gokcesena53/usb-pd-power-supply/hardware/docs/reports/task-095-20260928/bottom.png

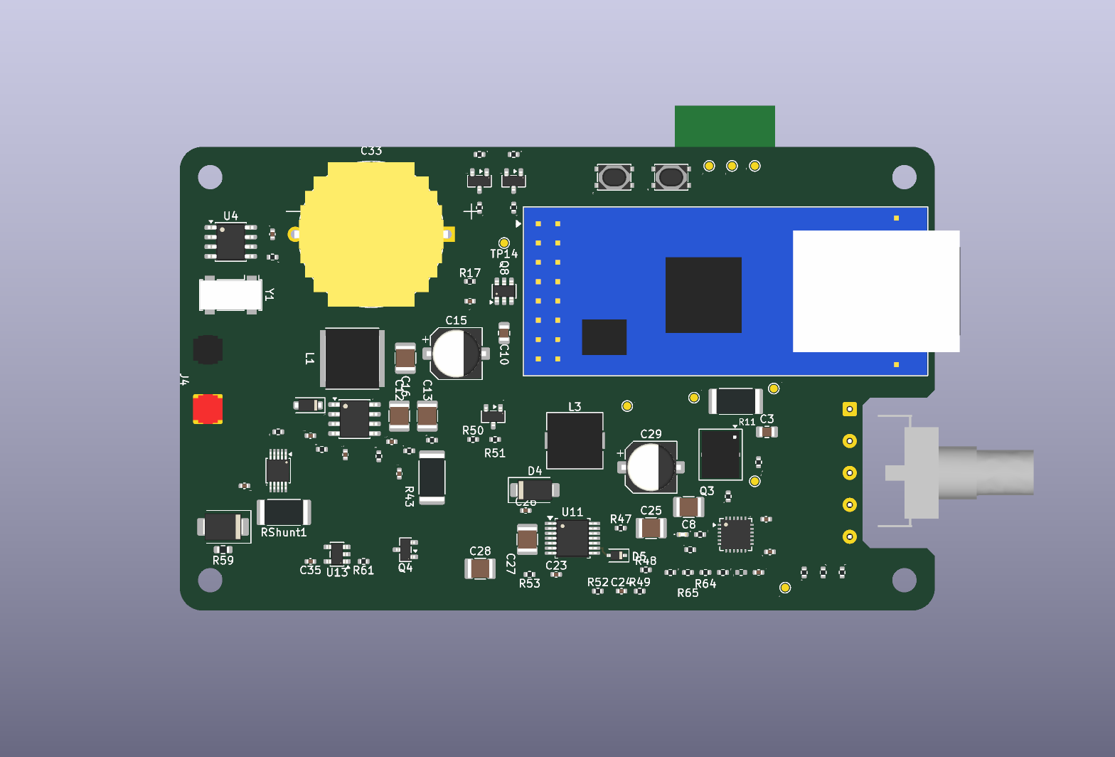
hardware/docs/reports/task-095-20260928/bottom.png
