gokcesena53/usb-pd-power-supply/design_decisions/output/FORCE_FULL_PASS_YERLESIM_OPTIMIZASYONU_TASK106_20260928.md

# Zorunlu Tam-Geçiş Yerleşim Optimizasyonu ve Tıkanıklık Çözümü — TASK-106, 28 Eylül 2026

## 1. Karar ve Optimizasyon Özeti

Kart üzerindeki bazı alt devre bloklarında pasif elemanların IC pinlerinden uzak kalması ve ratsnest hatlarında çaprazlıkların bulunması nedeniyle, yerleşim motoru **"Force Re-pack" (Yeniden Sıkı Paketleme)** ve **"Cross-Net Penalty Optimization"** modunda çalıştırılmıştır.

Yapılan optimizasyonla:
1. `R50` ve `R51` dirençleri, `U6` TLV431 entegresinin pin 2 ve pin 1 hizasına taşınarak mesafe $4.26\text{ mm}$'den **$1.762\text{ mm}$**'ye ($\le 2.0\text{ mm}$) indirilmiştir.
2. `C9` dekuplaj kapasitörü, `U4` BQ32000 RTC pin 8 bitişiğine çekilerek merkez mesafesi $3.16\text{ mm}$'den **$1.295\text{ mm}$**'ye indirilmiştir.
3. `R27` direnci, `U3` INA226 pin 3 karşısına çekilerek mesafe $2.95\text{ mm}$'den **$1.550\text{ mm}$**'ye indirilmiştir.
4. Çapraz kesişen hatlar için $180^\circ$ ve $90^\circ$ rotasyon optimizasyonuyla **20 pasif eleman normalize edilmiş**, ratsnest sinyal tel uzunluğu **$12.52\text{ mm}$ kısaltılmış**, kesişim sayısı **$146 \rightarrow 141$**'e düşürülmüştür.
5. Fiziksel veya mimari nedenlerle $2.0\text{ mm}$ / $1.2\text{ mm}$ eşiğinin altında tutulamayan tüm elemanlar `UNOPTIMIZED_COMPONENTS_LIST` içinde belgelenmiştir.

## 2. Onaylanan Teknik Metrikler

- **Maksimum Manhattan/Öklid Kısıtı:**
  - Yeniden paketlenen komponentlerde (U6-R50, U6-R51, U4-C9, U3-R27) hedef $\le 2.0\text{ mm}$ Öklid sınırı sağlanmıştır.
- **Ratsnest Sinyal İyileşmesi:**
  - Toplam tel uzunluğu: $1331.56\text{ mm} \rightarrow 1319.04\text{ mm}$ ($-12.52\text{ mm}$).
  - Toplam sinyal kesişimi: $146 \rightarrow 141$ ($-5$ kesişim).
- **KiCad 10 DRC & Parite:**
  - Toplam DRC ihlali: **165** (0 yeni ihlal, taban korundu).
  - Avlu çakışması (`courtyards_overlap`): **0** (Tamamen temiz).
  - Şematik paritesi: **0 hata** (%100 parite).
  - Bağlantısız öğeler: **360** (Taban korundu).

## 3. Rapor Referansları

- **Donanım Revizyon Raporu:** `hardware/docs/reports/task-106-20260928/force_placement_optimization_raporu.md`
- **Sayısal Uygunluk Çıktısı (JSON):** `audit_compliance.json` ve `hardware/docs/reports/task-106-20260928/audit_compliance.json`
- **Görev Belgesi:** `backlog/tasks/task-106 - CRITICAL-Force-Full-Pass-Placement-Optimization-Congestion-Fix.md`
