gokcesena53/usb-pd-power-supply/design_decisions/output/LM74801_YERLESIM_TASK074_20260924.md

# LM74801 çıkış anahtarı ve ideal diyot grubu ilişkisel yerleşimi — TASK-074, 24 Eylül 2026

LM74801 çıkış anahtarı ve ideal diyot grubunun 10 footprint üyesi (U12, Q5, C30–C32,
D6, R54–R56, R58) F.Cu katmanında ortak source (common-source) topolojisi, gate sürme,
dV/dt yumuşak açılış, charge pump kapasitesi ve çıkış gücü akışına göre ilişkisel
olarak yerleştirildi. On footprint'in grup üyeliği, UUID, pad/net bağlantıları ve
F.Cu yüzü korundu. Kart dışındaki geçici blok alanı (x≈105–123, y≈52–66 mm)
korunmuştur; nihai kart içine taşıma ve genel routing TASK-085/TASK-008 kapsamındadır.

[Önce görünüm](../../hardware/docs/reports/task-074-20260924/before.svg) ·
[Sonra ve koridorlar](../../hardware/docs/reports/task-074-20260924/after.svg) ·
[KiCad F.Cu katman çıktısı](../../hardware/docs/reports/task-074-20260924/board-top.svg) ·
[x/y/açı/yüz ve pad ölçümleri](../../hardware/docs/reports/task-074-20260924/verification.json)

## Kaynak, pin ve yerleşim kuralı

- **Texas Instruments LM7480-Q1 (SNOSD95C, Nisan 2020 – Rev. Aralık 2020, s. 35–36):**
  1. *İdeal diyot katı (§12.1):* U12 Pin 1 (`DGATE`), Pin 2 (`A` / `SRC_COMMON`) ve
     Pin 12 (`C` / `SW_OUT`) doğrudan Q5B MOSFET'inin GATE (Pin 4), SOURCE (Pins 1,3)
     ve DRAIN (Pins 5,6) uçlarına yakın bağlandı (U12.1–Q5.4 mesafesi 3,94 mm;
     U12.2–Q5.3 5,02 mm; U12.12–Q5.5 7,68 mm).
  2. *Yük ayırma / load disconnect katı (§12.1):* U12 Pin 8 (`GATE_DRV` / HGATE) ve
     Pin 9 (`OUT` / `SRC_COMMON`) doğrudan Q5A MOSFET'inin GATE (Pin 2) ve SOURCE
     (Pins 1,3) uçlarına bağlandı (U12.8–Q5.2 mesafesi 9,09 mm).
  3. *Ortak Source yapılandırması (Şekil 12-2, Common Source Configuration):*
     Q5 0° yönlendirmesinde üst yarıda termal drain padleri (sol Drain A: pins 7,8
     `PD_VBUS_SENSED`; sağ Drain B: pins 5,6 `SW_OUT`), alt yarıda leaded bacaklar
     (Pin 1 SRC, Pin 2 HGATE, Pin 3 SRC, Pin 4 DGATE) bulunur. Gate ve source
     bağlantıları yüksek akım drain dökümlerinin dışından bağımsız çıkarıldı.
  4. *Decoupling ve Charge Pump (§12.1):*
     - C32 (100 nF, 0402): U12 Pin 10 (`V_PRE`) ve Pin 7 (`GND`) hemen bitişiğine
       yerleştirildi (pad merkezleri 3,40 mm ve 2,57 mm).
     - C31 (220 nF, 0603): U12 Pin 11 (`CAP`) ve Pin 10 (`V_PRE`) arasında charge
       pump kapasitesidir. TI kuralı gereğince MOSFET gövdesinin ısısından
       etkilenmemesi için U12'nin sağ tarafına (Q5'in uzağına) yerleştirildi
       (pad merkezleri 3,67 mm ve 3,21 mm).
  5. *Gate Kırpma / Zener Koruması:* D6 (BZT52C12 SOD-123) Q5A Gate (Pin 2) ile
     Common Source (Pin 1) arasına bağlandı (D6.1–Q5.2 5,48 mm; D6.2–Q5.1 2,79 mm).
     Katot `GATE_DRV`'de, anot `SRC_COMMON`'da VGS gerilimini 12 V ile sınırlar.
  6. *Yumuşak Açılış (Soft-Start dV/dt):* R54 (1 kΩ) ve C30 (22 nF) Q5A Gate hattına
     bağlandı; C30 referans yazısı lehim maskesi açıklığına basmayacak şekilde
     alt boşluğa ayarlandı.
  7. *Aşırı Gerilim ve Enable:* R55 (237 kΩ) ve R56 (10 kΩ) gerilim bölücüsü U12.5
     (`OV_SENSE`) girişine; R58 (100 kΩ) pull-down direnci U12.6 (`SW_EN`) girişine
     yerleştirildi.
  8. *Termal Pad:* U12 altındaki EP (RTN, Pin 13) datasheet gereğince boştadır,
     GND'ye bağlanmaz.

| Alt Devre / Koridor | Elemanlar ve Pad/Net Yönü |
| --- | --- |
| Güç Girişi (Q5A) | `PD_VBUS_SENSED` sol taraftan Q5 Pins 7,8 Drain A dökümüne girer. |
| Ortak Source | Q5A ve Q5B Pins 1,3 `SRC_COMMON` ortak ara düğümüdür. |
| Güç Çıkışı (Q5B) | Q5 Pins 5,6 Drain B `SW_OUT` dökümünden sağa doğru INA226/J4 yönüne çıkar. |
| DGATE Sürüşü | U12.1 → Q5.4 (`DGATE`) ideal diyot hızlı anahtarlama yolu (3,94 mm). |
| HGATE Sürüşü & dV/dt | U12.8 → Q5.2 (`GATE_DRV`), D6 Zener koruması ve R54–C30 yumuşak açılış devresi. |
| Kaynak ve Katot Algılama | U12.2/9 → Q5.1/3 (`SRC_COMMON`); U12.12 → Q5.5/6 (`SW_OUT`). |
| Besleme & Charge Pump | C32 (121,5; 58,0) `V_PRE` bypass; C31 (122,0; 54,5) `CAP`–`VS` charge pump. |
| Mantık & Algılama | R55/R56 `OV_SENSE` bölücüsü ve R58 `SW_EN` pull-down direnci U12 altına yerleştirildi. |

## Komşuluk, yüz seçimi ve devir notları

1. **Güç Akışı:**
   - Giriş: Sol taraftan `PD_VBUS_SENSED` (pre-boost U11 / buck U5 hatlarından).
   - Çıkış: Sağ tarafa `SW_OUT` (INA226 akım şöntü R1 ve J4 panel çıkış konnektörüne).
2. **Yüz Seçimi Koordinasyonu (TASK-065 Devri):**
   - Bu blok başlangıç olarak `F.Cu` katmanında tutuldu.
   - TASK-085 / TASK-008'de kart içine taşınırken INA226 grubunun B.Cu'da olduğu ve LCD
     izdüşüm alanının (x=63,52…141,62; y=72,28…127,72 mm) top zarf kısıtları göz önüne
     alınarak, gerekirse INA226 ile birlikte alt yüze (B.Cu) flip edilmesi incelenmelidir.

## Doğrulama

- `kicad-cli pcb drc --schematic-parity`:
  - **DRC ihlalleri:** **146 → 146** (yeni courtyard, clearance, short, edge veya mask ihlali: **0**).
  - **Bağlantısız öğeler:** **360 → 360** (tamamlanmamış genel routing envanteri korundu).
  - **Schematic parity:** **0 → 0**.
- **Courtyard kontrolü:** 10 eleman arasında minimum courtyard aralığı **0,350 mm** (Q5–D6 arası); çakışma **0**.
- **Ankrajlar ve izler:** J7, J3, J9, H1–H4, D5, U11 konum/açı/yüz ankrajları ve mevcut iz UUID'leri tamamen korundu.

Kanıt dosyaları:
- [DRC önce](../../hardware/docs/reports/task-074-20260924/drc-before.json)
- [DRC sonra](../../hardware/docs/reports/task-074-20260924/drc-after.json)
- [Doğrulama ve pad ölçüm verileri](../../hardware/docs/reports/task-074-20260924/verification.json)
- [Yerleşim betiği](../../hardware/docs/reports/task-074-20260924/place.py)
- [Doğrulama betiği](../../hardware/docs/reports/task-074-20260924/verify.py)
