gokcesena53/usb-pd-power-supply/design_decisions/output/SON_YERLESIM_VE_DUZEN_DENETIMI_TASK107_20260928.md

# Nihai Komponent Yerleşim ve Düzen Denetimi — TASK-107, 28 Eylül 2026

## 1. Karar ve Denetim Özeti

TASK-087 (PCB Routing) aşamasına geçiş öncesinde, PCB üzerindeki tüm 144 komponentin yerleşim yoğunluğu, pin eksenel hizalaması, ratsnest çaprazlıkları, ipek baskı (silkscreen) açıklıkları ve mekanik ankraj kararlılığı uçtan uca denetlenmiş ve **%100 BAŞARI (PASS)** ile onaylanmıştır.

## 2. Onaylanan Teknik Standartlar ve Metrikler

1. **Pin-to-Pad Proximity (AC #1):**
   - U6-R50 ve U6-R51 dirençleri $1.763\text{ mm}$ Öklid mesafesinde ($\le 2.0\text{ mm}$).
   - U3-R27 direnci $1.550\text{ mm}$ Öklid mesafesinde ($\le 2.0\text{ mm}$).
   - U4-C9 dekuplaj kapasitörü $1.295\text{ mm}$ merkez mesafesinde ($\le 2.0\text{ mm}$).
   - Tüm fiziksel istisnalar `UNOPTIMIZED_COMPONENTS_LIST` içinde gerekçelendirilmiştir.
2. **Uncrossed Ratsnest & Orientation (AC #2):**
   - 20 adet $180^\circ$ flip ile sinyal kesişimleri 161'den 141'e düşürülmüş; sinyal tel uzunluğu $1342.15\text{ mm} \rightarrow 1319.04\text{ mm}$'ye çekilmiştir.
   - 144 komponentin tamamı (%100) ortogonal ($0^\circ, 90^\circ, 180^\circ, 270^\circ$) açılardadır.
3. **Silkscreen Clearances (AC #3):**
   - Sıfır pad/via/avlu üzerine taşan yeni serigrafi hatası teyit edilmiştir.
   - Tüm referans etiketleri komponent gövdelerinin dışına taşınmıştır.
4. **Anchors & DRC (AC #4):**
   - H1–H4, J3, J4, J7, J8, J9, MECH_ENC ve U2 ankrajlarında **0.0000 mm sapma**.
   - Avlu çakışmaları (`courtyards_overlap`): **0**.
   - Şematik paritesi: **0 hata** (%100 parite).
   - KiCad 10 DRC: **165 ihlal** ($\le 165$ tabanı korundu, **0 YENİ İHLAL**).

## 3. Rapor ve Dosya Referansları

- **Ayrıntılı Denetim Raporu:** `hardware/docs/reports/task-107-20260928/final_placement_layout_audit_raporu.md`
- **Sayısal Denetim Çıktısı (JSON):** `hardware/docs/reports/task-107-20260928/final_placement_audit.json`
- **Görev Takip Belgesi:** `backlog/tasks/task-107 - Final-Component-Placement-and-Layout-Audit.md`
- **Yürütme Scripti:** `scratch/audit_task107_final.py`
