gokcesena53/usb-pd-power-supply/design_decisions/output/TPS55340_YERLESIM_TASK072_20260924.md

# TPS55340 ilişkisel yerleşimi — TASK-072, 24 Eylül 2026

U11, D5 ve aralarındaki mevcut `BOOST_FB` izi ankraj olarak kaldı. Diğer 14
grup üyesi B.Cu üzerinde güç ve hassas sinyal sırasına göre düzenlendi.
Blok hâlâ TASK-067'nin kart dışı geçici alanındadır; kart içindeki son konum
ve yeni güç izleri bu kararın parçası değildir.

[Önce](../../hardware/docs/reports/task-072-20260924/before.svg) ·
[Sonra ve ayrılmış koridorlar](../../hardware/docs/reports/task-072-20260924/after.svg) ·
[Ölçüm ve x/y/açı/yüz envanteri](../../hardware/docs/reports/task-072-20260924/verification.json)

## Üretici kuralı ve uygulama

Kaynak: [TI TPS55340 veri sayfası SLVSBD4E, §10.1–10.3, s. 28,
Şekil 10-1](https://www.ti.com/lit/ds/symlink/tps55340.pdf).
Şekil 10-1 QFN pin dizilimini gösterir; bu karttaki U11 HTSSOP-14'tür.
Bu yüzden pin numaraları şekilden alınmadı; PCB'deki gerçek pad/netler
esas alındı. TASK-069'un tüm gruplar için kaynak tablosu henüz yoktur;
bu gruba ait kaynak ve ankraj denetimi burada yapıldı.

| TI kuralı | PCB karşılığı / doğrulama |
| --- | --- |
| SW iz uzunluğu ve alanı küçük; regülatörün altında GND düzlemi | L3.1 (72,75;42,50), D4.2 (72,80;49,00), U11.1/2 (72,712;53,39/54,04) aynı B.Cu koridorunda. SW için x≈72–74 mm, y≈42–54 mm ayrıldı; genişliğini bitmiş routing belirleyecek. İç GND düzlemi korunmalı, SW bakırı FB tarafına genişletilmemeli. |
| İç FET–D4–Cout yüksek akım döngüsünü kısalt | D4.1 V_PRE (76,80;49,00) → C27.1 V_PRE (75,80;54,025) pad merkezleri 5,12 mm. C27.2 GND (75,80;56,975) → U11 termal GND dönüşü için B.Cu alanı ayrıldı. C28.1 V_PRE (83,475;64,00) ikinci çıkış deposudur; mevcut U6/R50/R51/C16 alanı nedeniyle uzak kaldı. C28'in güç bağlantısı TASK-073 ile yeniden kontrol edilmeli. |
| VIN bypass'u VIN/AGND'a yakın | C26.1 PD_VOUT (76,48;51,70) → U11.3 VIN (72,712;54,69) pad merkezleri 4,81 mm. C26.2 GND'den U11.15/GND'a kısa dönüş ve via alanı ayrıldı. C25/C29 daha büyük giriş depolarıdır; C29.1 (62,20;46,00) → L3.2 (66,35;42,50) 5,43 mm. Bu uzaklıklar TI'nin sayısal limitleri değil, bu yerleşimin ölçümleridir. |
| AGND/PGND ve PowerPAD aynı katmanda doğrudan bağlanır; termal via kullanılır | U11.6/7/11–14 ve 15 GND. U11 altındaki B.Cu GND alanı ve termal via dizisi için yer bırakıldı. Via/zone henüz eklenmedi; delik çapı, maske ve lehim emilmesi routing/üretim kontrolünde seçilmeli. |
| FB ve COMP'ı anahtarlama alanından uzak tut | U11.8 COMP (66,987;57,29) → R52/C24 ağı sol-alt çıkışta; U11.9 FB (66,987;56,64) → D5.2 ve R48/R49 sol-alt tarafta. SW koridoru sağ/üstte. R47 FREQ ve C23 SS de sinyal tarafında. Sessiz GND dönüşü U11.11–14/15'e yönelir; L3/D4 SW üzerinden geçmez. |

Yukarıdaki oklar **planlanan koridorlardır**, tamamlanmış bakır izi değildir.
SW, giriş, V_PRE ve GND yüksek akım alanları B.Cu'da tutulmalı; via dizisi
yalnızca dağıtım/termal dönüşte kullanılmalıdır. Diyot D4.2 SW, D4.1 V_PRE;
D5.2 BOOST_FB anot, D5.1 EN_CTRL katot. Polarite ve pad netleri şemayla
aynı kaldı.

## Buck sınırı ve sessiz dönüş

D5.1 EN_CTRL x=62,97; y=57,60'tan U6.2 x=80,885; y=54,602 ve R50.1
x=82,185; y=60,57 yönüne gider. D5–U11 FB izinin yanında güç SW bakırı
geçirilmez. EN_CTRL/V_X ve R50/R51/U6 REF düğümü buck grubunun hassas
tarafıdır; TASK-073 bu elemanları hareket ettirirse D5.1'e ayrılan üst/sağ
koridor ve U11 GND'den ayrı sessiz referans dönüşü birlikte kontrol edilmeli.
R43'ün V_PRE/EN_CTRL bağlantısı ve ısıl alanı buck grubuna aittir.

## Kontrol ve sınırlar

- D5.2–U11.9 aynı dört UUID'li B.Cu segmentiyle via olmadan bağlı:
  **2,584607 mm ≤10 mm**. U11/D5 ve segmentler yerinden oynatılmadı.
- Grup 16 üye, grup adı, footprint UUID, pad/net listesi ve B.Cu yüzü korundu.
  J3/J9/H1–H4 sabit ankrajlarına dokunulmadı.
- `kicad-cli pcb drc --schematic-parity`: önce/sonra **146/146** ihlal,
  **360/360** bağlantısız öğe, **0/0** şema eşleşme hatası. Yeni courtyard,
  clearance, kısa devre veya mask köprüsü yok. 146 mevcut ihlal: 63 yazı
  yüksekliği, 63 yazı kalınlığı, 15 drill aralığı, 4 J7 hole clearance,
  1 D10 silk over copper. Bağlantısız 360 öğe, genel routing henüz
  tamamlanmadığı için ayrı tutuldu.
- C27 yakın çıkış deposuna rağmen C28'in pad'i D4'ten uzakta. TASK-073
  buck yerleşimi ve TASK-085 toplu denetiminde güç dönüş alanı ile C28
  konumu tekrar değerlendirilmeli. Nihai kısa akım döngüsü routed PCB'de
  ölçülmeden TI yerleşim önerisinin tamamlandığı söylenemez.

Kanıt: [DRC önce](../../hardware/docs/reports/task-072-20260924/drc-before.json),
[DRC sonra](../../hardware/docs/reports/task-072-20260924/drc-after.json),
[doğrulama betiği](../../hardware/docs/reports/task-072-20260924/verify.py).
