gokcesena53/usb-pd-power-supply/design_decisions/logs/PROMPT_steplayout-critical-routing_20260912_233540.md

AOZ1284PI buck power-stage placement and routing; USB-C to dual-output 5 A path; R11 and INA228 Kelvin sense routing; zones refilled; DRC 0 violations.
