gokcesena53/usb-pd-power-supply/design_decisions/output/TASARIM_RAPORLARI_20260911.md

# Tasarım dokümanları

11 Eylül 2026 — Güncel teslim paketi

- [TÜM BAĞLANTI KONTROLÜ VE MÜHENDİSLİK AÇIKLAMASI](C:/Users/Slayer/Desktop/masaüstü%20güç%20kaynağı/output/pdf/TUM_BAGLANTI_KONTROLU_20260911.pdf)
- [00_DEGISIKLIK_RAPORU](C:/Users/Slayer/Desktop/masaüstü%20güç%20kaynağı/output/pdf/bloklar-20260911/00_DEGISIKLIK_RAPORU.pdf)
- [01_USB_C_INPUT](C:/Users/Slayer/Desktop/masaüstü%20güç%20kaynağı/output/pdf/bloklar-20260911/01_USB_C_INPUT.pdf)
- [02_USB_PD_CONTROLLER](C:/Users/Slayer/Desktop/masaüstü%20güç%20kaynağı/output/pdf/bloklar-20260911/02_USB_PD_CONTROLLER.pdf)
- [03_MCU](C:/Users/Slayer/Desktop/masaüstü%20güç%20kaynağı/output/pdf/bloklar-20260911/03_MCU.pdf)
- [04_RTC_BATTERY](C:/Users/Slayer/Desktop/masaüstü%20güç%20kaynağı/output/pdf/bloklar-20260911/04_RTC_BATTERY.pdf)
- [05_TFT](C:/Users/Slayer/Desktop/masaüstü%20güç%20kaynağı/output/pdf/bloklar-20260911/05_TFT.pdf)
- [06_ENCODER](C:/Users/Slayer/Desktop/masaüstü%20güç%20kaynağı/output/pdf/bloklar-20260911/06_ENCODER.pdf)
- [07_POWER_GENERATION](C:/Users/Slayer/Desktop/masaüstü%20güç%20kaynağı/output/pdf/bloklar-20260911/07_POWER_GENERATION.pdf)
- [08_POWER_SENSING](C:/Users/Slayer/Desktop/masaüstü%20güç%20kaynağı/output/pdf/bloklar-20260911/08_POWER_SENSING.pdf)
- [09_POWER_OUTPUT](C:/Users/Slayer/Desktop/masaüstü%20güç%20kaynağı/output/pdf/bloklar-20260911/09_POWER_OUTPUT.pdf)
- [Güncel BOM — Excel](C:/Users/Slayer/Desktop/masaüstü%20güç%20kaynağı/output/BOM_PRELIMINARY_20260911.xlsx)
- [Güncel BOM — CSV](C:/Users/Slayer/Desktop/masaüstü%20güç%20kaynağı/output/BOM_PRELIMINARY_20260911.csv)
- [PCB katman kararı, küçültme planı ve BOM durumu](C:/Users/Slayer/Desktop/masaüstü%20güç%20kaynağı/output/LAYOUT_VE_BOM_DURUMU_20260911.md)
- [PCB yerleşim revizyonu 1](C:/Users/Slayer/Desktop/masaüstü%20güç%20kaynağı/output/PCB_YERLESIM_REV1_20260912.md)
- [PCB layout uygulama yol haritası](C:/Users/Slayer/Desktop/masaüstü%20güç%20kaynağı/output/PCB_LAYOUT_YOL_HARITASI_20260912.md)
- [KiCad 10 layout adım adım uygulama rehberi](C:/Users/Slayer/Desktop/masaüstü%20güç%20kaynağı/output/KICAD10_LAYOUT_ADIM_ADIM_20260912.md)

## Açık tasarım konuları

- IRF7855 / AP33772S gate sürüş uyumluluğu.
- TFT arka ışığı için regüle akım kaynağı.
- Buck L/D ve bias koşulu doğrulanmış MLCC MPN seçimi.
- PCB boş: bakır, RF, ısıl, yerleşim ve DRC doğrulaması yapılmadı.
- Birincil CR2032: RTC trickle charge kapalı olmalı.
- Üretim BOM'u için sarı satırlardaki kesin üretici parça numaraları ve MLCC DC-bias doğrulaması kapanmalı.
