gokcesena53/usb-pd-power-supply/design_decisions/reports/layout-20260911/gnd-routing-correction-report.md

# GND Routing Correction Report

Date: 2026-09-13

## Corrected items

- Removed 214 user-added GND routing segments that formed long daisy-chain return paths on F.Cu.
- Restored and retained the 16 short local GND traces used by the AOZ1284PI buck power stage and its control network.
- Added a GND copper zone on F.Cu with 0.25 mm clearance.
- Retained the existing GND zones on GND_PLANE and B.Cu.
- Added local 0.60/0.30 mm GND vias around the main IC, USB, ESP32, RTC/TFT and power clusters.
- Removed temporary grid vias so the remaining signal routes are not obstructed.
- Final GND via count: 48.
- Changed the USB-C J1 footprint GND zone connection to solid fill so its B1/B12 pads connect without starved thermal spokes.
- The ESP32 antenna copper keepout remains active on all copper layers.
- AOZ1284PI exposed pad remains on PD_VOUT/VIN; it was not connected to GND.

## Verification

- Final DRC: 0 errors, 0 warnings.
- No GND entries remain in the unconnected-item report.
- The board still has 131 unrouted items on non-GND nets. These are the remaining layout work and are not DRC shorts or clearance failures.

## Next routing stage

Place R2/R3 as a matched USB pair near ESP32-C6 USB pins, then route USB_DP/USB_DM over a continuous GND reference. Route +3.3V distribution and local decoupling next. General GND stitching should be finalized only after all signal routes are complete.
