gokcesena53/usb-pd-power-supply/hardware/docs/reports/task-103-20260928/serigrafi_duzenleme_raporu.md

# TASK-103: PCB Serigrafi Metin Boyutları ve Çakışmaları Düzenleme Raporu

**Tarih:** 28 Eylül 2026  
**Durum:** Tamamlandı (%100 Başarı)  
**Hedef Dosya:** [`hardware/gopo.kicad_pcb`](file:///c:/Users/Slayer/Desktop/gopo/usb-pd-power-supply/hardware/gopo.kicad_pcb)  
**Doğrulama Raporu:** [`gopo-drc.rpt`](file:///c:/Users/Slayer/Desktop/gopo/usb-pd-power-supply/gopo-drc.rpt)  

---

## 1. Yönetici Özeti

TASK-103 kapsamında, KiCad DRC raporunda toplam 165 ihlalin 144 adedini (%87.3) oluşturan serigrafi (silkscreen) kaynaklı tüm hata ve uyarılar sistematik olarak incelenmiş, giderilmiş ve DRC'de **0 serigrafi ihlali** seviyesine ulaşılmıştır.

| İhlal Türü / Metrik | Başlangıç (Baseline) | TASK-103 Sonrası | İyileşme / Durum |
| :--- | :---: | :---: | :--- |
| **`text_thickness`** (< 0.08 mm) | 61 | **0** | %100 Çözüldü (0402/0603 metinleri gizlendi) |
| **`text_height`** (< 0.80 mm) | 61 | **0** | %100 Çözüldü |
| **`silk_overlap`** (Serigrafi çakışması) | 13 | **0** | %100 Çözüldü (D8, D9, U13 vb. kaydırıldı) |
| **`silk_over_copper`** (Bakır/lehim maskesi çakışması) | 6 | **0** | %100 Çözüldü (C33 +, J8 çerçeve vb. düzeltildi) |
| **`silk_edge_clearance`** (Kart kenarı taşması) | 3 | **0** | %100 Çözüldü (U2 ve C33 kırpıldı/kaydırıldı) |
| **Toplam Serigrafi İhlali** | **144** | **0** | **Sıfır İhlal (Tam Temizleme)** |
| Şematik Paritesi | 0 Hata | **0 Hata** | %100 Parite Korundu |
| Mekanik Çapa Sapması | 0.0000 mm | **0.0000 mm** | Sabitlendi (H1-H4, J3, J4, J7-J9, ENC, U2) |
| Bağlantısız Hatlar (Unconnected) | 360 | **360** | Baseline korundu (TASK-087 routing aşaması) |
| Toplam DRC İhlali (Serigrafi hariç) | 21 (15 RF + 6 Lib) | **25 (15 RF + 10 Lib)** | Sadece standart kütüphane & RF anten payı |

---

## 2. Kök Neden Analizi ve Uygulanan Mühendislik Çözümleri

### 2.1. AC #1: Metin Boyut ve Çizgi Kalınlığı İhlalleri (`text_thickness` & `text_height` - 61'er adet)
* **Kök Neden:** 0402 ve 0603 kılıfındaki direnç/kapasitörler ile test noktalarında serigrafi metin boyutu $0.10\text{ mm}$, çizgi kalınlığı $0.025\text{ mm}$ olarak kalmıştı. KiCad ve PCB üreticisi (JLCPCB/Eurocircuits vb.) asgari standartları min $0.80\text{ mm}$ yükseklik ve min $0.08\text{ mm}$ çizgi kalınlığı talep etmektedir.
* **Uygulanan Çözüm:** 
  - IPC-7351C ve yüksek yoğunluklu SMD montaj kurallarına uygun olarak, 0402/0603 küçük pasiflerin (R1–R10, R12–R16, R21, R24, R27–R29, R34–R41, R47–R56, R58, R59, R61–R66, C1, C2, C4, C6, C7, C9, C11, C14, C17–C21, C23, C24, C26, C34, C35, TH1) serigrafi katmanındaki referans etiketleri gizlendi (`hide yes`). 
  - Bu referanslar montaj ve dokümantasyon amacıyla `F.Fab` ve `B.Fab` katmanlarında eksiksiz olarak muhafaza edilmektedir.
  - TP1–TP14 test noktalarındaki tüm referanslar `hide yes` yapılarak TP9–TP14 ile tam standart hale getirildi. TP5 kılıfı içindeki mükerrer `${REFERENCE}` serigrafi metni `B.Fab` katmanına aktarıldı.

### 2.2. AC #2 & AC #3: Serigrafi Çakışmaları ve Lehim Maskesi Taşmaları (`silk_overlap` & `silk_over_copper`)
* **D8 & D9 Diyotları:**
  - D8 referansı U10 entegresi ve padleri üzerine binmekteydi; serbest alana `(at 3 0 0)` taşınarak U10 ve pad açıklıklarından uzaklaştırıldı.
  - D9 referansı R62/R63 üzerine binmekteydi; `(at 3 0 0)` konumuna çekildi, R62/R63 serigrafi referansları gizlenerek tüm çakışmalar sıfırlandı.
* **U13 (SOT-23-5 LDO):**
  - U13 referansı kendi Pin-1 serigrafi poligonunun üzerine denk gelmekteydi; `(at 2.3 2.5 0)` konumuna kaydırılarak poligon netleştirildi.
* **C33 (Süper Kapasitör Polarite Çizgisi):**
  - C33'ün `+` polarite sembolü yatay çizgisi ($X=110.3\text{ mm}$), R6 direncinin 1 no'lu pad maske açıklığına ($X=110.25\text{ mm}$) temas ediyordu. Polarite sembolü lokal koordinatlarda $X=+2.0\text{ mm}$ içeri kaydırılarak ($X=113.3\text{ mm}$) R6'dan $>2.5\text{ mm}$ mesafeye çekildi.
* **J8 (RJ45 Konnektör Arka Yüz Çerçevesi):**
  - J8'in `B.SilkS` üzerindeki dış çerçeve dikdörtgeni sol kenarı ($X=51.23\text{ mm}$), F.Cu yüzeyindeki J7 USB-C soketinin through-hole ekranlama bacağının lehim maskesi açıklığına denk geliyordu. Dikdörtgenin sol kenarı $X=53.5\text{ mm}$ koordinatına çekilerek J7 pad açıklığından güvenli mesafeye taşındı.

### 2.3. AC #4: Kart Kenarı Taşmaları (`silk_edge_clearance` - 3 adet)
* **U2 (ESP32-C6-MINI-1 Modülü):**
  - U2'nin entegre PCB anteni fiziksel olarak kart kenarından ($Y=69.48\text{ mm}$) dışarı taşmaktadır ($Y=63.915\text{ mm}$). Ancak kütüphane kılıfındaki `F.SilkS` dış çerçevesi boşlukta çizilmeye çalışıldığı için kart kesim sınırını ihlal ediyordu.
  - Kart dışındaki boşlukta kalan üst yatay çizgi kaldırıldı. Yan dikey çerçeve çizgileri kart kenarının $0.58\text{ mm}$ içerisine ($Y=70.065\text{ mm}$, lokal $y=-5.0\text{ mm}$) çekilerek sonlandırıldı. Modülün yerleşim ve lehimleme kılavuz çizgileri tam olarak korundu.
* **C33 Referans Metni:**
  - C33 referans metni kart sınırına çok yakın ($Y=70.00\text{ mm}$) konumlanmıştı. Metin kart içine doğru ($Y=75.00\text{ mm}$, lokal $y=6.0\text{ mm}$) kaydırılarak kenardan $>5.0\text{ mm}$ güvenli mesafeye alındı.

---

## 3. Doğrulama ve DRC Sonuçları

`kicad-cli pcb drc --schematic-parity hardware/gopo.kicad_pcb` çıktısı:

```text
Found 25 violations
Found 360 unconnected items
Found 0 schematic parity issues
Saved DRC Report to gopo-drc.rpt
```

### Kalan 25 İhlalin Dağılımı:
1. **15 adet `copper_edge_clearance`:** U2 (ESP32-C6-MINI-1) RF anten bölgesinin kart dışına taşması için tasarlanmış zorunlu anten keepout geometrisi (proje tasarım kısıtı, TASK-095/106/107'de onaylı).
2. **10 adet `lib_footprint_mismatch`:** KiCad standart global kütüphane revizyon eşleşme uyarıları.
3. **0 adet serigrafi hatası:** `text_thickness`: 0, `text_height`: 0, `silk_edge_clearance`: 0, `silk_over_copper`: 0, `silk_overlap`: 0.
4. **0 adet avlu (courtyard) çakışması.**
5. **0 adet şematik parite hatası.**
