gokcesena53/usb-pd-power-supply/backlog/tasks/task-013 - C33-footprintini-numune-ile-dogrula.md

---
id: TASK-013
title: C33 footprint'ini numune ile doğrula
status: To Do
assignee: []
created_date: '2026-09-22 18:46'
updated_date: '2026-09-22 19:15'
labels:
  - sample-eval
milestone: m-1
dependencies: []
priority: medium
ordinal: 120000
---

## Acceptance Criteria
<!-- AC:BEGIN -->
- [ ] #1 Korchip_DCL_H-Type footprint'i numuneye uyuyor
<!-- AC:END -->

## Definition of Done
<!-- DOD:BEGIN -->
- [ ] #1 Kanıt (ERC/netlist/ölçüm/commit) Implementation Notes'a yazıldı
- [ ] #2 Karar değiştiyse design_decisions/ ve CHANGES.TXT güncellendi
<!-- DOD:END -->
