gokcesena53/usb-pd-power-supply/backlog/tasks/task-016 - 5-V-profilde-AOZ1284-TPS55340-kararliligini-olc.md

---
id: TASK-016
title: 5 V profilde AOZ1284 + TPS55340 kararlılığını ölç
status: To Do
assignee: []
created_date: '2026-09-22 18:46'
updated_date: '2026-09-22 19:15'
labels:
  - bring-up
milestone: m-2
dependencies:
  - TASK-015
references:
  - design_decisions/USB_PD_REV_C_tasarim_kararlari_handoff.md
ordinal: 123000
---

## Acceptance Criteria
<!-- AC:BEGIN -->
- [ ] #1 Tam yükte iki regülatör kararlı
- [ ] #2 Attach anında USB_VBUS efektif kapasitesi ≤10 uF
<!-- AC:END -->

## Definition of Done
<!-- DOD:BEGIN -->
- [ ] #1 Kanıt (ERC/netlist/ölçüm/commit) Implementation Notes'a yazıldı
- [ ] #2 Karar değiştiyse design_decisions/ ve CHANGES.TXT güncellendi
<!-- DOD:END -->
