gokcesena53/usb-pd-power-supply/backlog/tasks/task-017 - 3.3-V-PPSte-V_PRE-regulasyonunu-ve-boost-kararliligini-olc.md

---
id: TASK-017
title: 3.3 V PPS'te V_PRE regülasyonunu ve boost kararlılığını ölç
status: To Do
assignee: []
created_date: '2026-09-22 18:46'
updated_date: '2026-09-22 19:15'
labels:
  - bring-up
milestone: m-2
dependencies:
  - TASK-015
references:
  - design_decisions/USB_PD_REV_C_tasarim_kararlari_handoff.md
ordinal: 124000
---

## Acceptance Criteria
<!-- AC:BEGIN -->
- [ ] #1 Tam dahili yükte V_PRE 5.02 V'ta regüle
- [ ] #2 Boost döngüsü kararlı
<!-- AC:END -->

## Definition of Done
<!-- DOD:BEGIN -->
- [ ] #1 Kanıt (ERC/netlist/ölçüm/commit) Implementation Notes'a yazıldı
- [ ] #2 Karar değiştiyse design_decisions/ ve CHANGES.TXT güncellendi
<!-- DOD:END -->
