gokcesena53/usb-pd-power-supply/backlog/tasks/task-018 - Pass-through-bolgesinde-TPS55340in-anahtarlamadigini-dogrula.md

---
id: TASK-018
title: Pass-through bölgesinde TPS55340'ın anahtarlamadığını doğrula
status: To Do
assignee: []
created_date: '2026-09-22 18:46'
updated_date: '2026-09-22 19:15'
labels:
  - bring-up
milestone: m-2
dependencies:
  - TASK-015
ordinal: 125000
---

## Acceptance Criteria
<!-- AC:BEGIN -->
- [ ] #1 5.5–28 V aralığında SW pininde anahtarlama yok
- [ ] #2 FB < 3 V (hesapta 28 V'ta ~2.43 V)
<!-- AC:END -->

## Definition of Done
<!-- DOD:BEGIN -->
- [ ] #1 Kanıt (ERC/netlist/ölçüm/commit) Implementation Notes'a yazıldı
- [ ] #2 Karar değiştiyse design_decisions/ ve CHANGES.TXT güncellendi
<!-- DOD:END -->
