gokcesena53/usb-pd-power-supply/backlog/tasks/task-021 - Cikis-anahtari-acilisinda-VBUS-tepe-gerilimini-olc.md

---
id: TASK-021
title: Çıkış anahtarı açılışında VBUS tepe gerilimini ölç
status: To Do
assignee: []
created_date: '2026-09-22 18:46'
updated_date: '2026-09-22 19:15'
labels:
  - bring-up
milestone: m-2
dependencies:
  - TASK-015
ordinal: 128000
---

## Acceptance Criteria
<!-- AC:BEGIN -->
- [ ] #1 28 V EPR, 3 A yükte USB_VBUS / PD_VOUT tepe < 34 V
<!-- AC:END -->

## Definition of Done
<!-- DOD:BEGIN -->
- [ ] #1 Kanıt (ERC/netlist/ölçüm/commit) Implementation Notes'a yazıldı
- [ ] #2 Karar değiştiyse design_decisions/ ve CHANGES.TXT güncellendi
<!-- DOD:END -->
