gokcesena53/usb-pd-power-supply/hardware/docs/reports/flow-space-plan-20260928/placement-plan.png

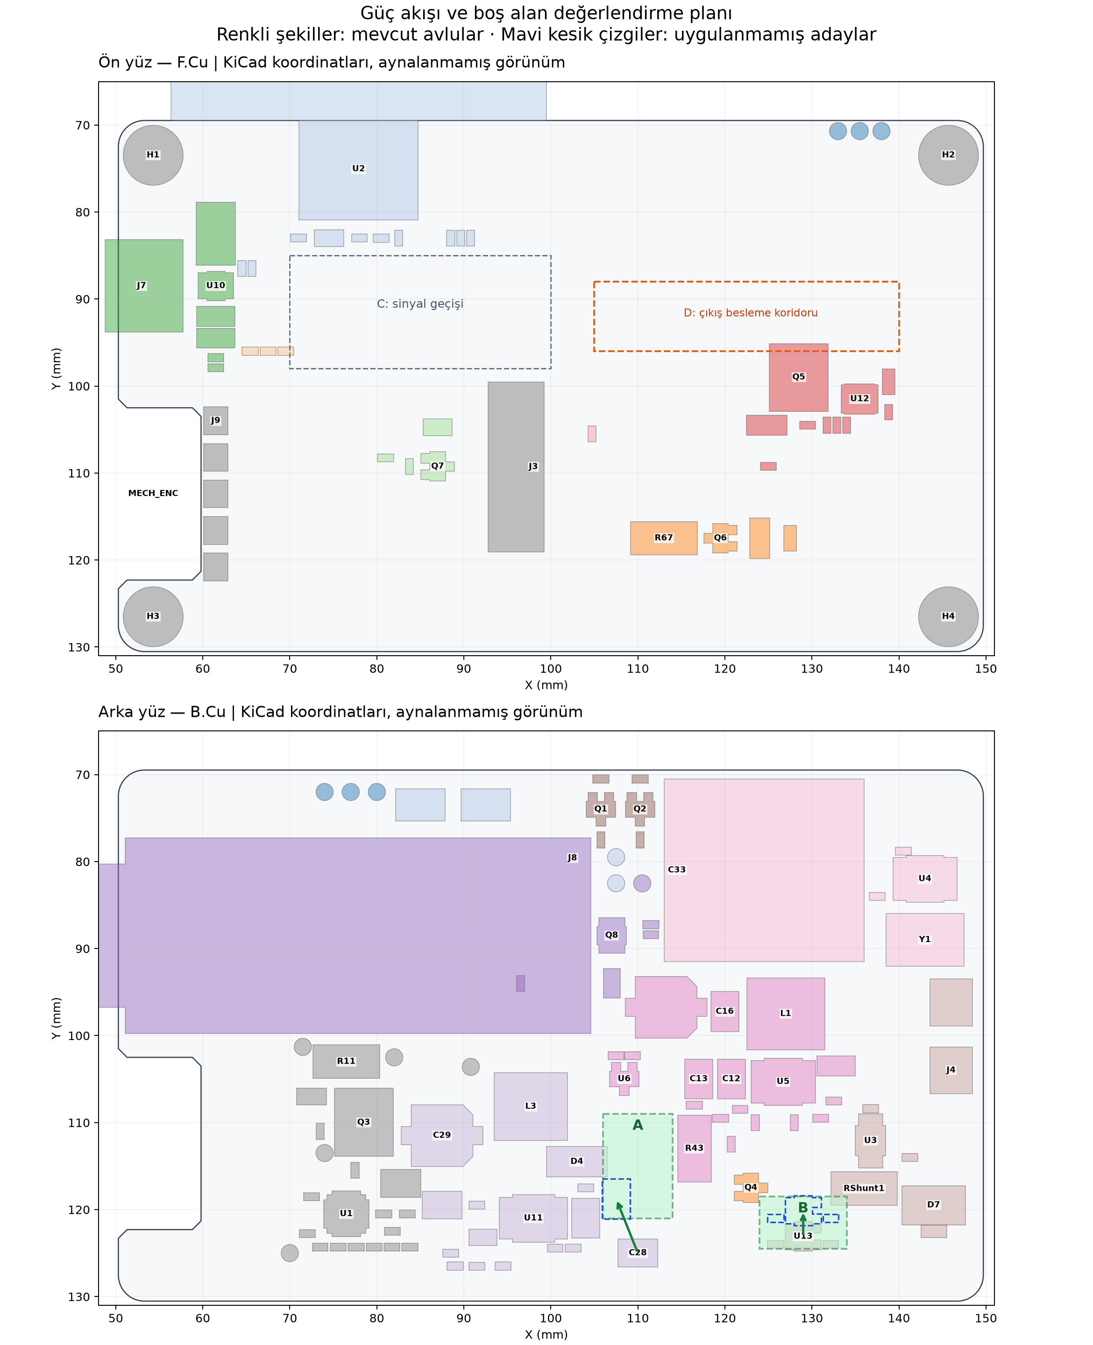
hardware/docs/reports/flow-space-plan-20260928/placement-plan.png
