gokcesena53/usb-pd-power-supply/hardware/docs/reports/flow-space-plan-20260928/top.png

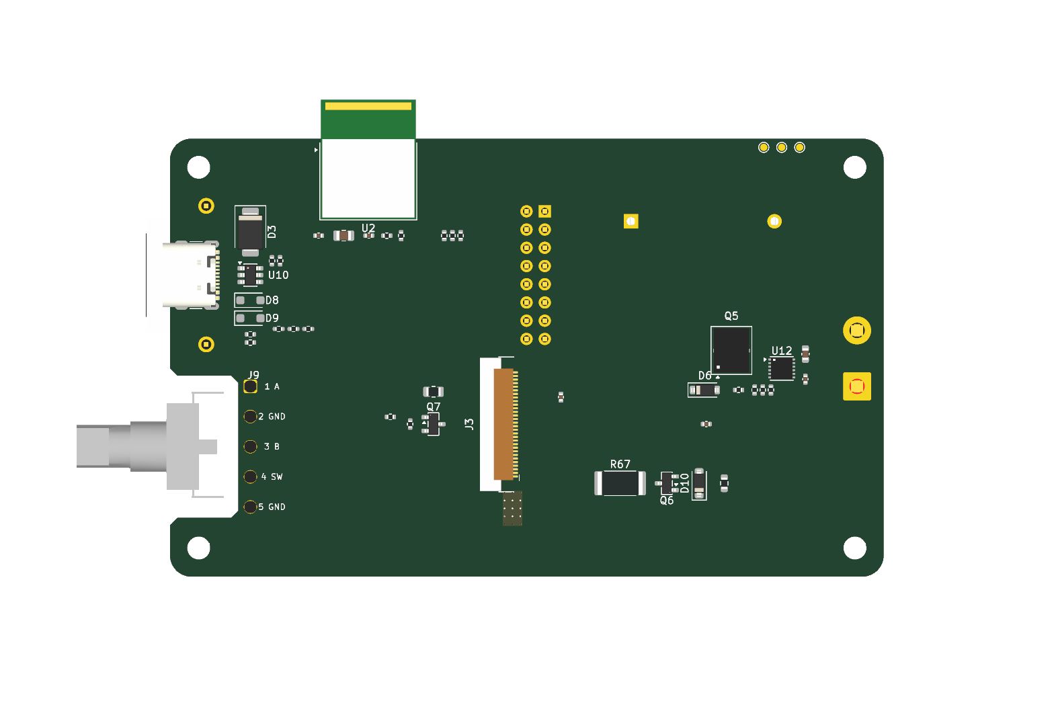
hardware/docs/reports/flow-space-plan-20260928/top.png
