gokcesena53/usb-pd-power-supply/hardware/docs/reports/freerouting-20260929/A_fpc-bot.png

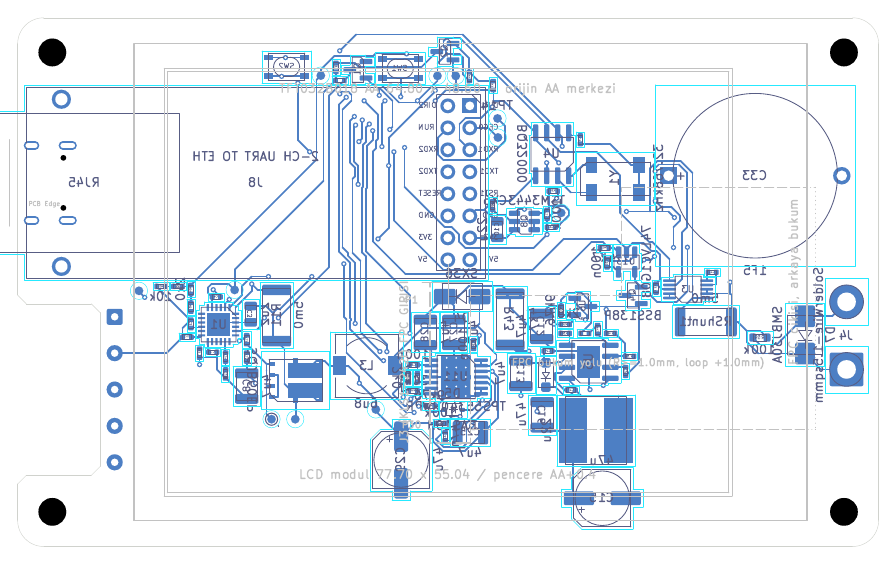
hardware/docs/reports/freerouting-20260929/A_fpc-bot.png
