gokcesena53/usb-pd-power-supply/hardware/docs/reports/freerouting-20260929/B_seed41-bot.png

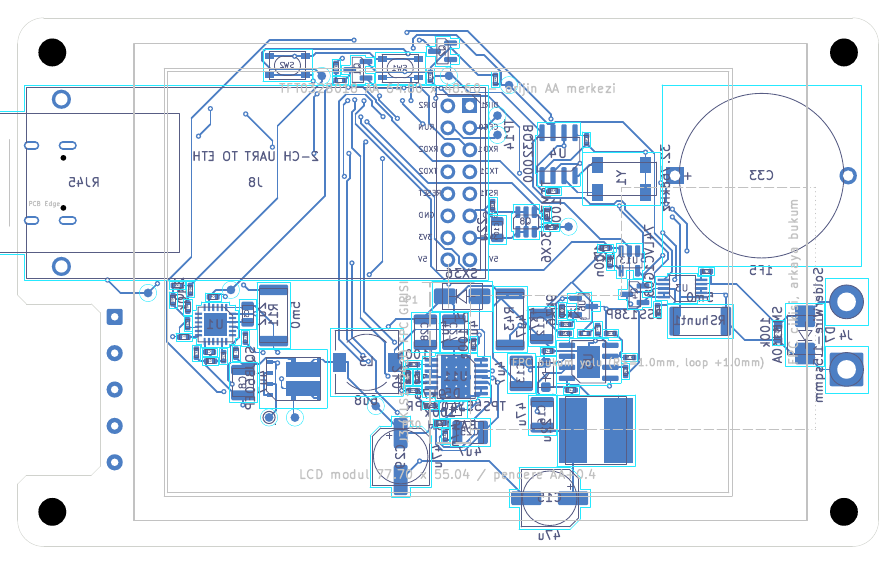
hardware/docs/reports/freerouting-20260929/B_seed41-bot.png
