gokcesena53/usb-pd-power-supply/hardware/docs/reports/freerouting-20260929/B_seed41-top.png

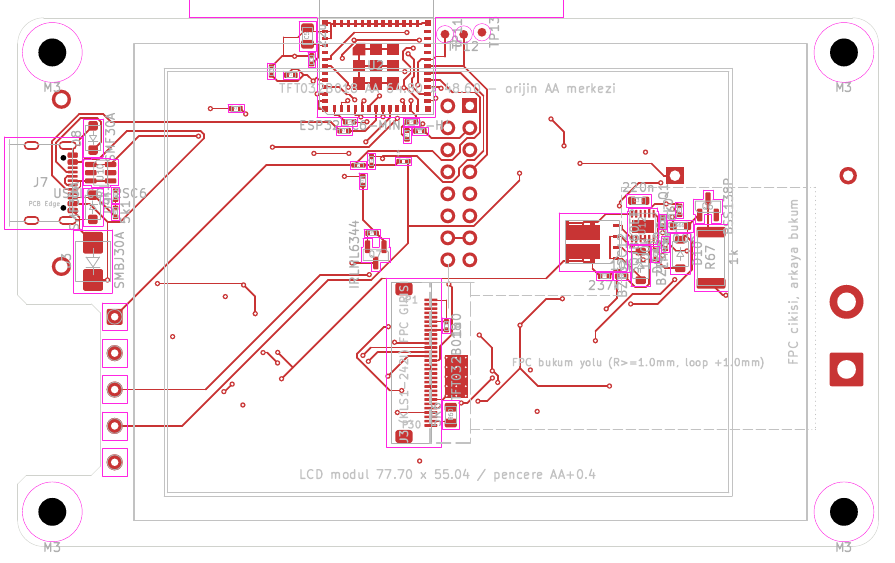
hardware/docs/reports/freerouting-20260929/B_seed41-top.png
