gokcesena53/usb-pd-power-supply/hardware/docs/reports/placement-lns-20260929/cand-bot.png

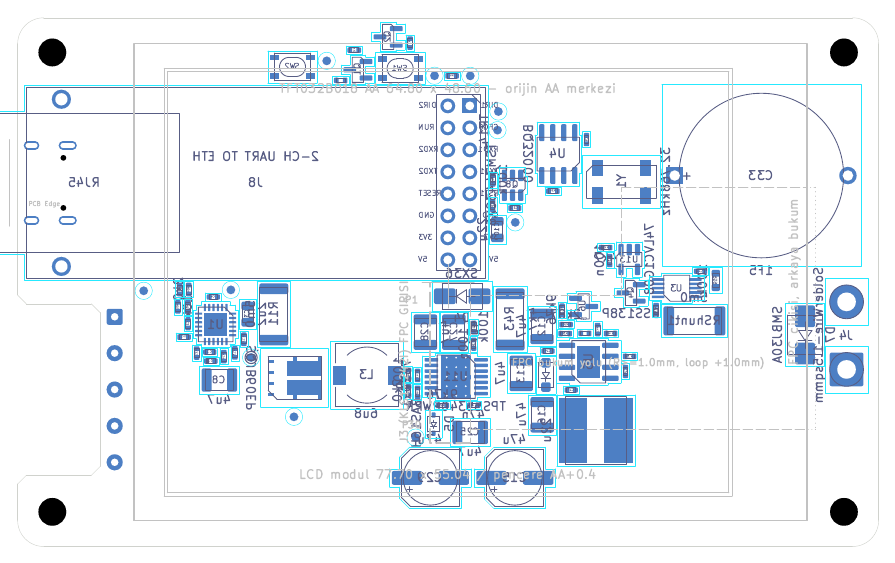
hardware/docs/reports/placement-lns-20260929/cand-bot.png
