gokcesena53/usb-pd-power-supply/hardware/docs/reports/placement-scratch-20260929/after-bottom.png

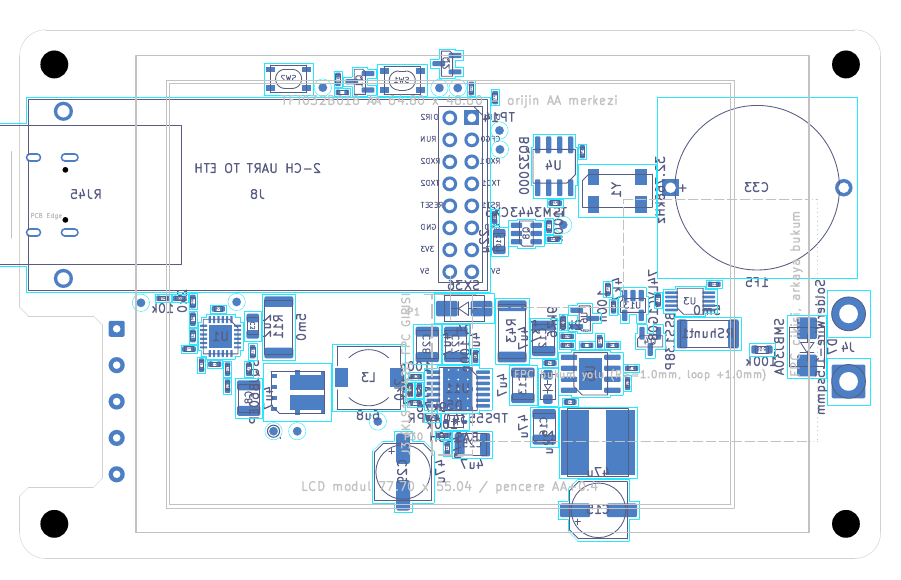
hardware/docs/reports/placement-scratch-20260929/after-bottom.png
