gokcesena53/usb-pd-power-supply/hardware/docs/reports/placement-scratch-20260929/before-bottom.png

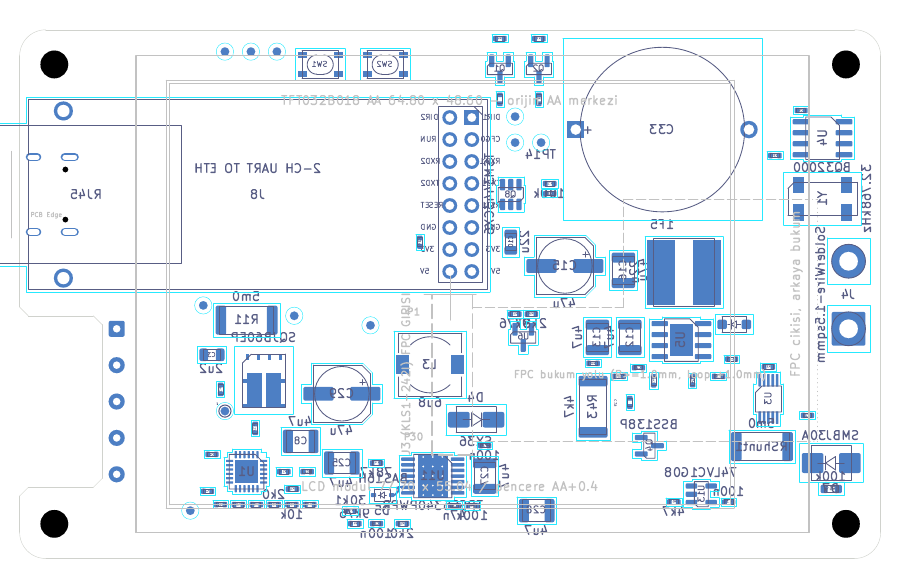
hardware/docs/reports/placement-scratch-20260929/before-bottom.png
