gokcesena53/usb-pd-power-supply/hardware/docs/reports/placement-scratch-20260929/before-top.png

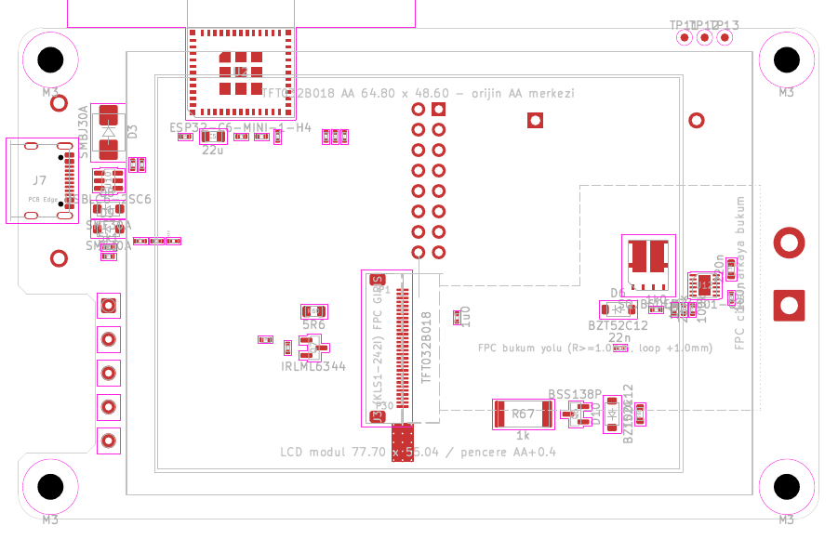
hardware/docs/reports/placement-scratch-20260929/before-top.png
