gokcesena53/usb-pd-power-supply/hardware/docs/reports/task-065-20260924/bottom-3d.png

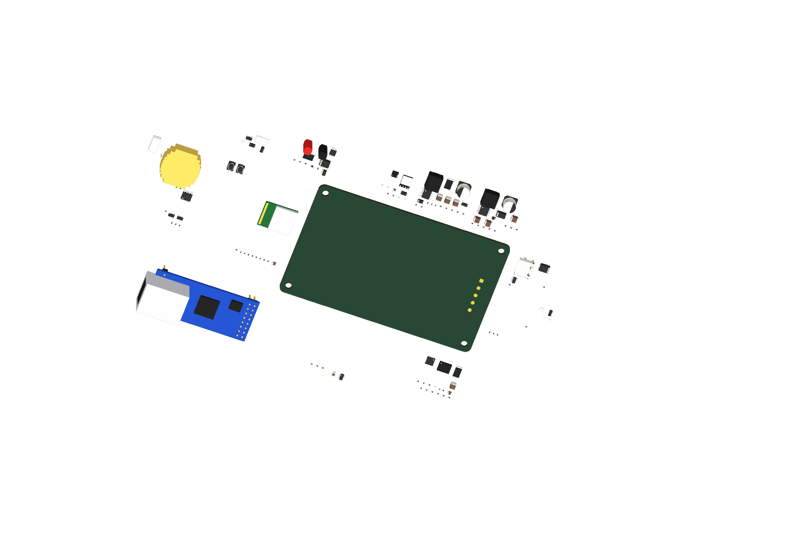
hardware/docs/reports/task-065-20260924/bottom-3d.png
