gokcesena53/usb-pd-power-supply/hardware/docs/reports/task-065-20260924/j3-datasheet.png

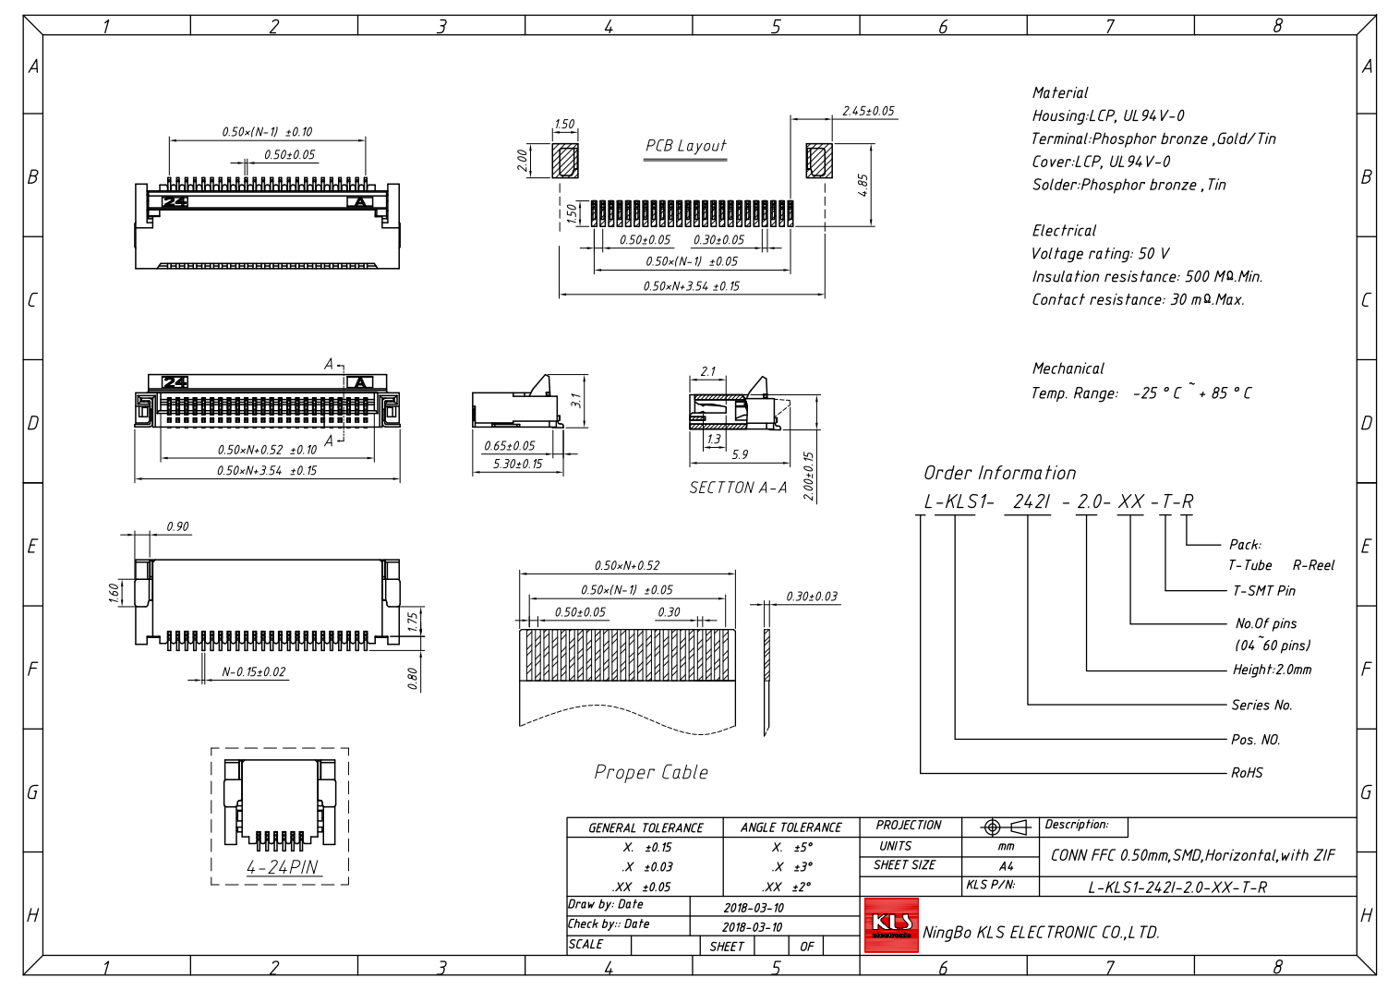
hardware/docs/reports/task-065-20260924/j3-datasheet.png
