gokcesena53/usb-pd-power-supply/hardware/docs/reports/task-066-20260924/schematic-encoder.png

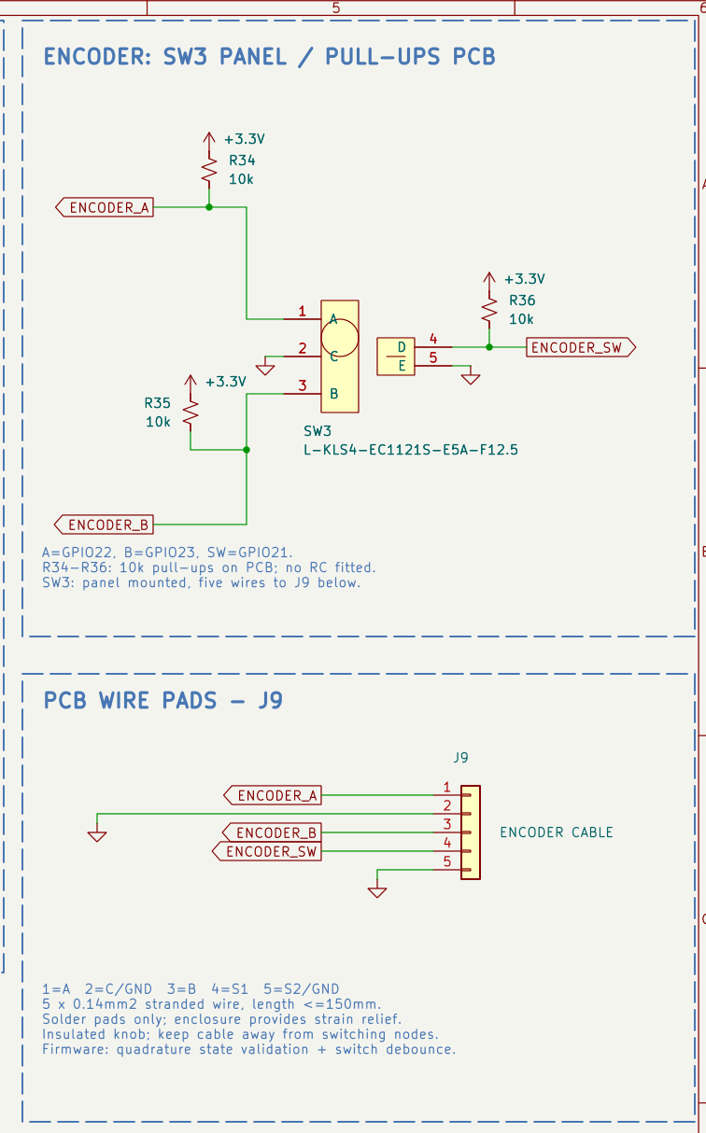
hardware/docs/reports/task-066-20260924/schematic-encoder.png
