gokcesena53/usb-pd-power-supply/hardware/docs/reports/task-094-20260925/datasheet-landscape.png

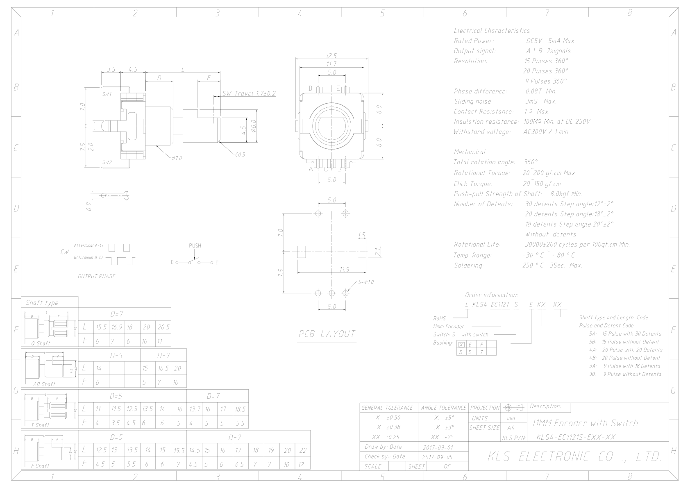
hardware/docs/reports/task-094-20260925/datasheet-landscape.png
