gokcesena53/usb-pd-power-supply/hardware/docs/reports/task-097-20260928/bottom_rc_audit.png

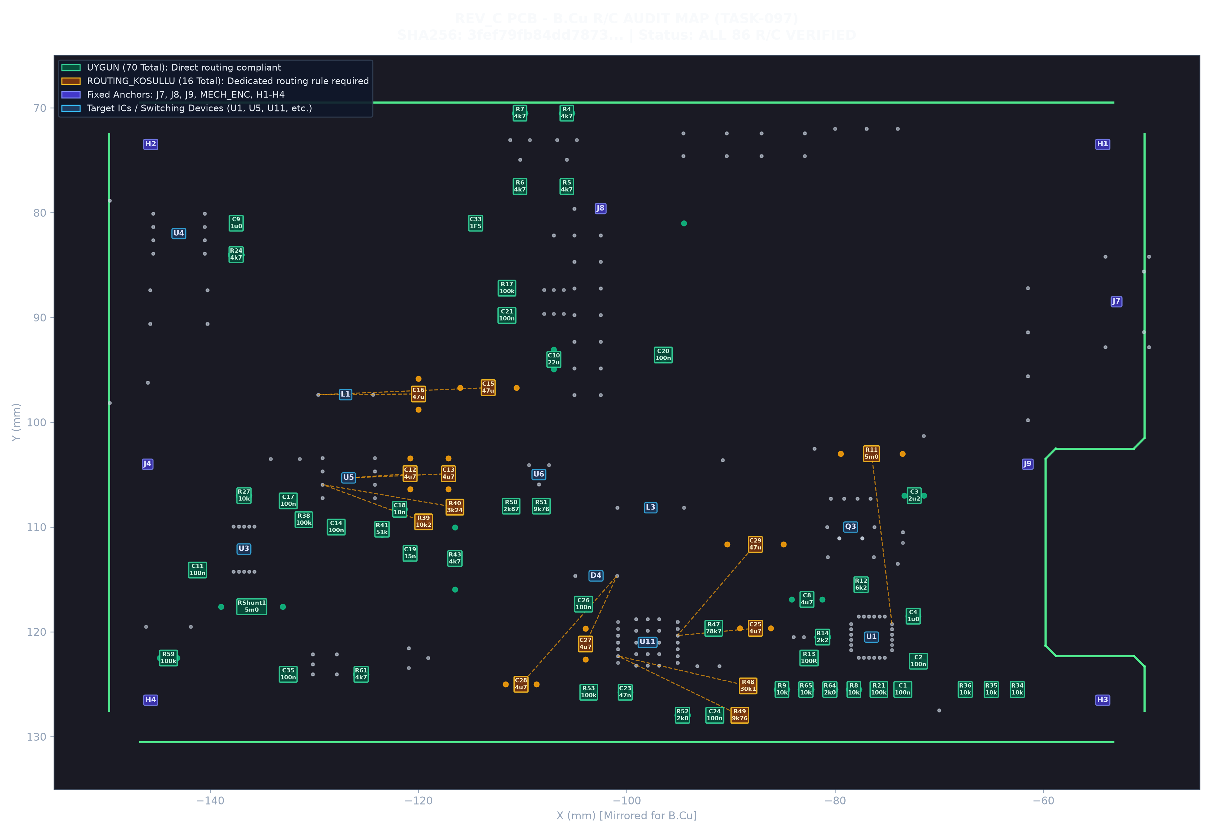
hardware/docs/reports/task-097-20260928/bottom_rc_audit.png
