gokcesena53/usb-pd-power-supply/hardware/images/reports/backlight-20260911/UI-final.png

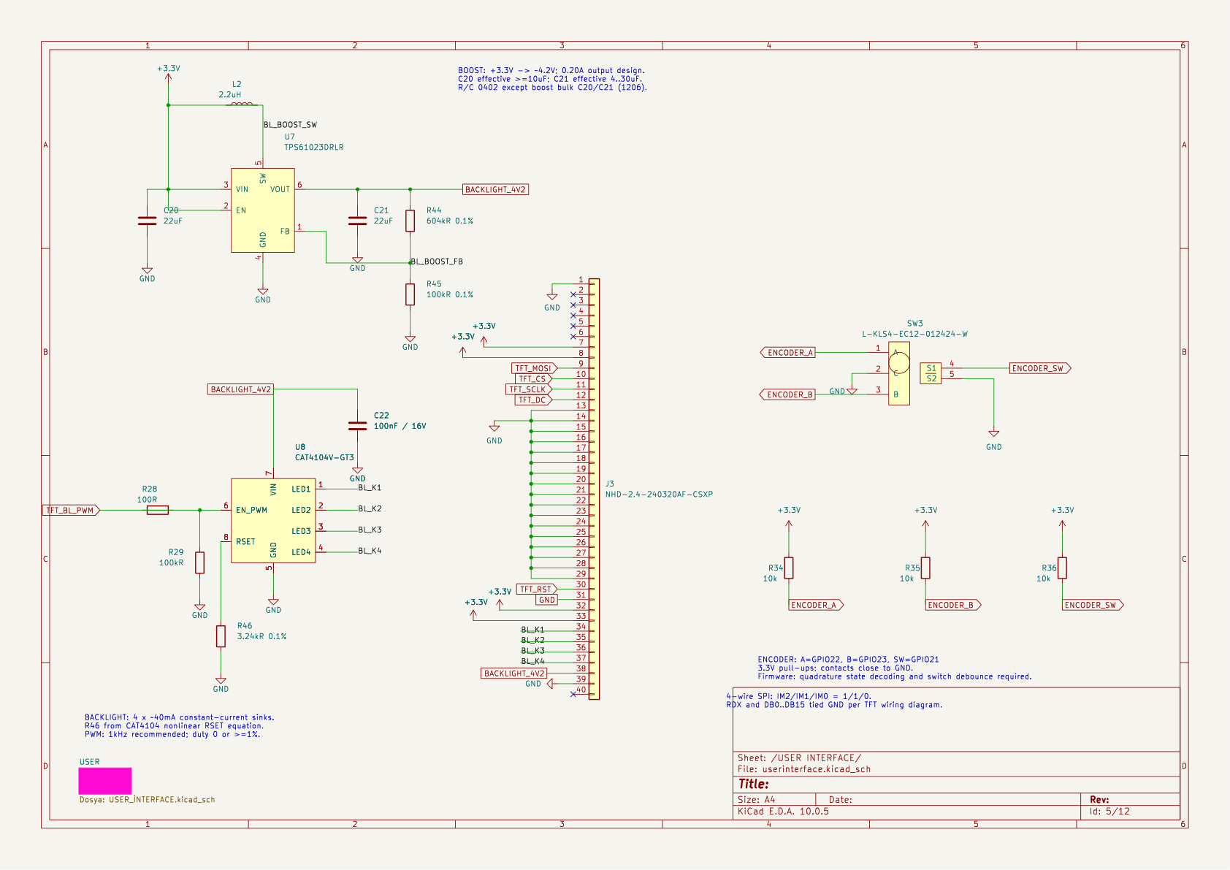
hardware/images/reports/backlight-20260911/UI-final.png
