gokcesena53/usb-pd-power-supply/hardware/images/reports/backlight-20260911/UI.png

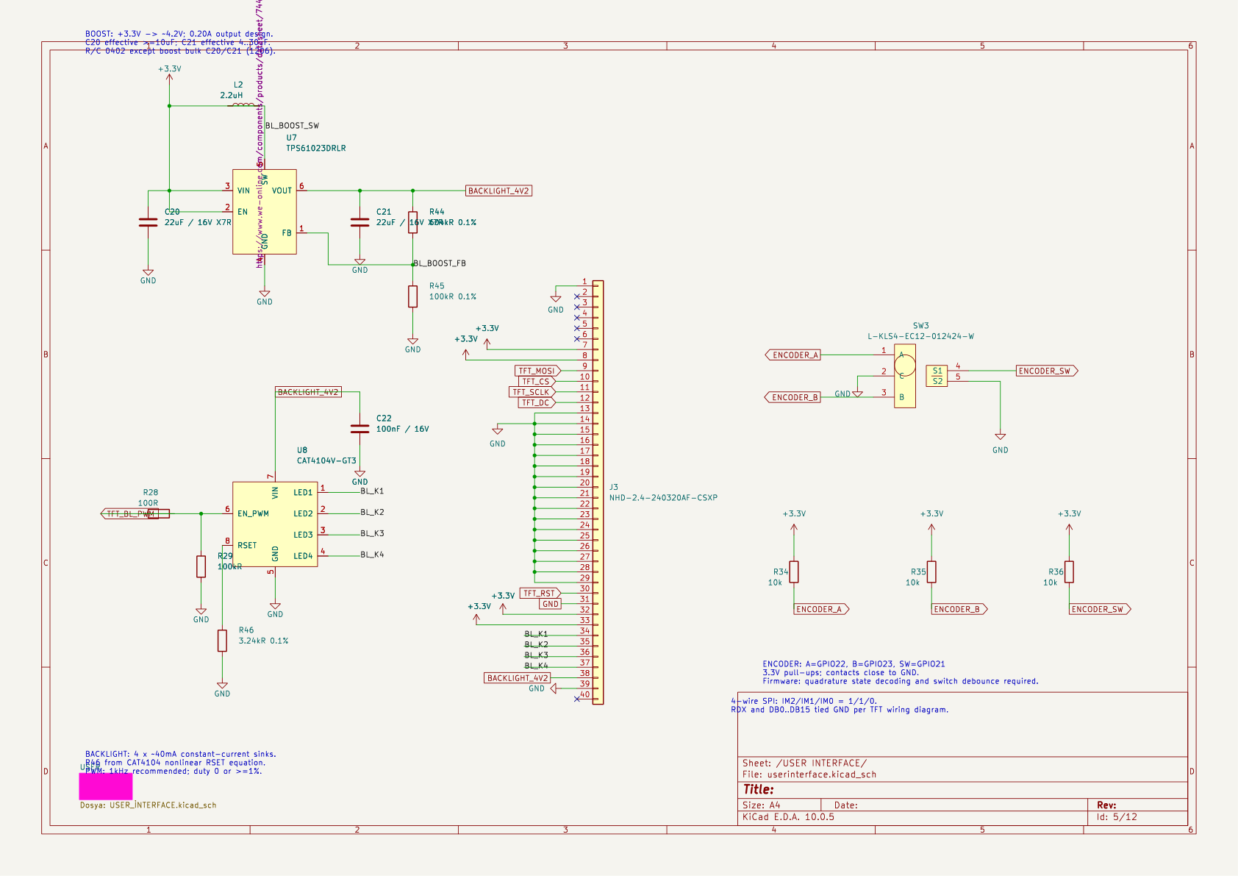
hardware/images/reports/backlight-20260911/UI.png
