gokcesena53/usb-pd-power-supply/hardware/images/reports/buck-20260910/page11.png

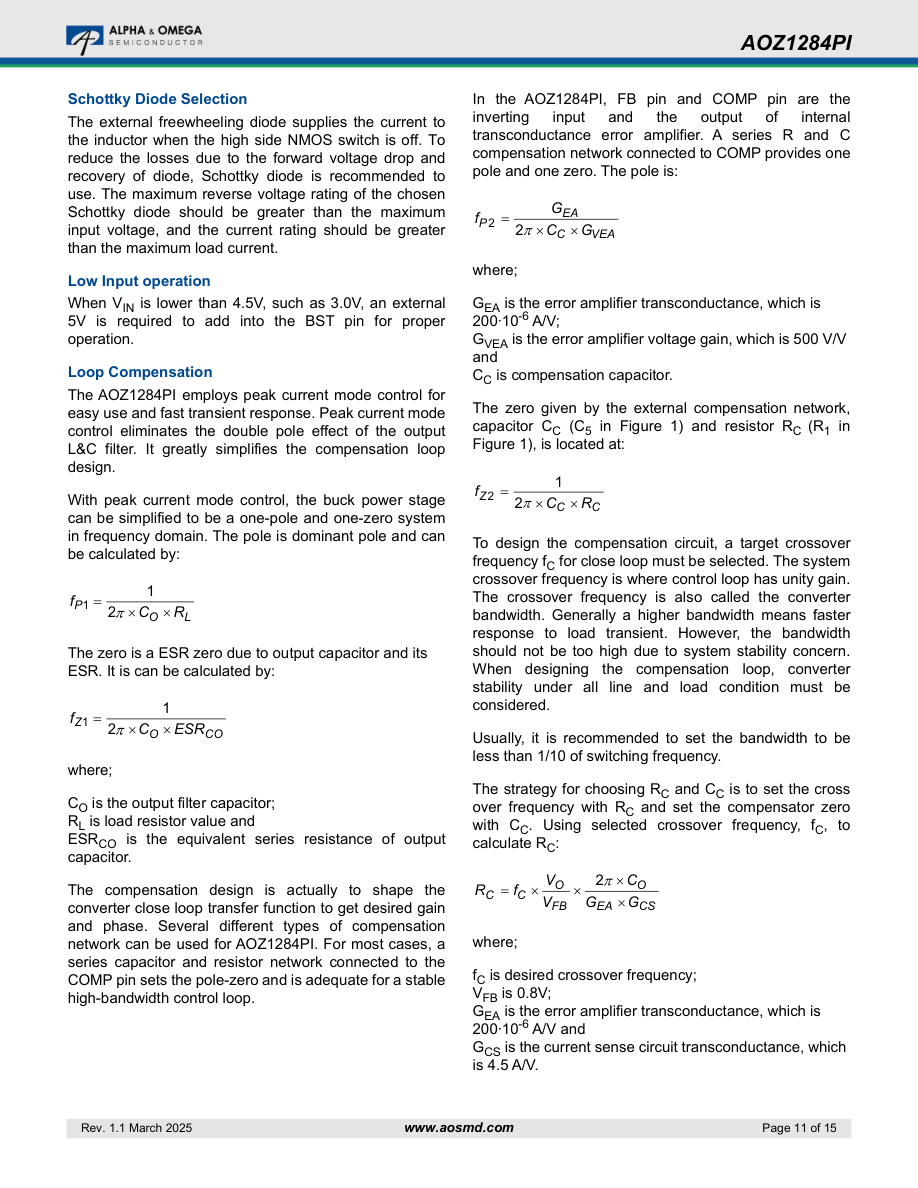
hardware/images/reports/buck-20260910/page11.png
