gokcesena53/usb-pd-power-supply/hardware/images/reports/buck-20260910/svg/powergeneration.png

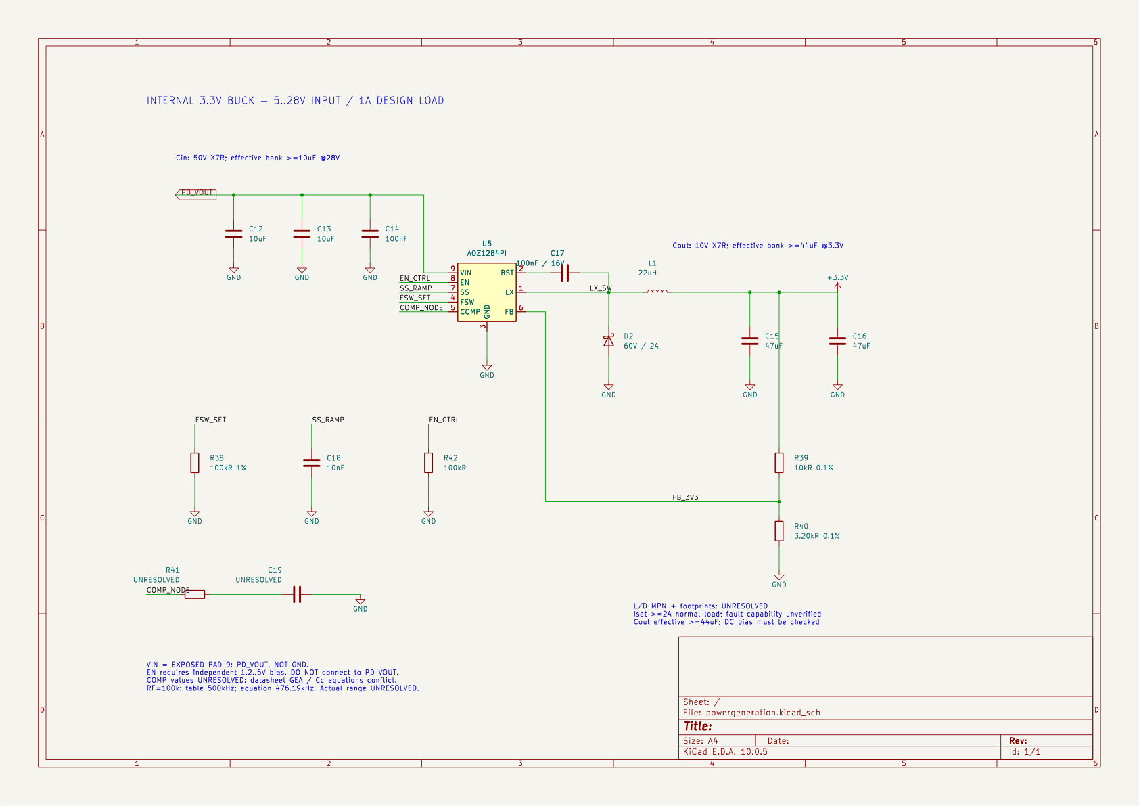
hardware/images/reports/buck-20260910/svg/powergeneration.png
