gokcesena53/usb-pd-power-supply/hardware/images/reports/final-prelayout-20260911/jae-render/page4.png

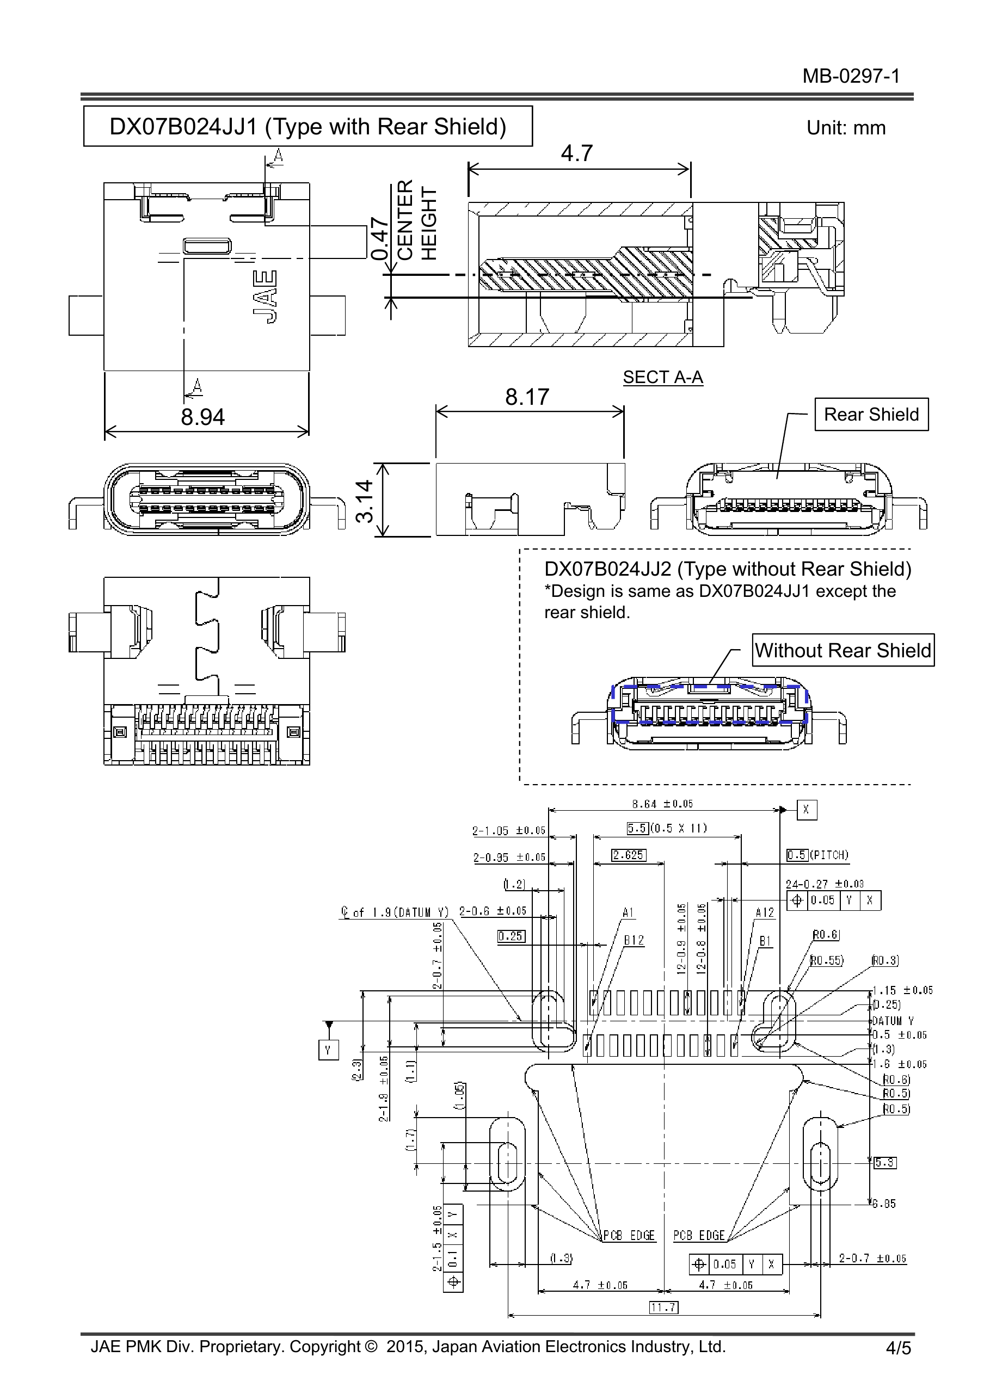
hardware/images/reports/final-prelayout-20260911/jae-render/page4.png
