gokcesena53/usb-pd-power-supply/hardware/images/reports/full-connectivity-20260911/report-render/page-4.png

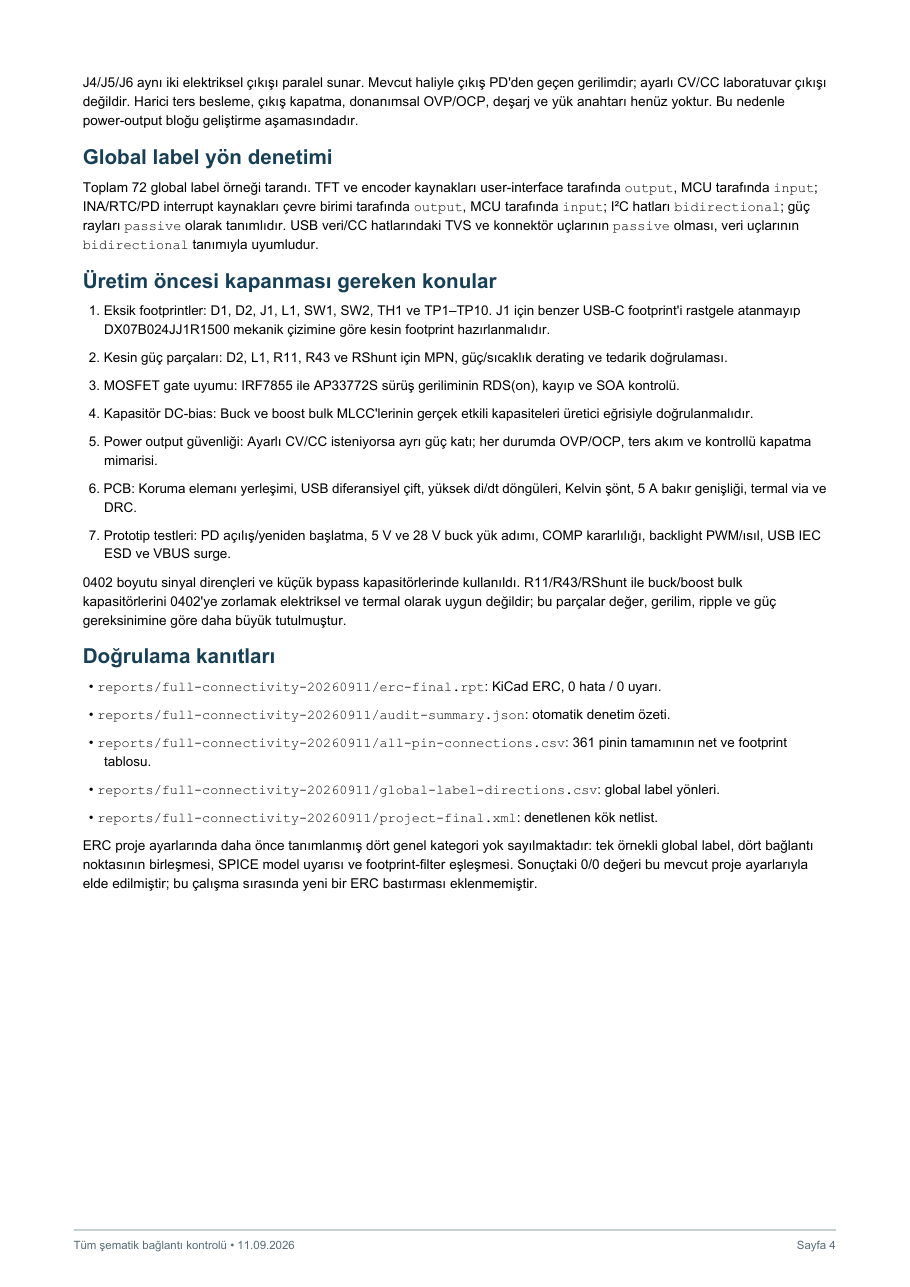
hardware/images/reports/full-connectivity-20260911/report-render/page-4.png
