gokcesena53/usb-pd-power-supply/hardware/images/reports/full-connectivity-20260911/ui-current.png

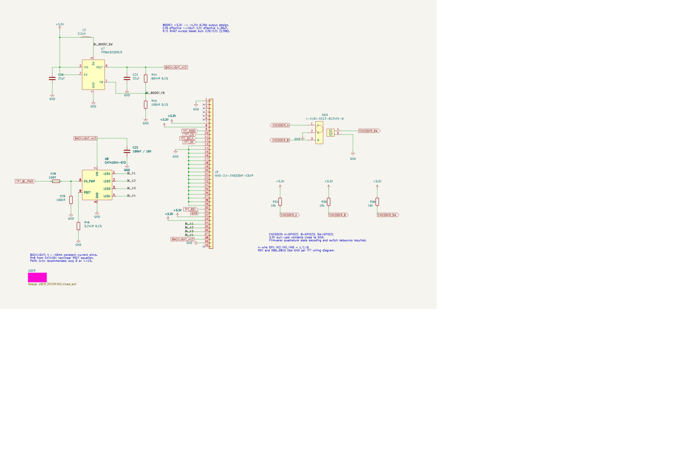
hardware/images/reports/full-connectivity-20260911/ui-current.png
