gokcesena53/usb-pd-power-supply/hardware/images/reports/layout-20260911/critical-routing-fcu.png

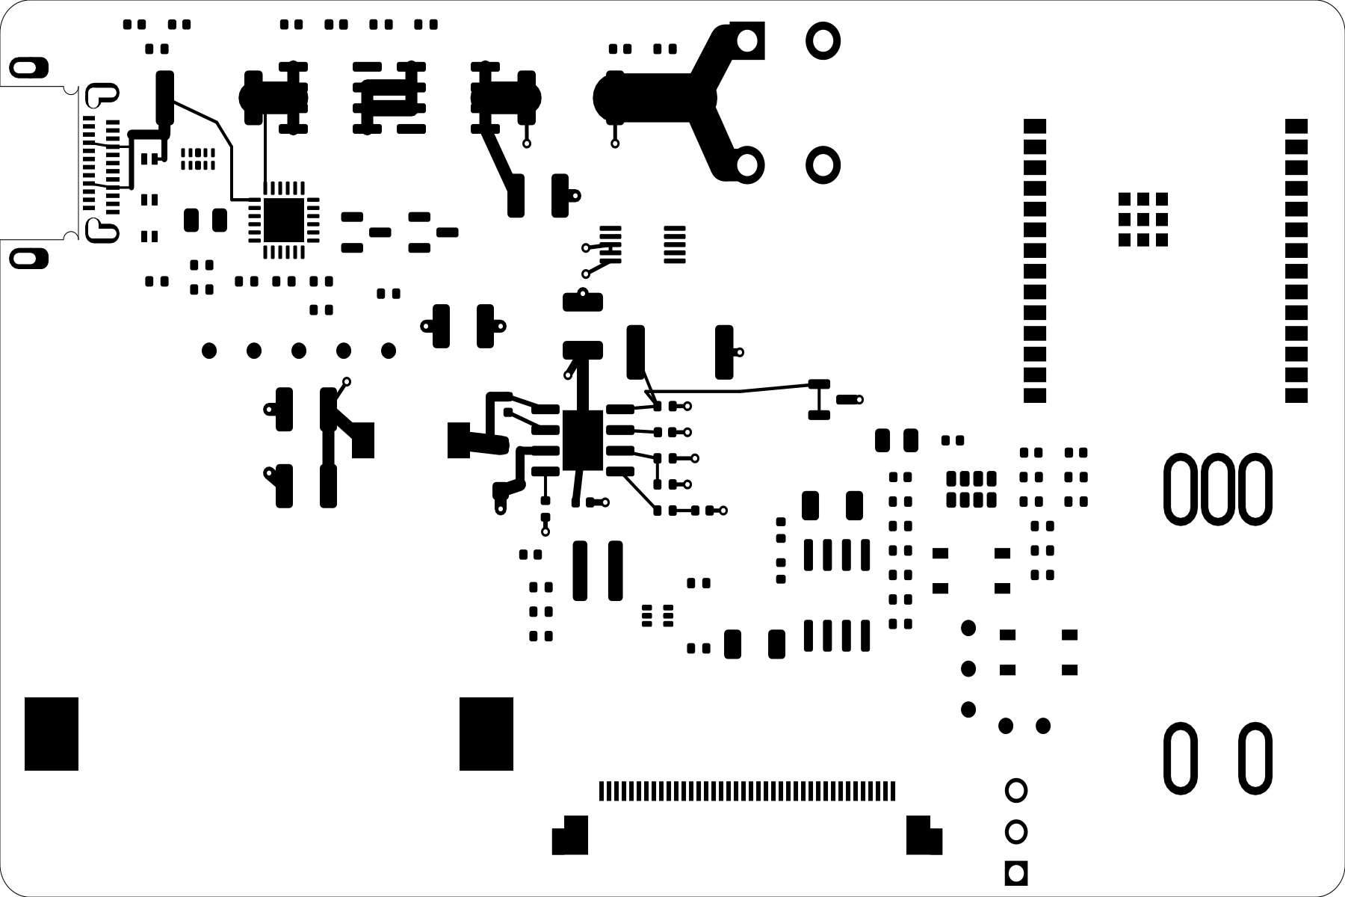
hardware/images/reports/layout-20260911/critical-routing-fcu.png
