gokcesena53/usb-pd-power-supply/hardware/images/reports/layout-20260911/critical-routing-inner-bottom.png

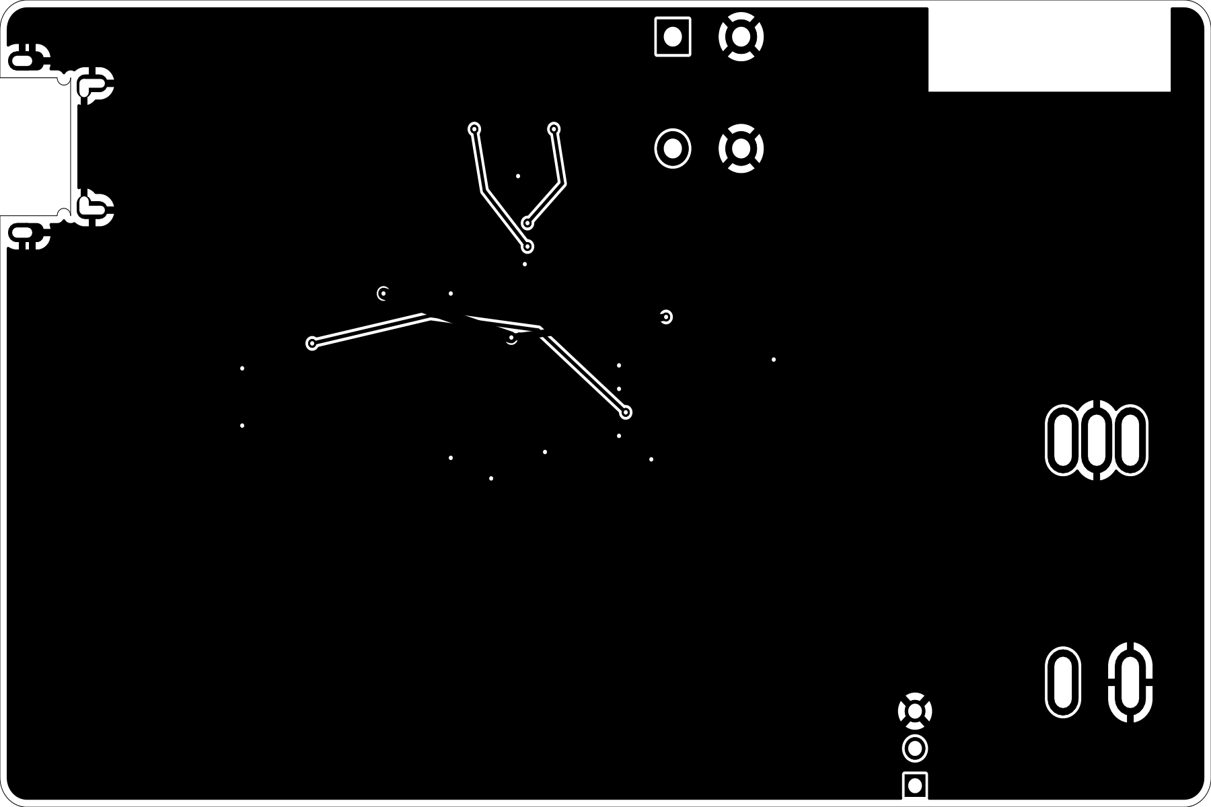
hardware/images/reports/layout-20260911/critical-routing-inner-bottom.png
