gokcesena53/usb-pd-power-supply/hardware/images/reports/layout-20260911/gnd-routing-corrected.png

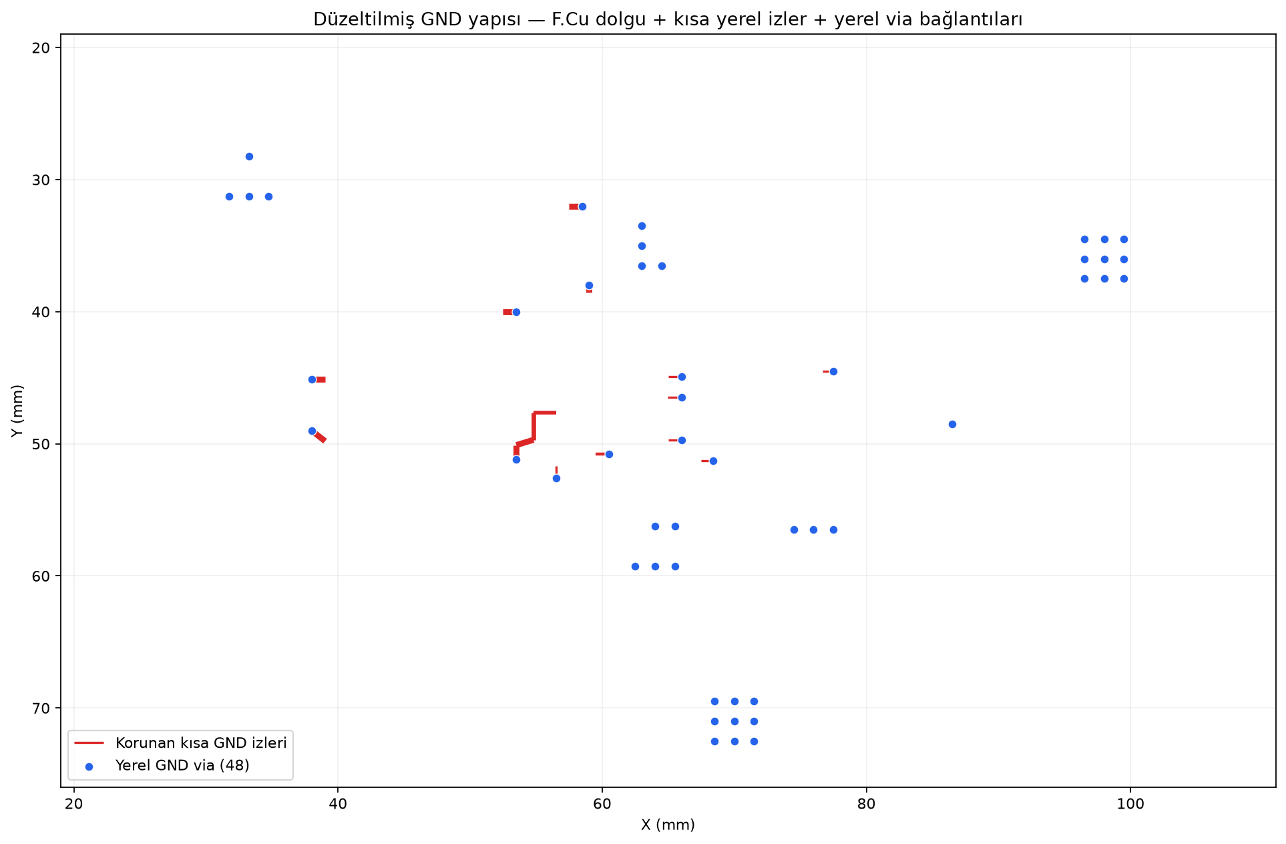
hardware/images/reports/layout-20260911/gnd-routing-corrected.png
