gokcesena53/usb-pd-power-supply/hardware/images/reports/layout-20260911/placement-top.png

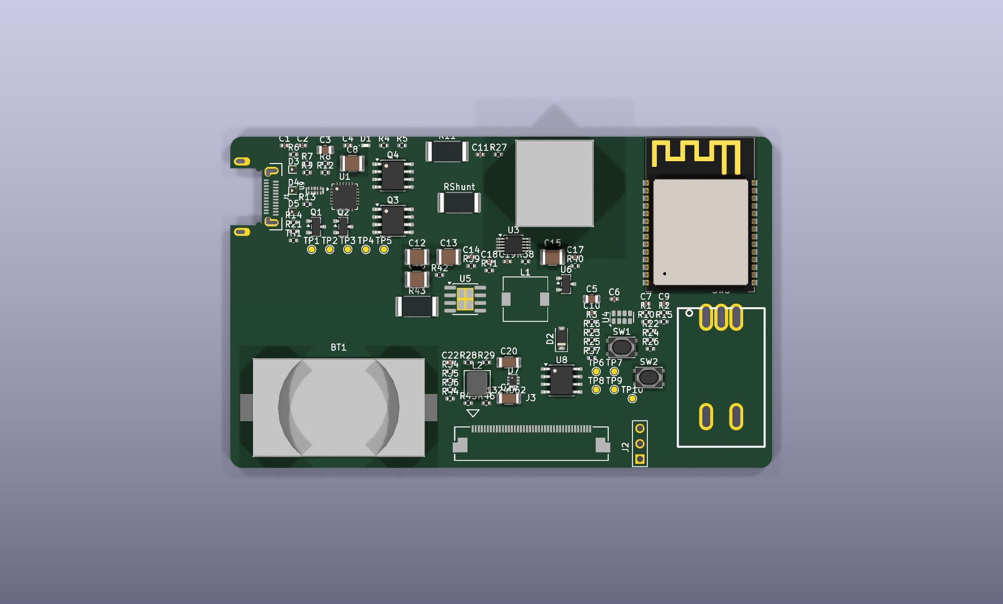
hardware/images/reports/layout-20260911/placement-top.png
