gokcesena53/usb-pd-power-supply/hardware/images/reports/layout-20260911/user-gnd-routing-top.png

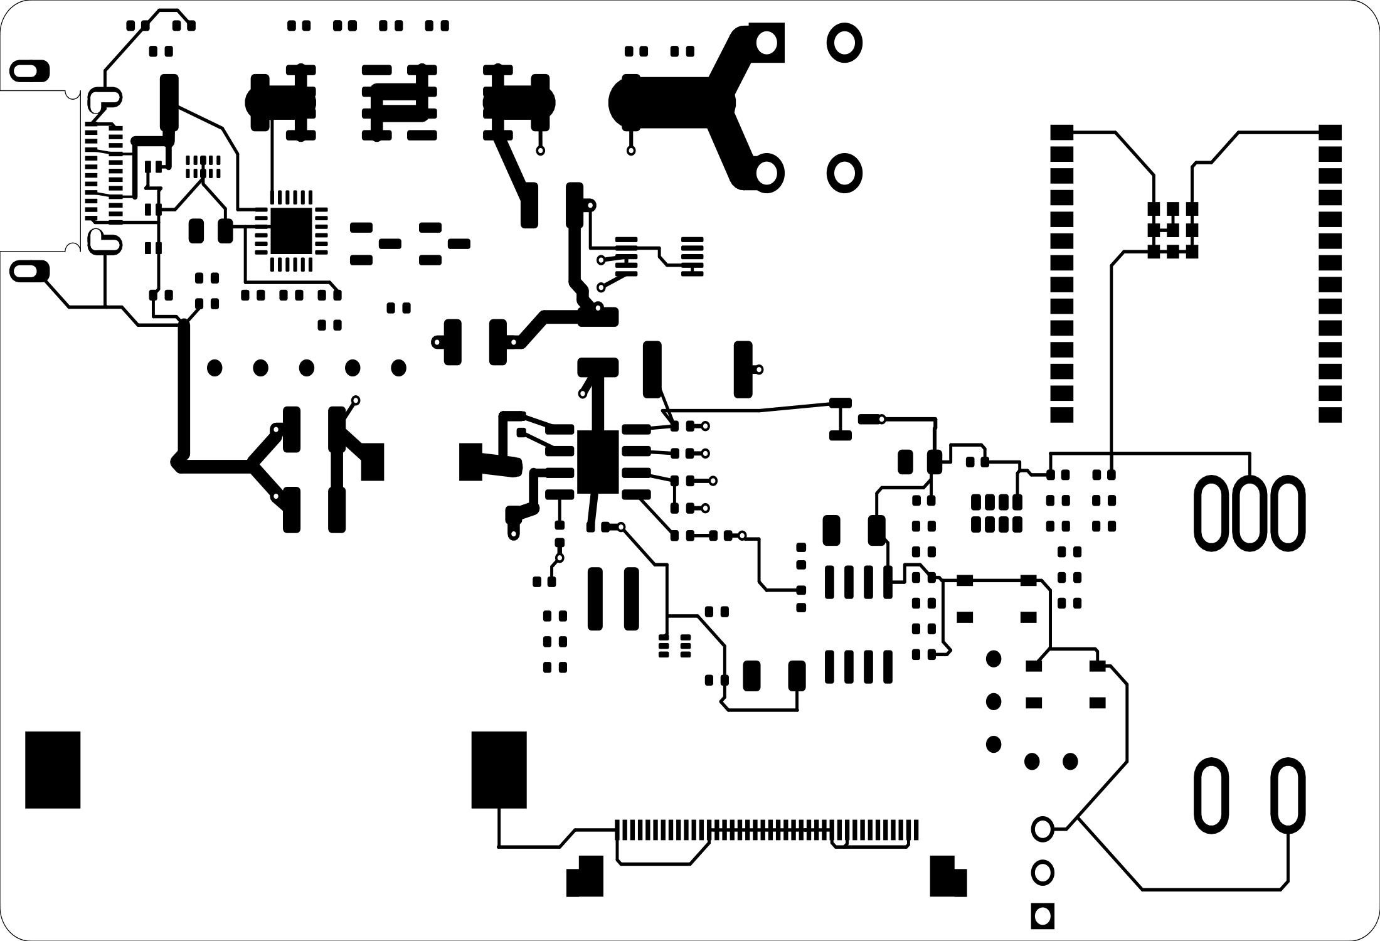
hardware/images/reports/layout-20260911/user-gnd-routing-top.png
