gokcesena53/usb-pd-power-supply/hardware/images/reports/output-update/battery.png

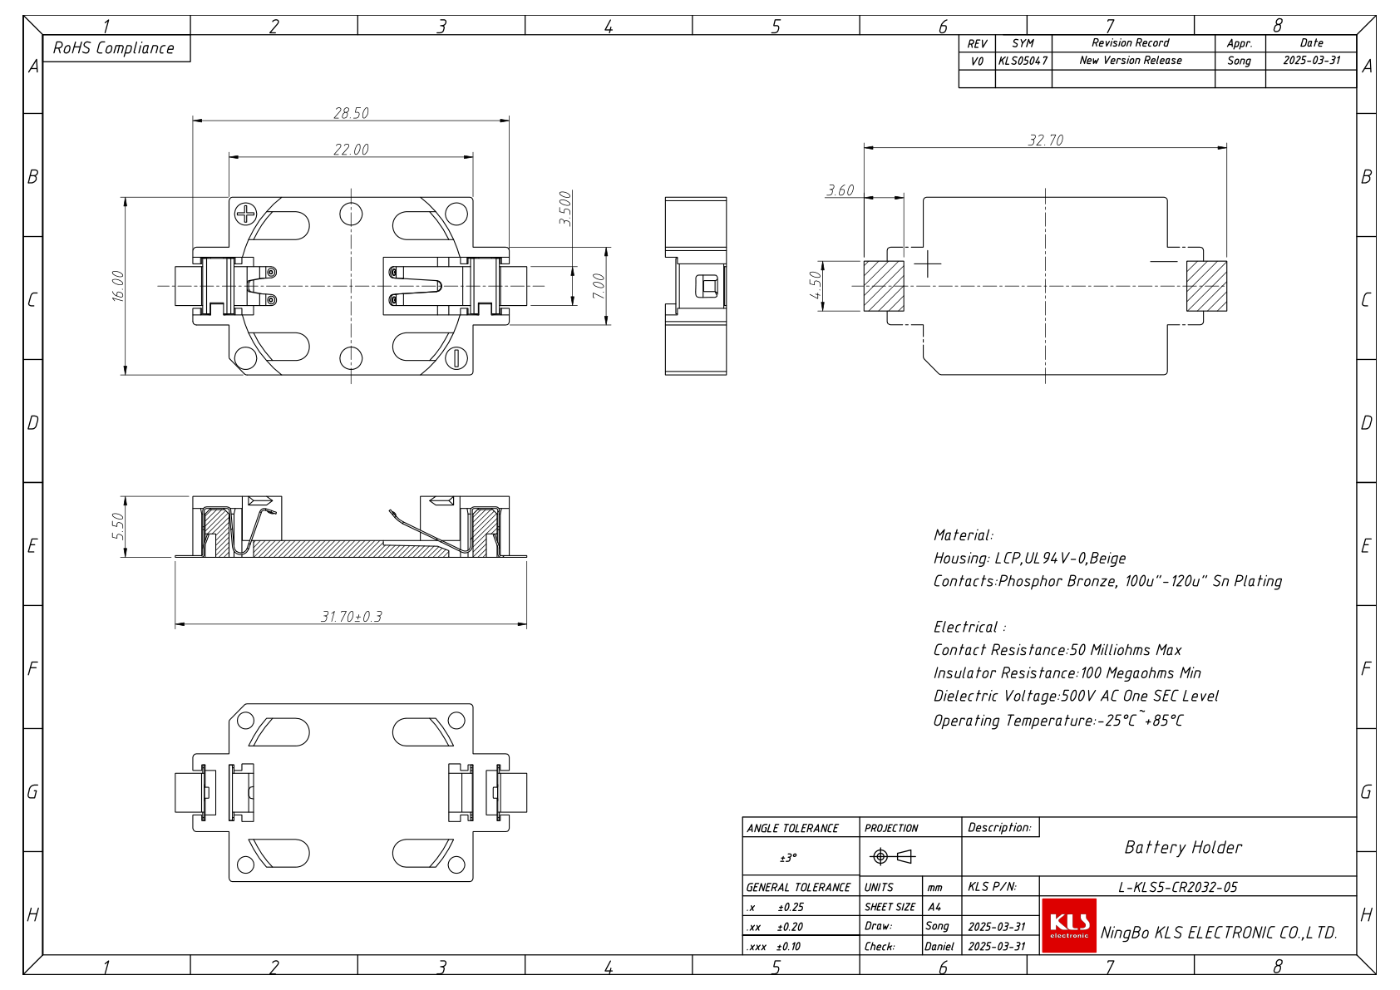
hardware/images/reports/output-update/battery.png
