gokcesena53/usb-pd-power-supply/hardware/images/reports/output-update/DG142R-5.08-XXP-1Y-00A(H)T0-l.pdf.png

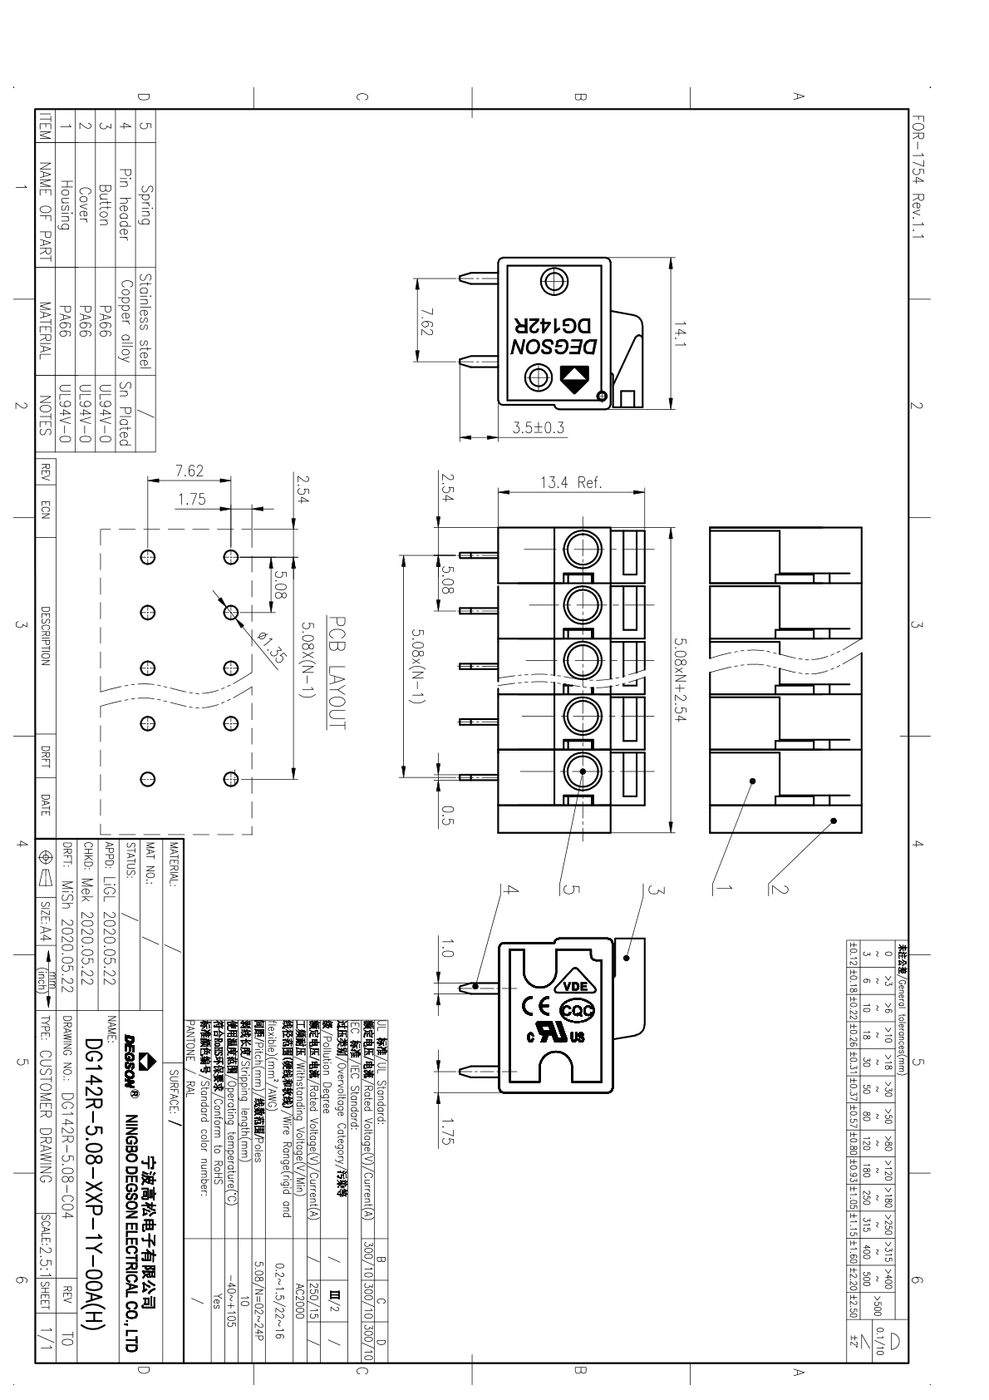
hardware/images/reports/output-update/DG142R-5.08-XXP-1Y-00A(H)T0-l.pdf.png
