gokcesena53/usb-pd-power-supply/hardware/images/reports/output-update/models.png

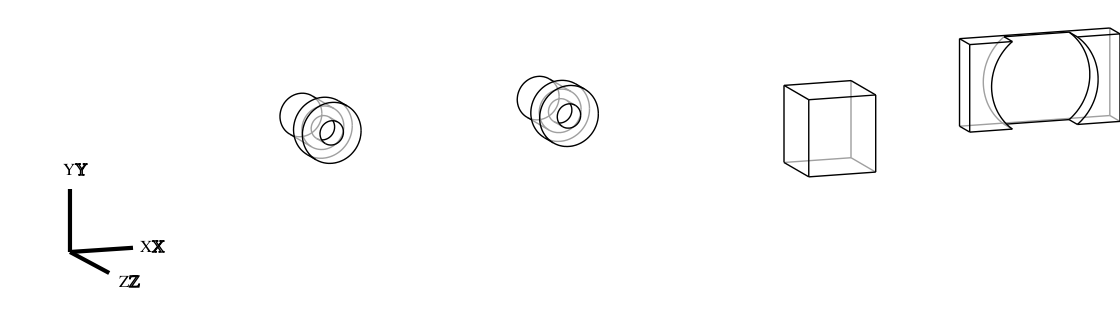
hardware/images/reports/output-update/models.png
