gokcesena53/usb-pd-power-supply/hardware/images/reports/output-update/NHD-2.4-240320AF-CSXP.pdf.png

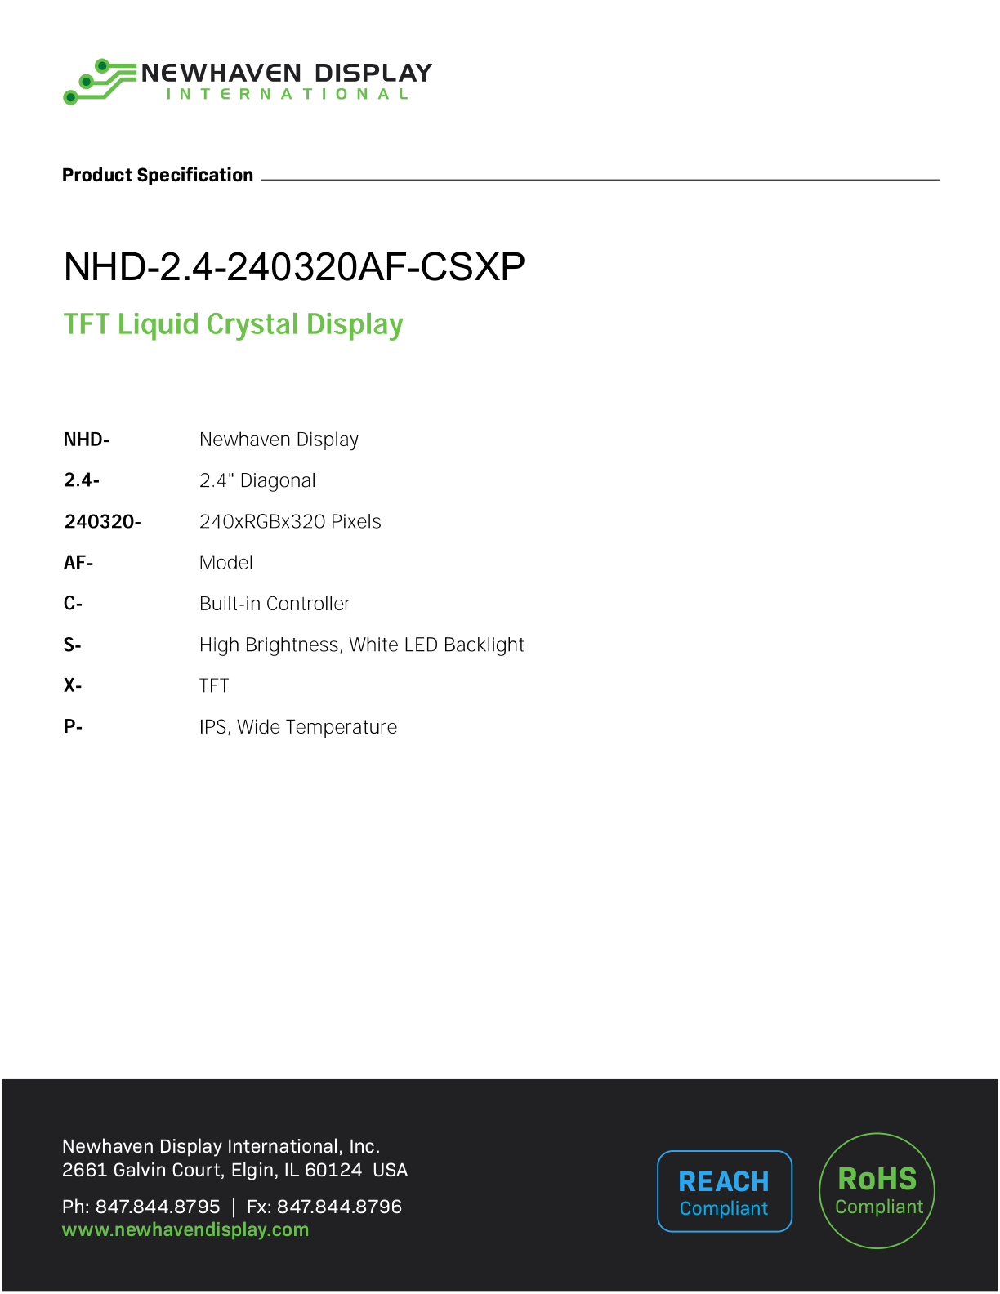
hardware/images/reports/output-update/NHD-2.4-240320AF-CSXP.pdf.png
