gokcesena53/usb-pd-power-supply/hardware/images/reports/output-update/pdf-review/00_DEGISIKLIK_RAPORU-1.png

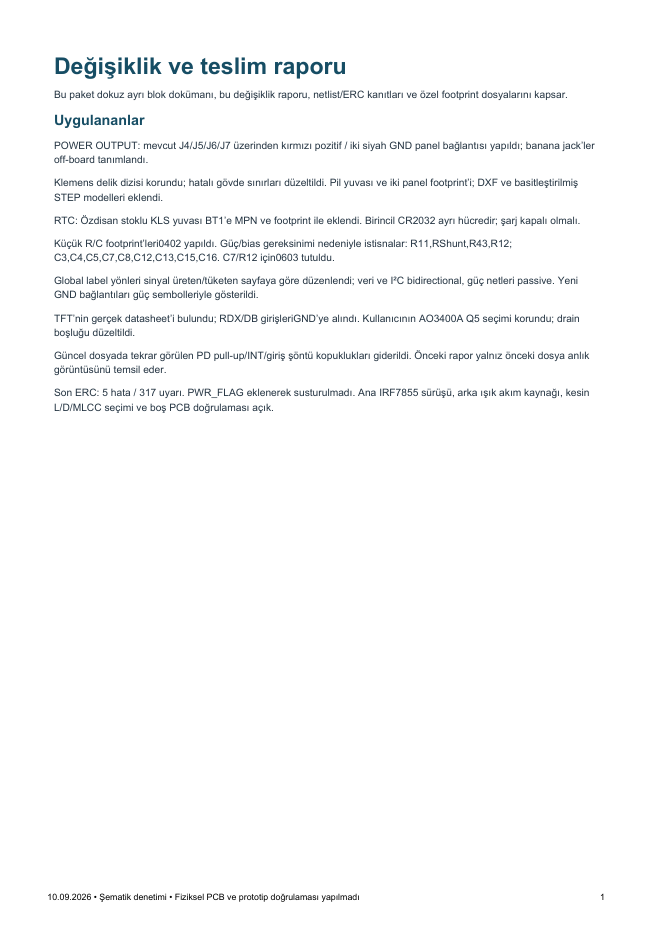
hardware/images/reports/output-update/pdf-review/00_DEGISIKLIK_RAPORU-1.png
