gokcesena53/usb-pd-power-supply/hardware/images/reports/output-update/pdf-review/01_USB_C_INPUT-1.png

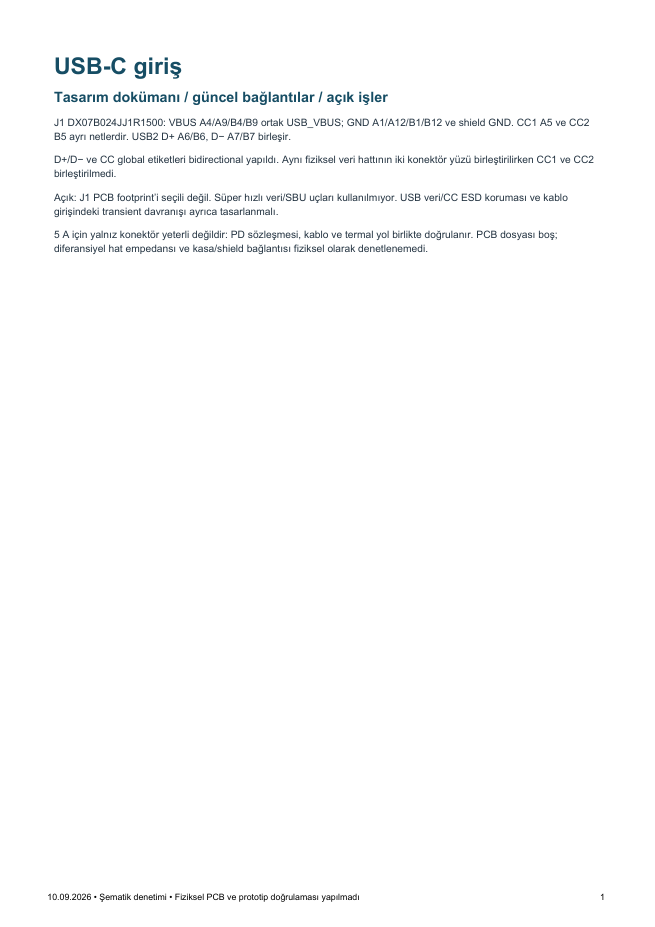
hardware/images/reports/output-update/pdf-review/01_USB_C_INPUT-1.png
