gokcesena53/usb-pd-power-supply/hardware/images/reports/output-update/pdf-review/02_USB_PD_CONTROLLER-1.png

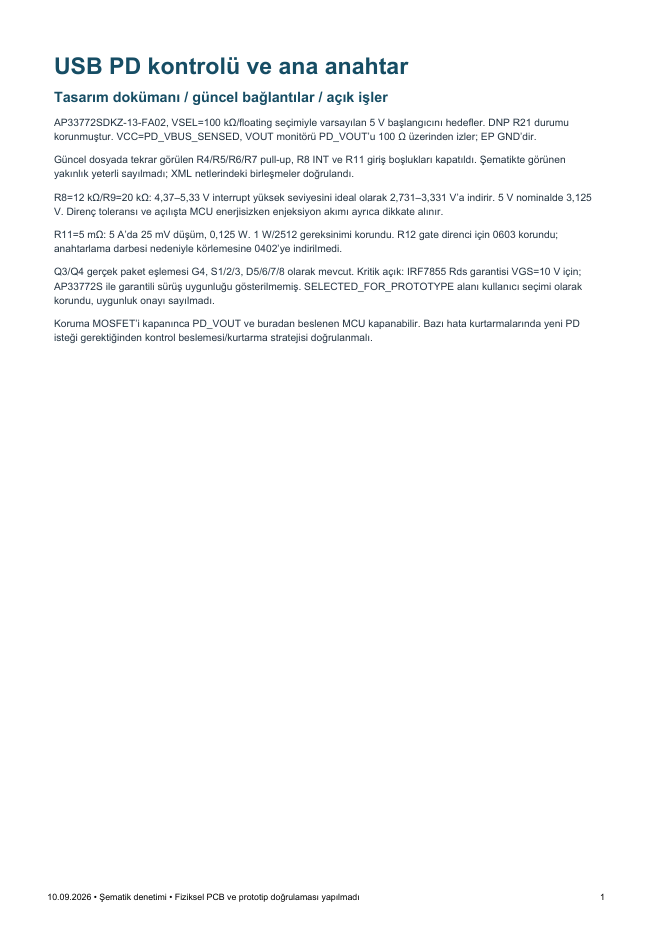
hardware/images/reports/output-update/pdf-review/02_USB_PD_CONTROLLER-1.png
