gokcesena53/usb-pd-power-supply/hardware/images/reports/output-update/pdf-review/03_MCU-4.png

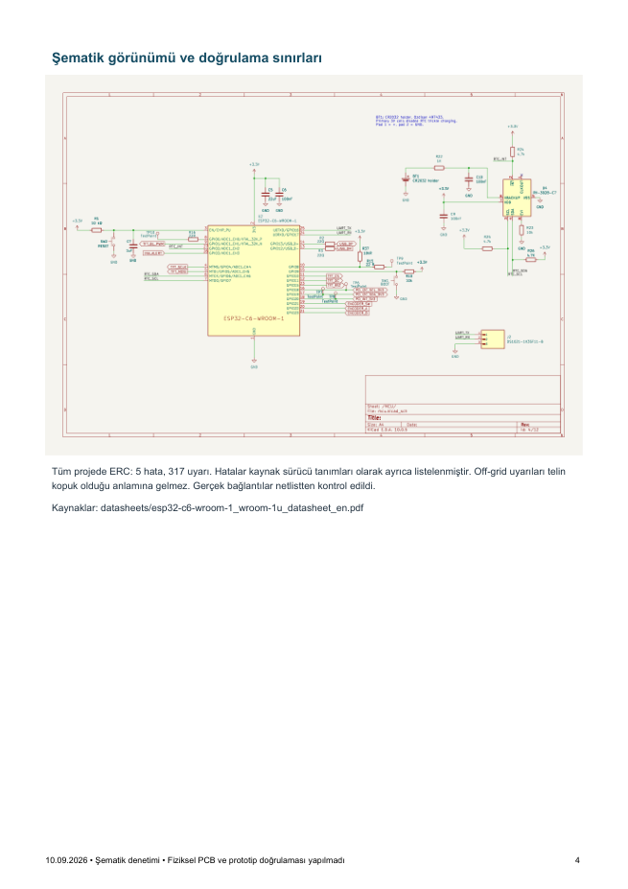
hardware/images/reports/output-update/pdf-review/03_MCU-4.png
