gokcesena53/usb-pd-power-supply/hardware/images/reports/output-update/pdf-review/04_RTC_BATTERY-2.png

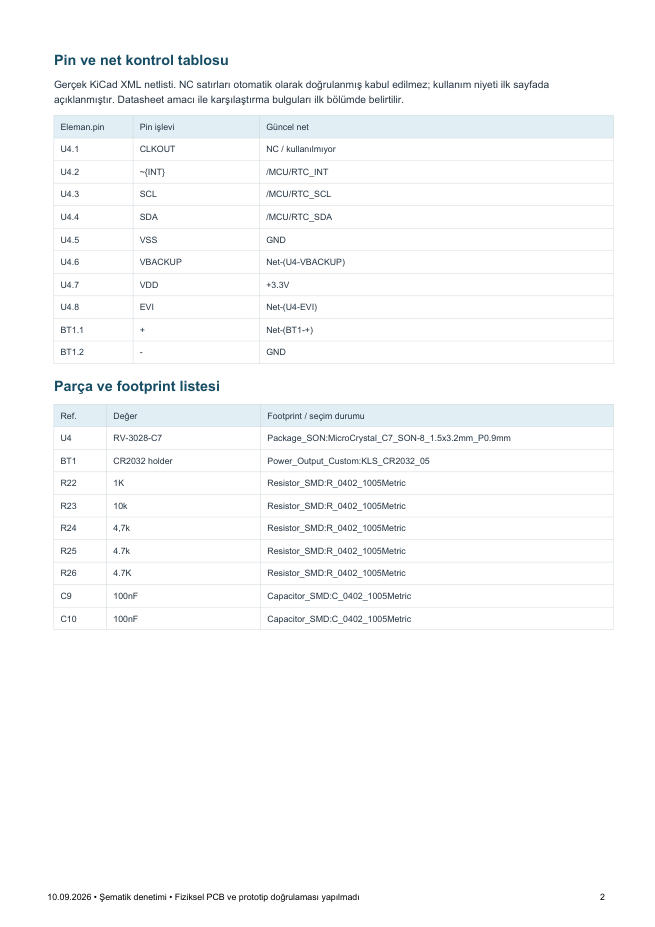
hardware/images/reports/output-update/pdf-review/04_RTC_BATTERY-2.png
