gokcesena53/usb-pd-power-supply/hardware/images/reports/output-update/pdf-review/05_TFT-2.png

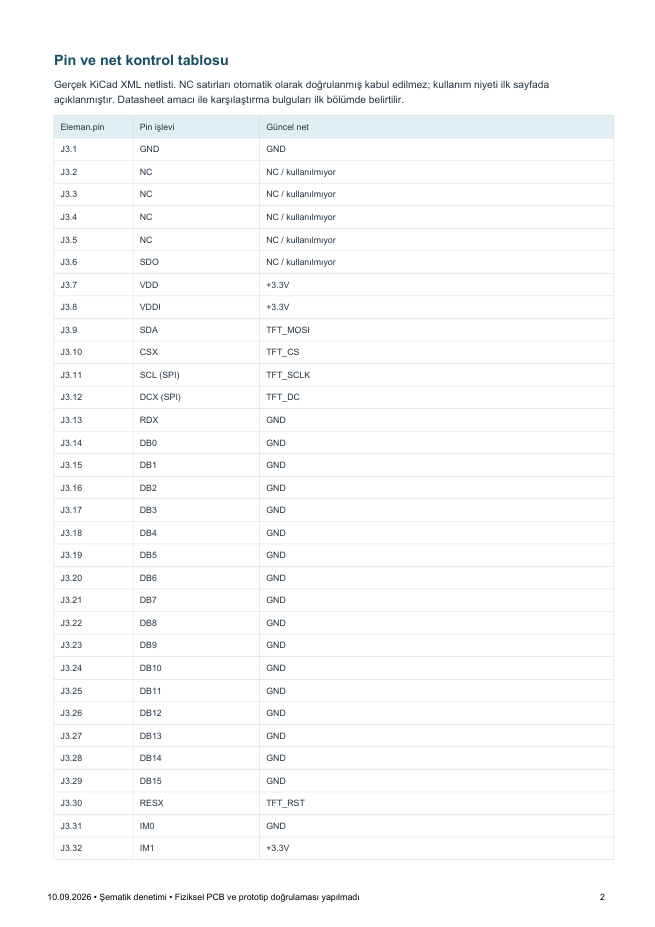
hardware/images/reports/output-update/pdf-review/05_TFT-2.png
