gokcesena53/usb-pd-power-supply/hardware/images/reports/output-update/pdf-review/06_ENCODER-1.png

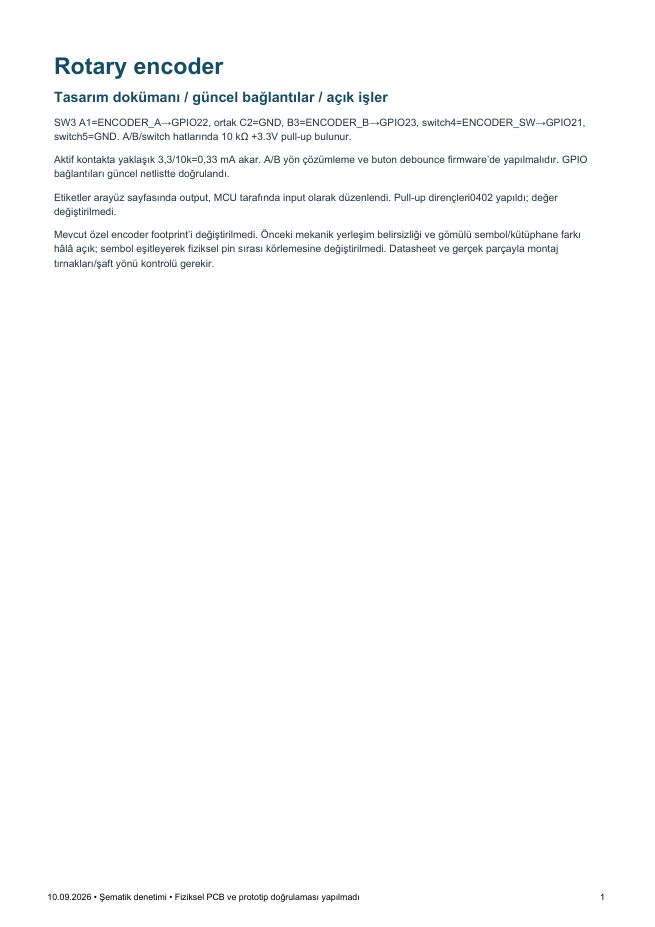
hardware/images/reports/output-update/pdf-review/06_ENCODER-1.png
