gokcesena53/usb-pd-power-supply/hardware/images/reports/output-update/pdf-review/07_POWER_GENERATION-3.png

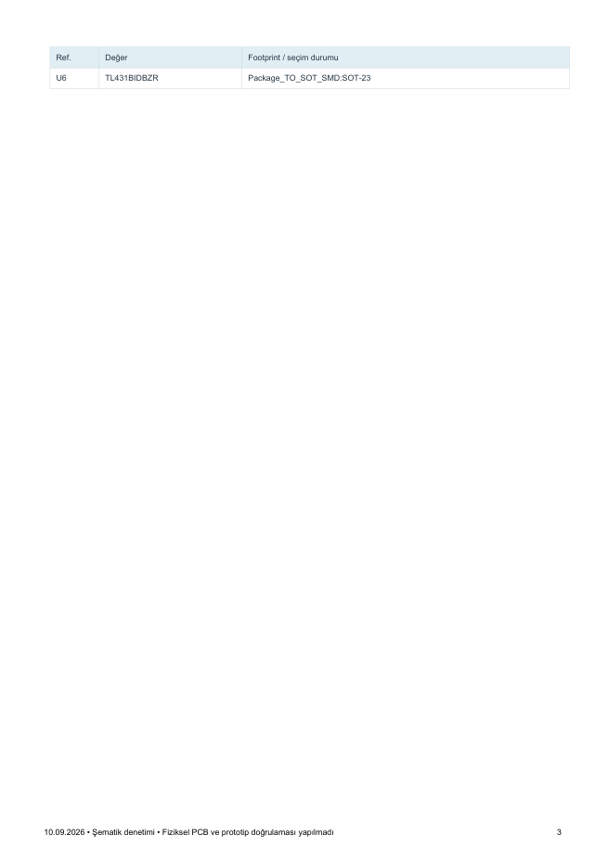
hardware/images/reports/output-update/pdf-review/07_POWER_GENERATION-3.png
