gokcesena53/usb-pd-power-supply/hardware/images/reports/output-update/pdf-review/08_POWER_SENSING-1.png

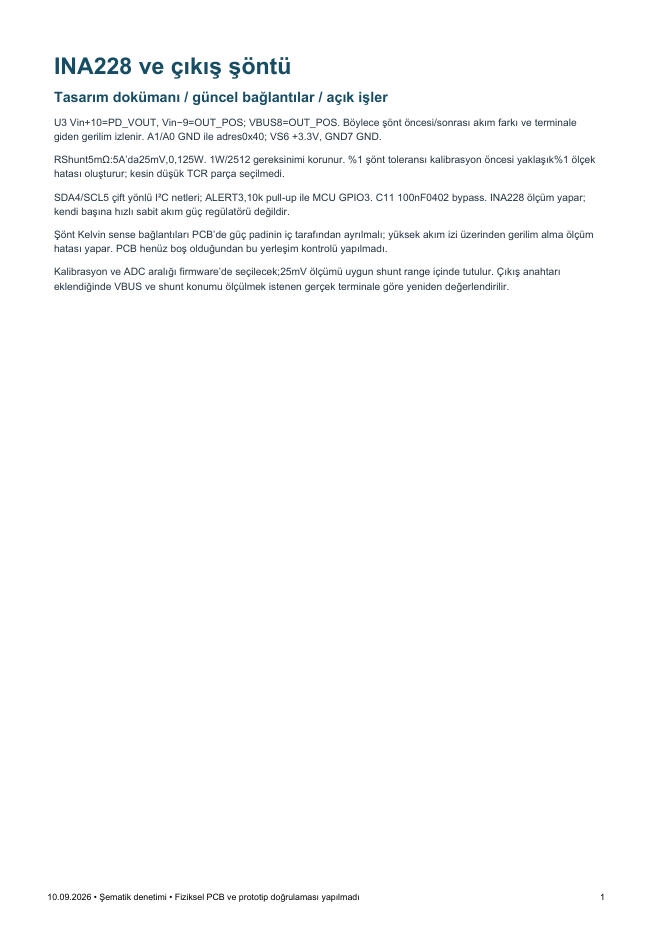
hardware/images/reports/output-update/pdf-review/08_POWER_SENSING-1.png
