gokcesena53/usb-pd-power-supply/hardware/images/reports/output-update/pdf-review/08_POWER_SENSING-2.png

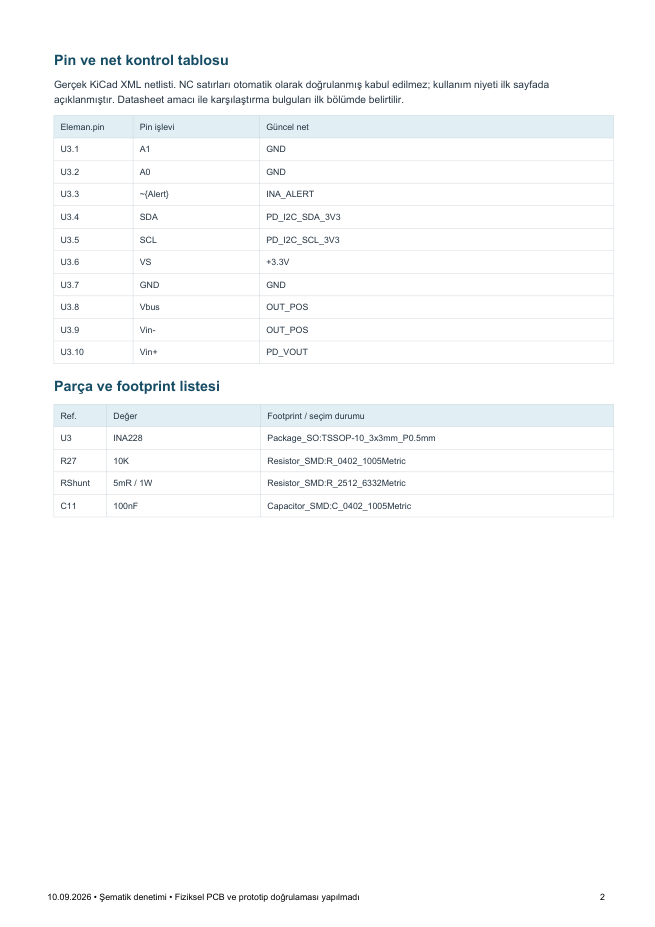
hardware/images/reports/output-update/pdf-review/08_POWER_SENSING-2.png
