gokcesena53/usb-pd-power-supply/hardware/images/reports/output-update/pdf-review/08_POWER_SENSING-3.png

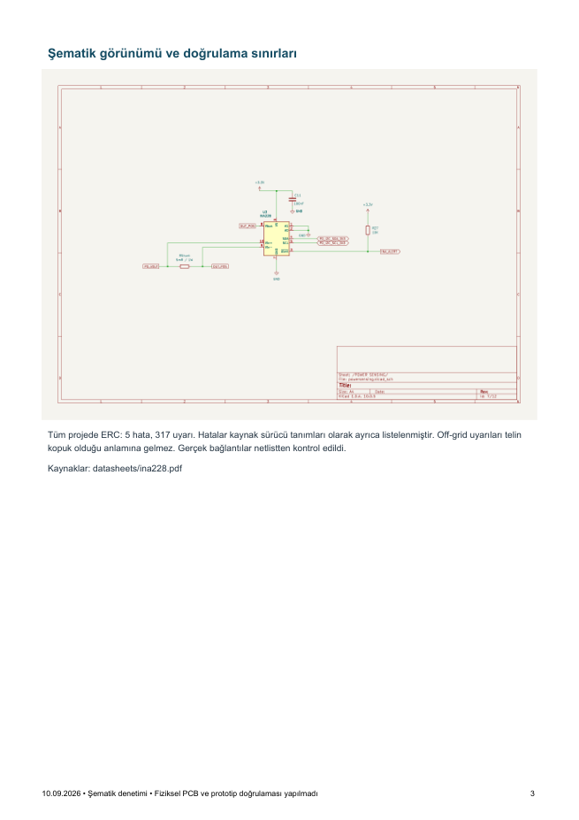
hardware/images/reports/output-update/pdf-review/08_POWER_SENSING-3.png
