gokcesena53/usb-pd-power-supply/hardware/images/reports/output-update/pdf-review/09_POWER_OUTPUT-3.png

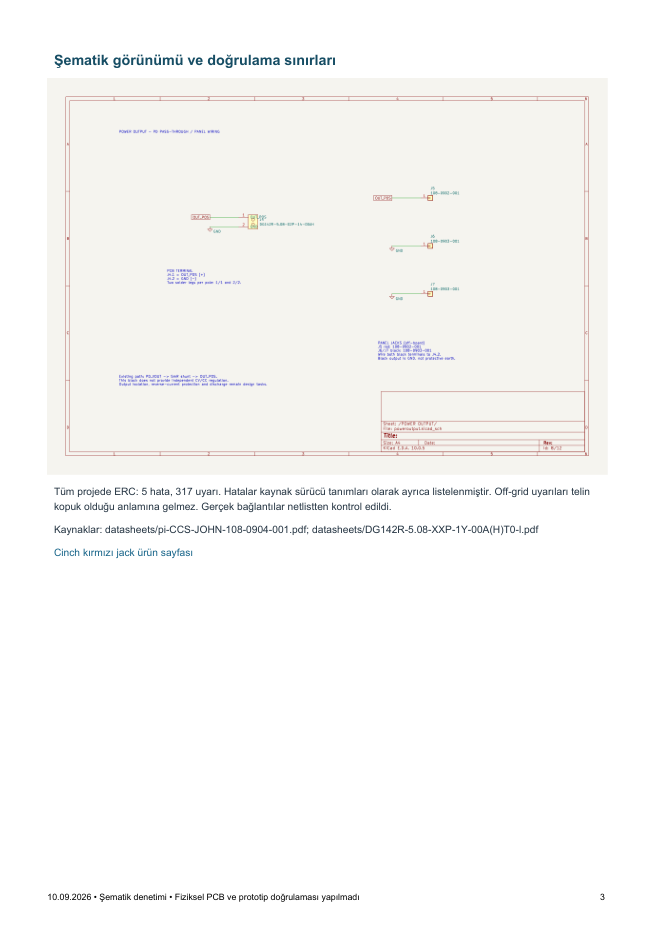
hardware/images/reports/output-update/pdf-review/09_POWER_OUTPUT-3.png
