gokcesena53/usb-pd-power-supply/hardware/images/reports/output-update/pdf-review/final-1.png

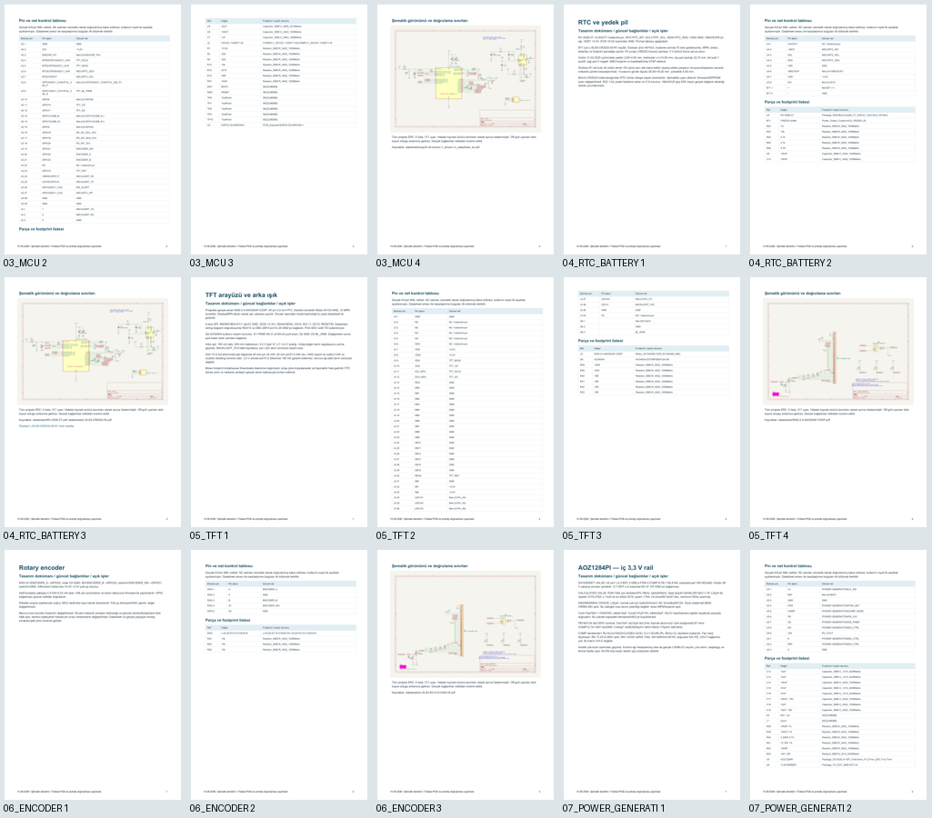
hardware/images/reports/output-update/pdf-review/final-1.png
