gokcesena53/usb-pd-power-supply/hardware/images/reports/output-update/pi-CCS-JOHN-108-0904-001.pdf.png

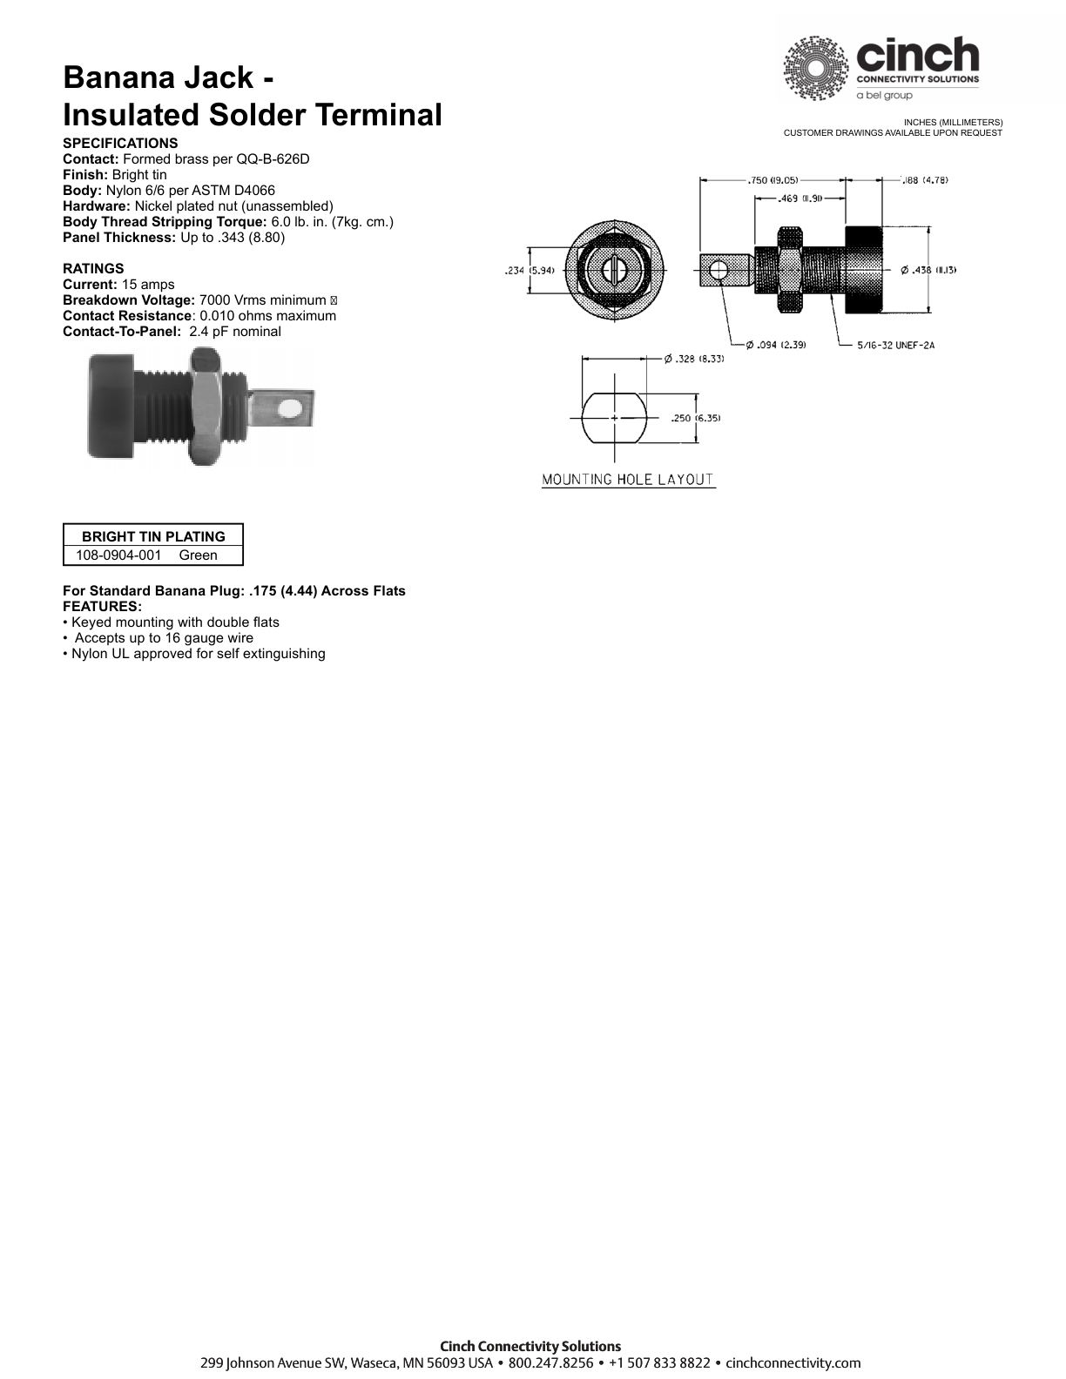
hardware/images/reports/output-update/pi-CCS-JOHN-108-0904-001.pdf.png
