gokcesena53/usb-pd-power-supply/hardware/images/reports/output-update/svg/masaüstü güç kaynağı-POWER GENERATION.png

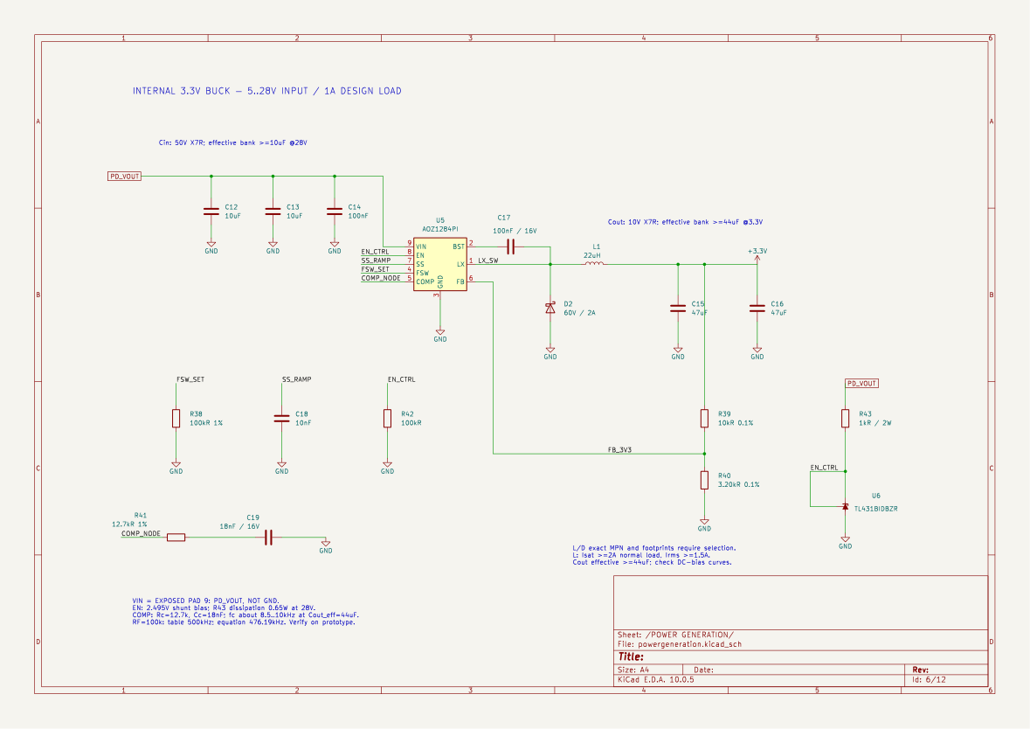
hardware/images/reports/output-update/svg/masaüstü güç kaynağı-POWER GENERATION.png
