gokcesena53/usb-pd-power-supply/hardware/images/reports/output-update/svg/masaüstü güç kaynağı-POWER SENSING.png

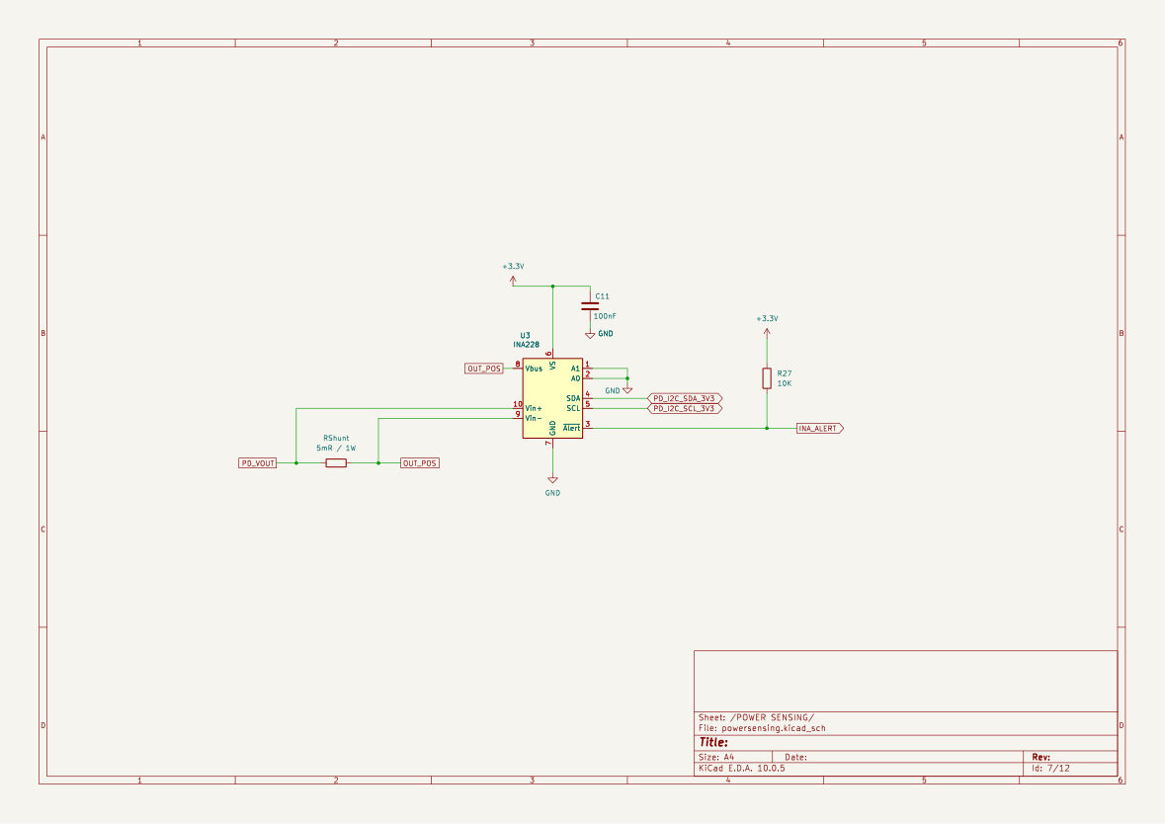
hardware/images/reports/output-update/svg/masaüstü güç kaynağı-POWER SENSING.png
