gokcesena53/usb-pd-power-supply/hardware/images/reports/output-update/svg/masaüstü güç kaynağı-USB_C_INPUT.png

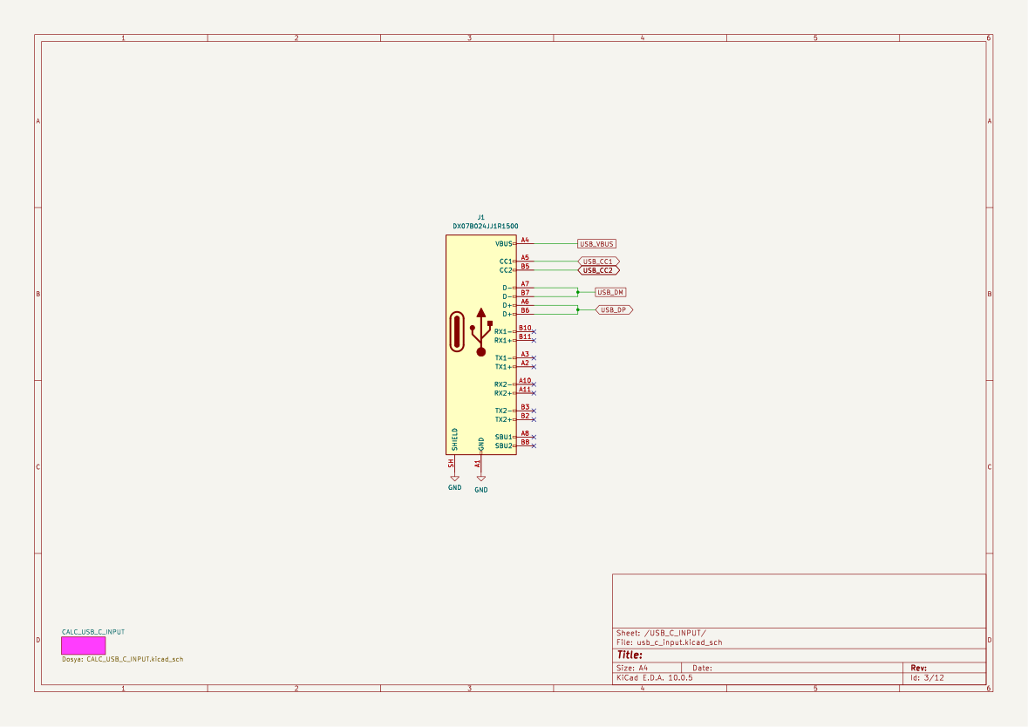
hardware/images/reports/output-update/svg/masaüstü güç kaynağı-USB_C_INPUT.png
