gokcesena53/usb-pd-power-supply/hardware/images/reports/output-update/svg/masaüstü güç kaynağı-USB_PD_CONTROLLER.png

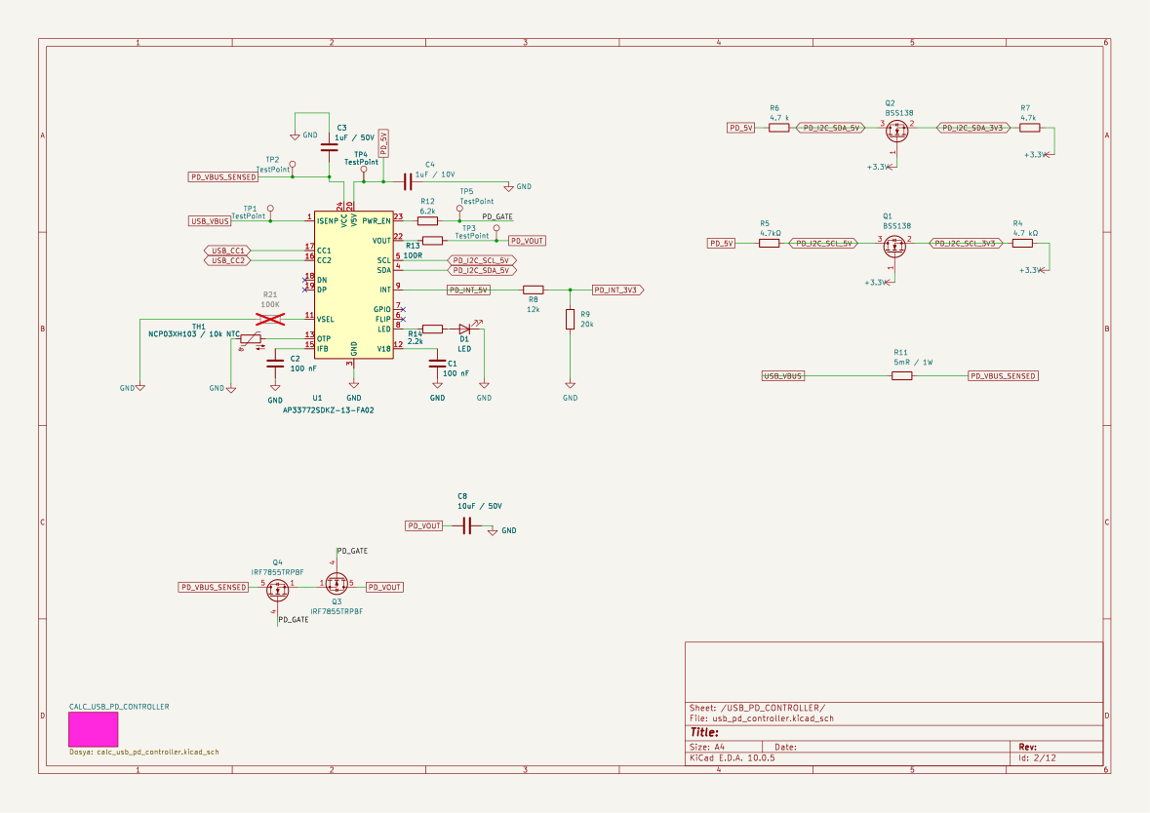
hardware/images/reports/output-update/svg/masaüstü güç kaynağı-USB_PD_CONTROLLER.png
