gokcesena53/usb-pd-power-supply/hardware/images/reports/output-update/svg/masaüstü güç kaynağı-USER INTERFACE.png

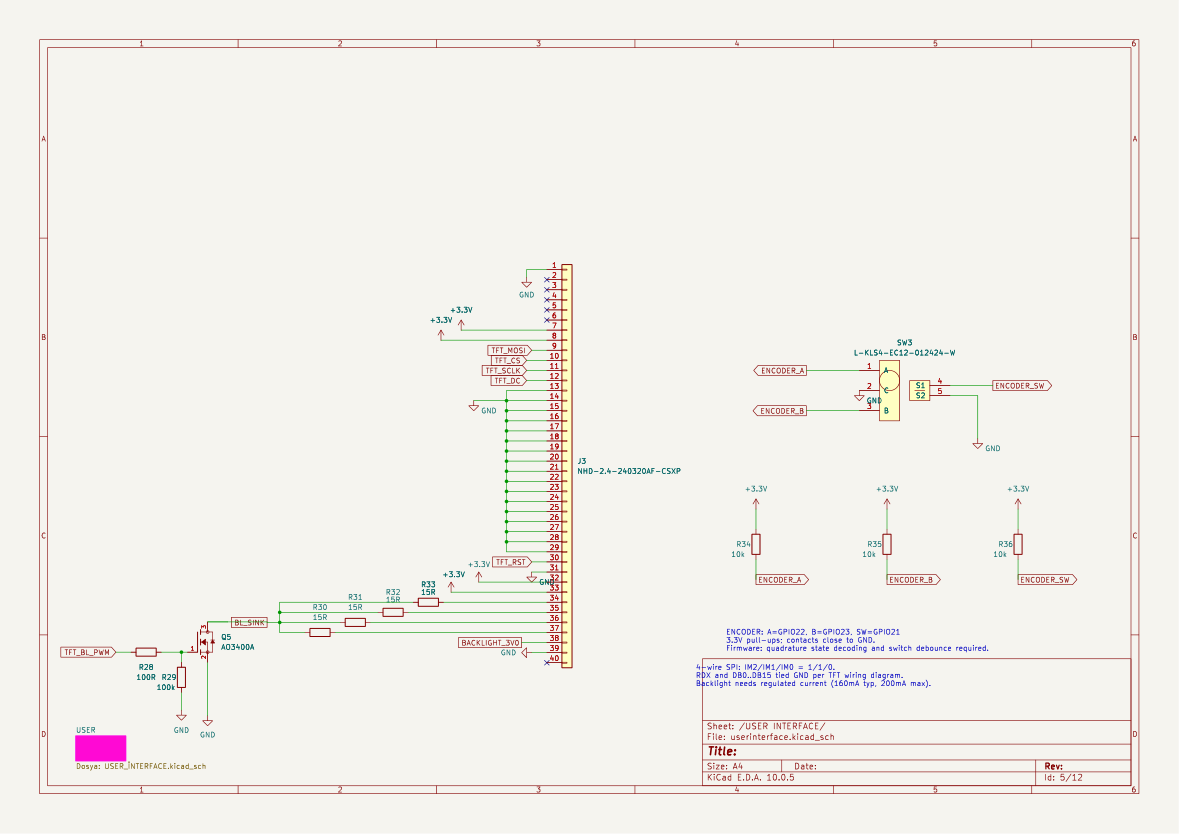
hardware/images/reports/output-update/svg/masaüstü güç kaynağı-USER INTERFACE.png
