gokcesena53/usb-pd-power-supply/hardware/images/reports/output-update/terminal-upright.png

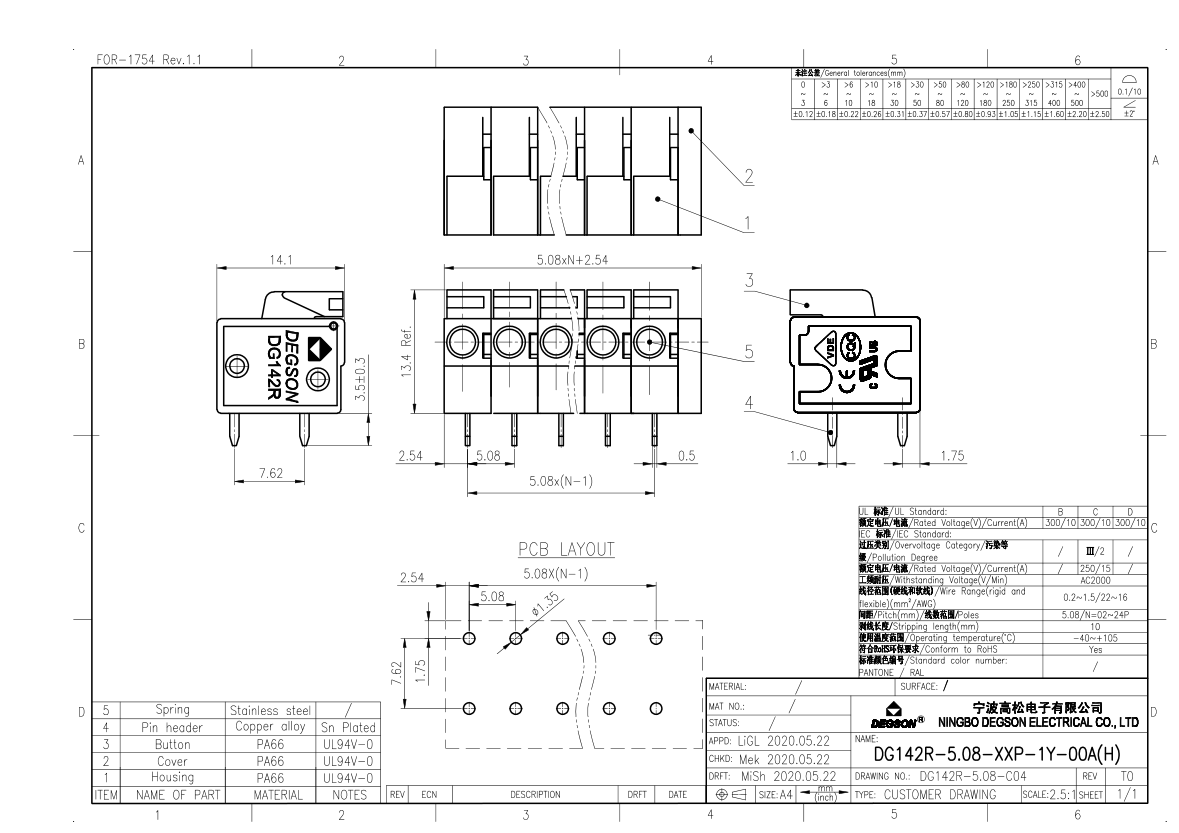
hardware/images/reports/output-update/terminal-upright.png
