gokcesena53/usb-pd-power-supply/hardware/images/reports/recheck-20260911/pdf-review/contact-0.png

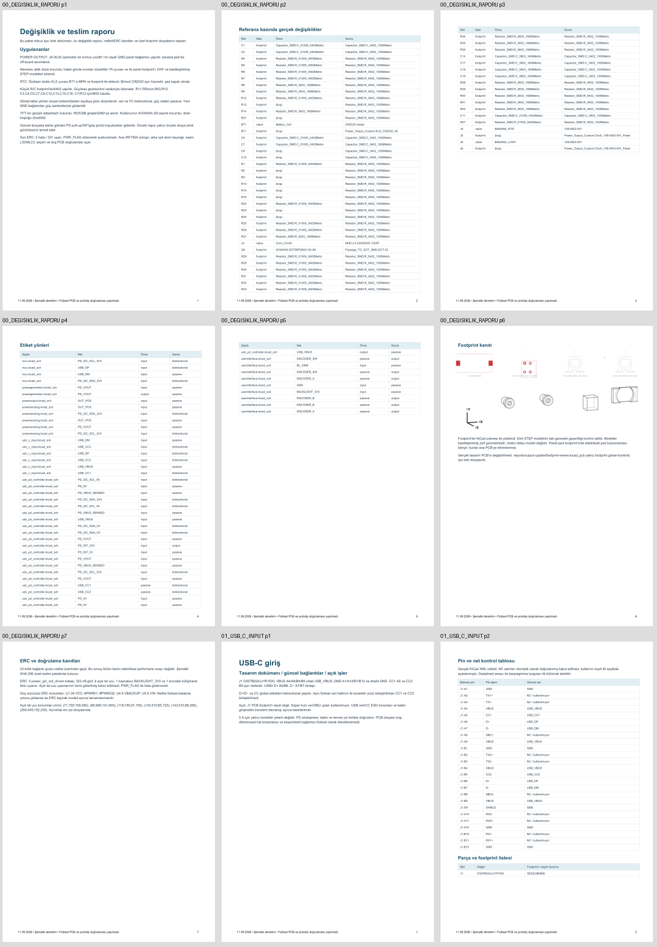
hardware/images/reports/recheck-20260911/pdf-review/contact-0.png
