gokcesena53/usb-pd-power-supply/hardware/images/reports/recheck-20260911/pdf-review/final-updated.png

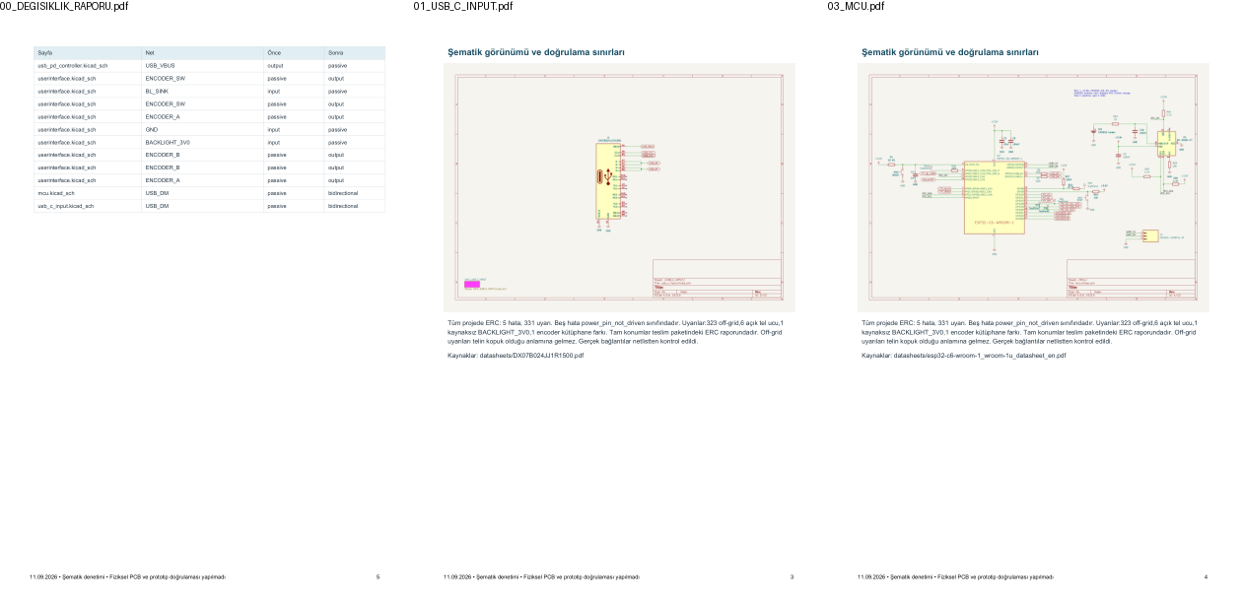
hardware/images/reports/recheck-20260911/pdf-review/final-updated.png
