gokcesena53/usb-pd-power-supply/hardware/images/reports/recheck-20260911/svg/masaüstü güç kaynağı-POWER GENERATION.png

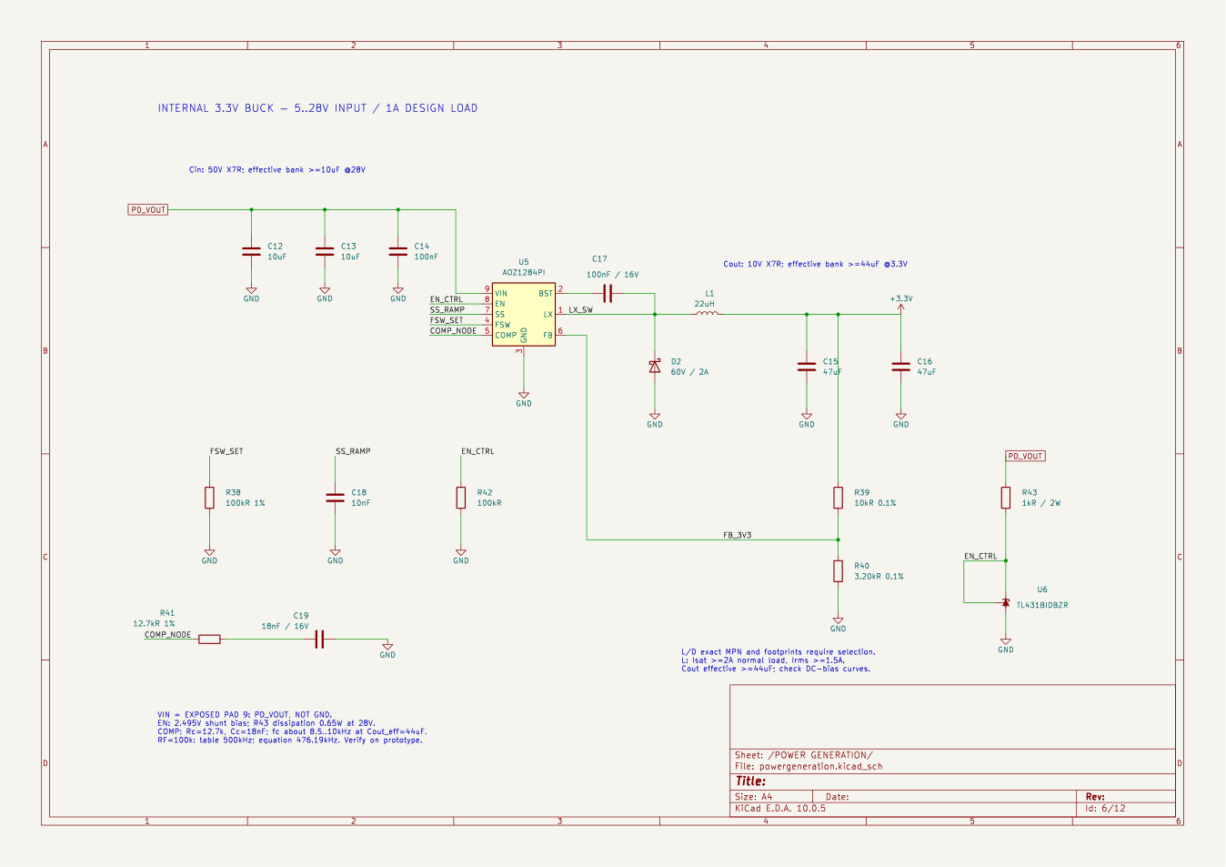
hardware/images/reports/recheck-20260911/svg/masaüstü güç kaynağı-POWER GENERATION.png
