gokcesena53/usb-pd-power-supply/hardware/images/reports/recheck-20260911/svg/masaüstü güç kaynağı-USB_C_INPUT.png

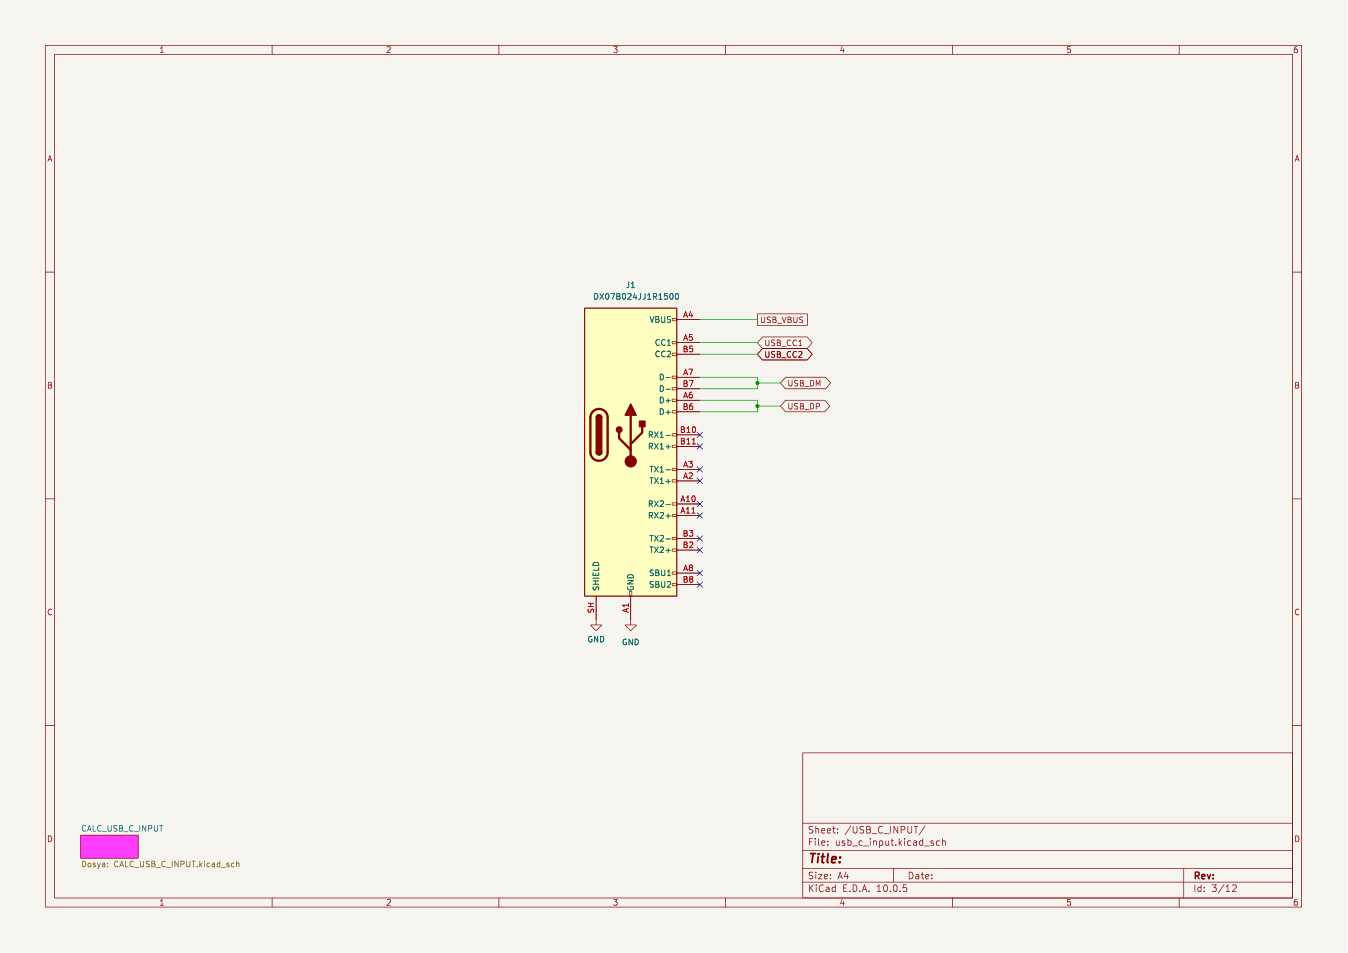
hardware/images/reports/recheck-20260911/svg/masaüstü güç kaynağı-USB_C_INPUT.png
