gokcesena53/usb-pd-power-supply/hardware/images/reports/recheck-20260911/svg/masaüstü güç kaynağı-USB_PD_CONTROLLER.png

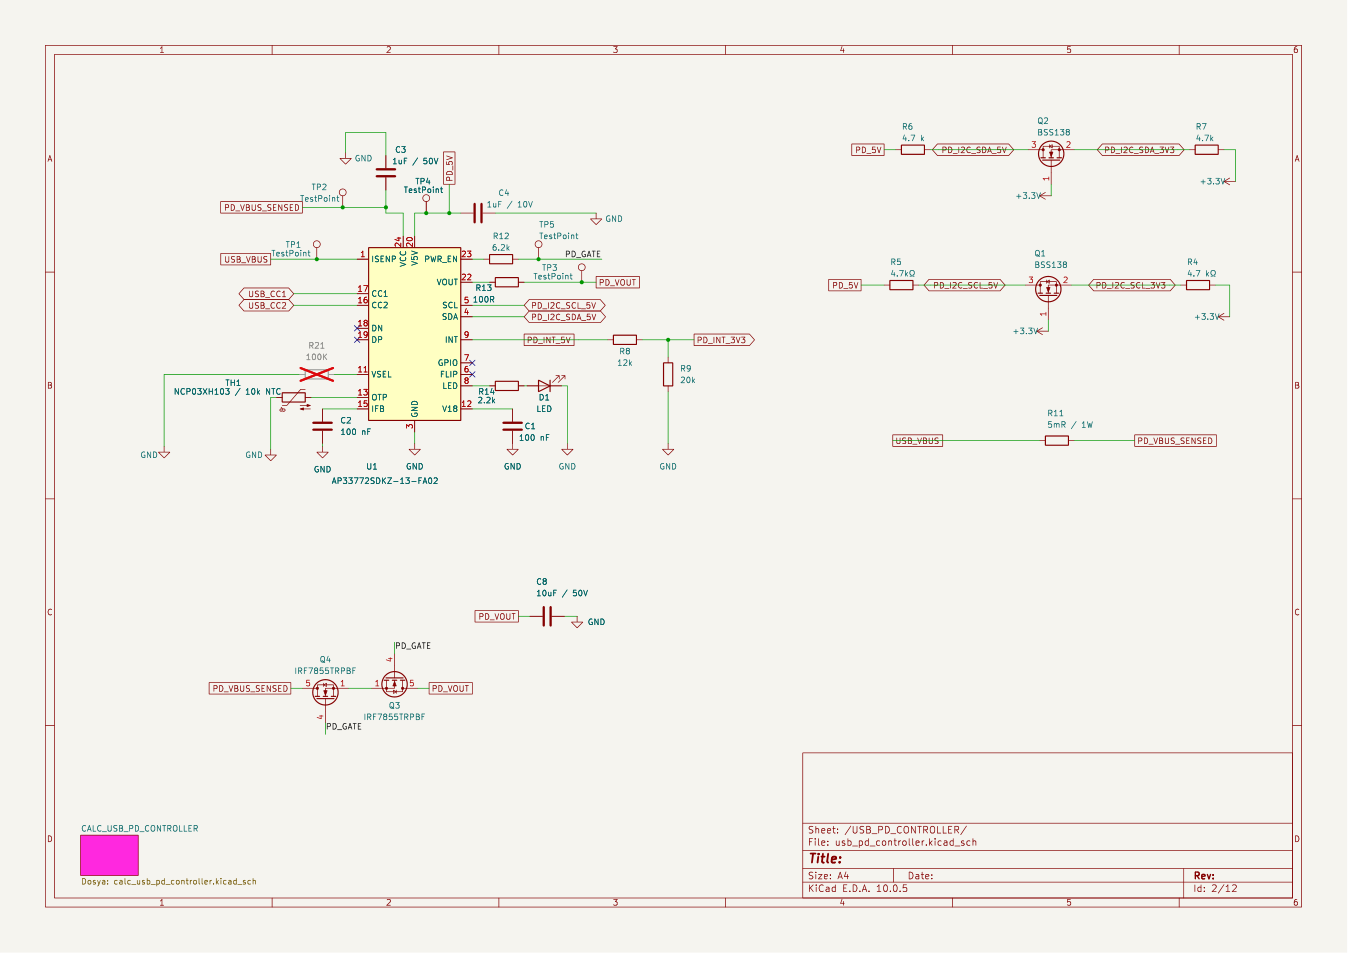
hardware/images/reports/recheck-20260911/svg/masaüstü güç kaynağı-USB_PD_CONTROLLER.png
