gokcesena53/usb-pd-power-supply/hardware/images/reports/review-20260910/svg/masaüstü güç kaynağı-POWER OUTPUT.png

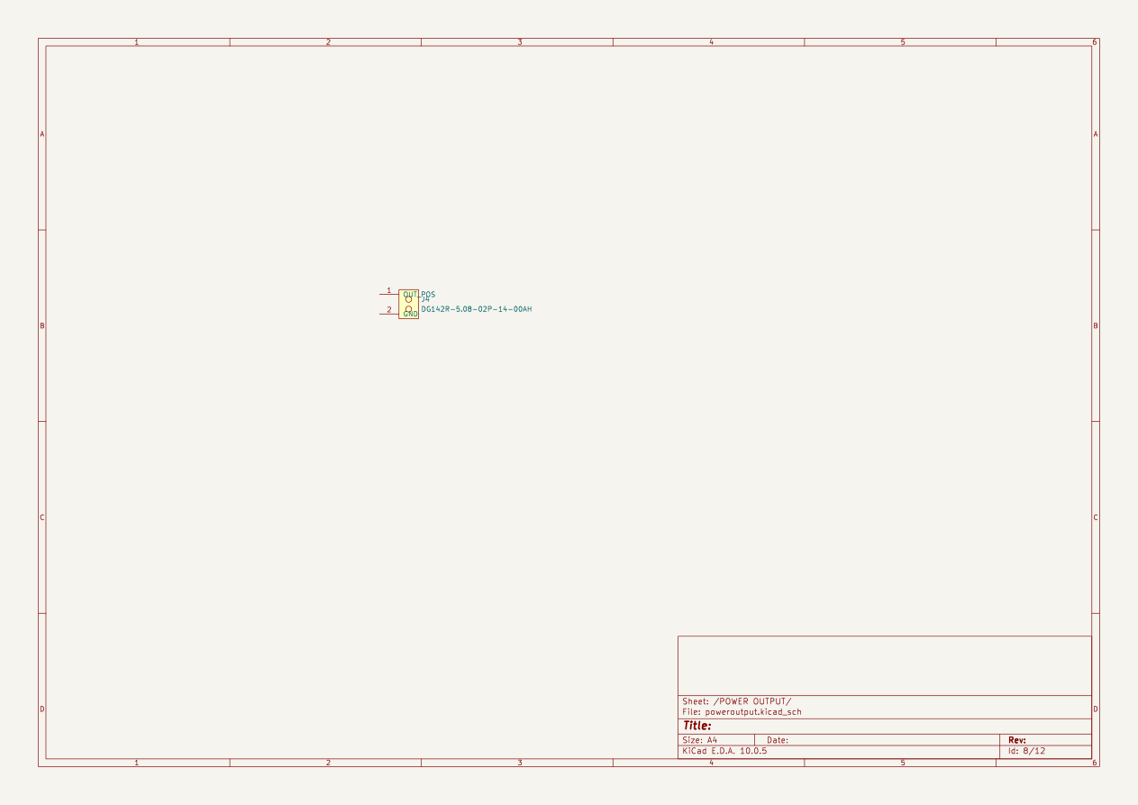
hardware/images/reports/review-20260910/svg/masaüstü güç kaynağı-POWER OUTPUT.png
