gokcesena53/usb-pd-power-supply/hardware/images/reports/usb-esd-20260911/usb-input.png

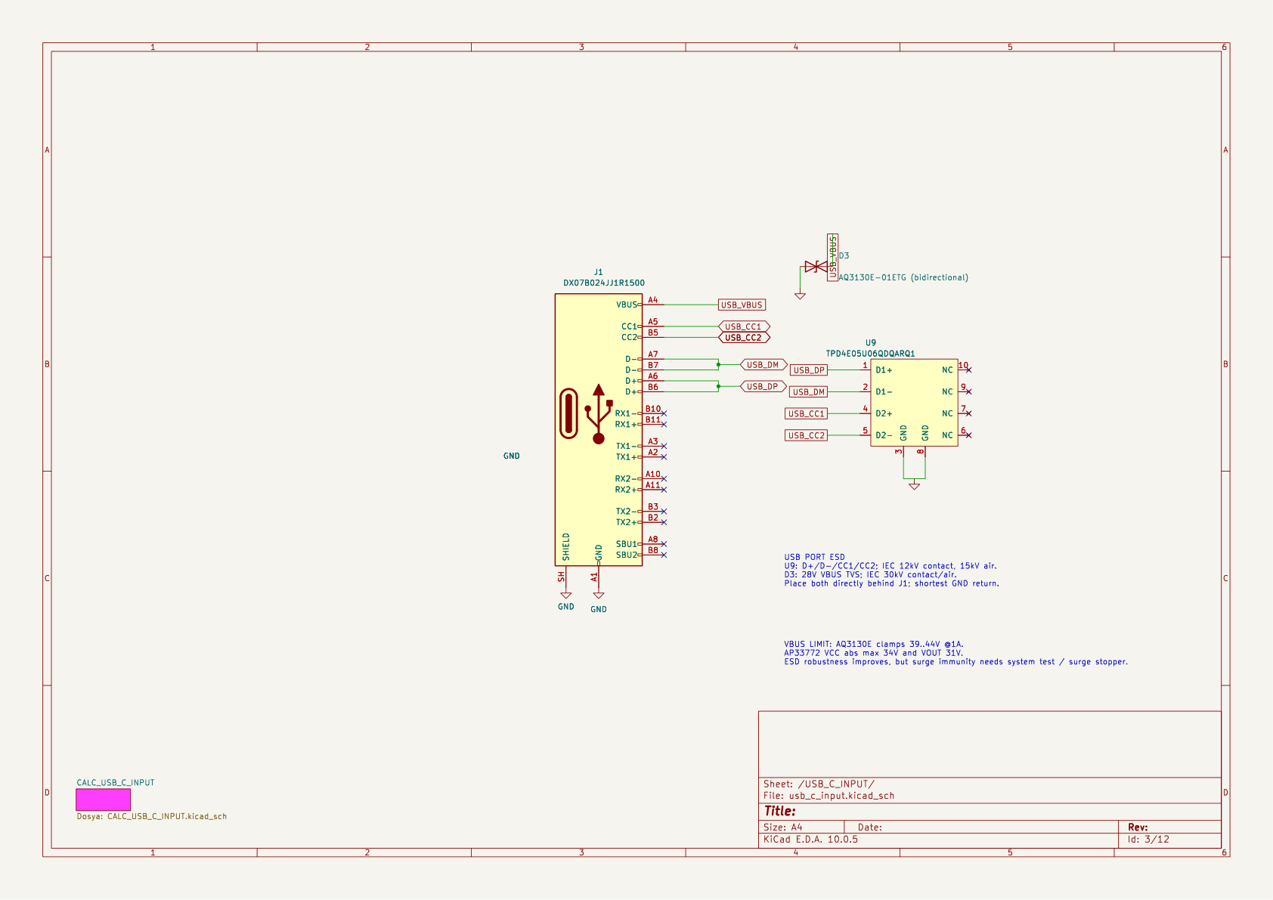
hardware/images/reports/usb-esd-20260911/usb-input.png
