gokcesena53/usb-pd-power-supply/hardware/docs/reports/task-094-20260925/board-body.step

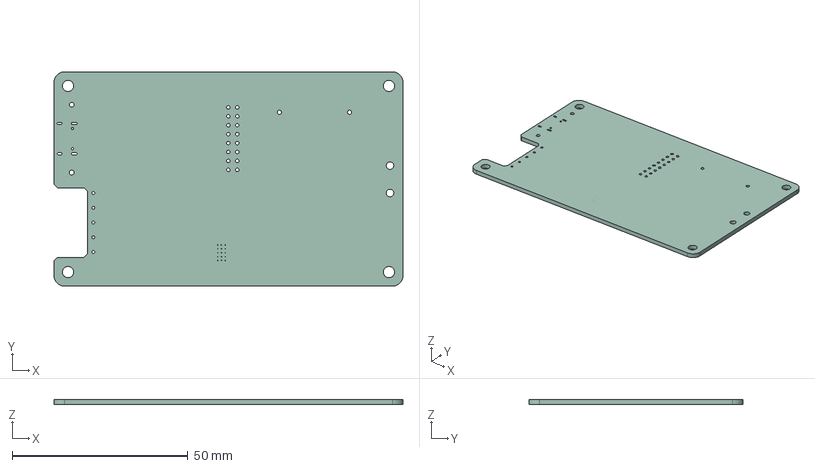
[picture p149: CAD file, 2026-09-30]
hardware/docs/reports/task-094-20260925/board-body.step
99.4 x 61.0 x 1.51 mm
