gokcesena53/usb-pd-power-supply/hardware/docs/reports/task-094-20260925/mechanical-review.step

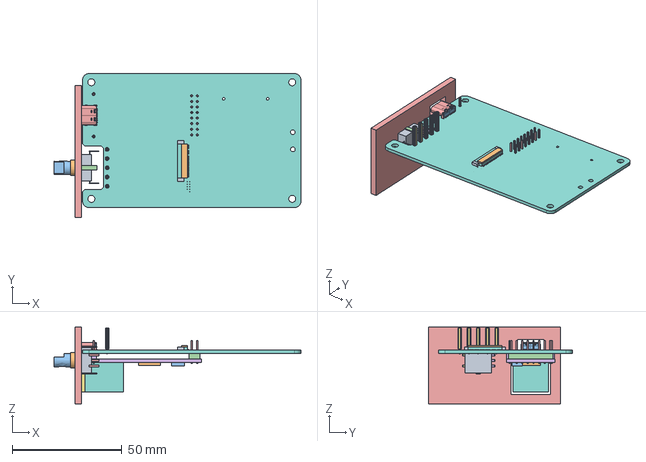
[picture p150: CAD file, 2026-09-30]
hardware/docs/reports/task-094-20260925/mechanical-review.step
112.4 x 65.5 x 35.0 mm
