gokcesena53/usb-pd-power-supply/hardware/docs/reports/task-095-20260928/Q3.step

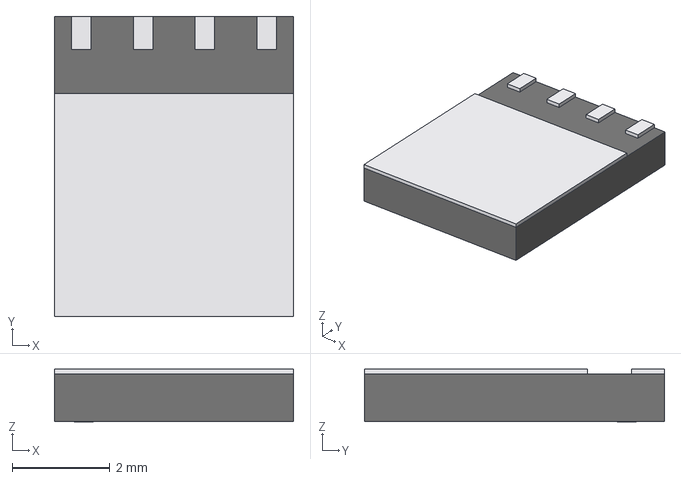
[picture p151: CAD file, 2026-09-30]
hardware/docs/reports/task-095-20260928/Q3.step
4.90 x 6.15 x 1.08 mm
