gokcesena53/usb-pd-power-supply/hardware/docs/reports/task-095-20260928/U1.step

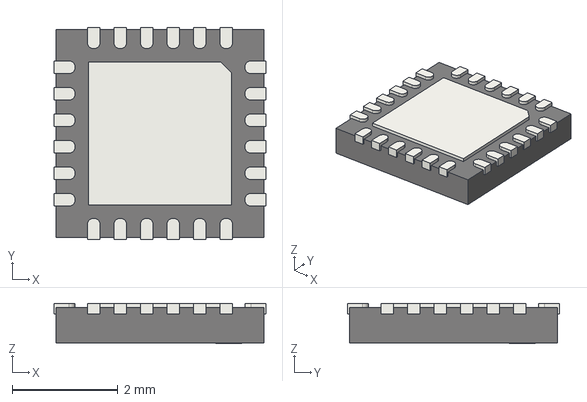
[picture p152: CAD file, 2026-09-30]
hardware/docs/reports/task-095-20260928/U1.step
4.00 x 4.00 x 0.76 mm
