gokcesena53/usb-pd-power-supply/hardware/docs/reports/task-095-20260928/D1.step

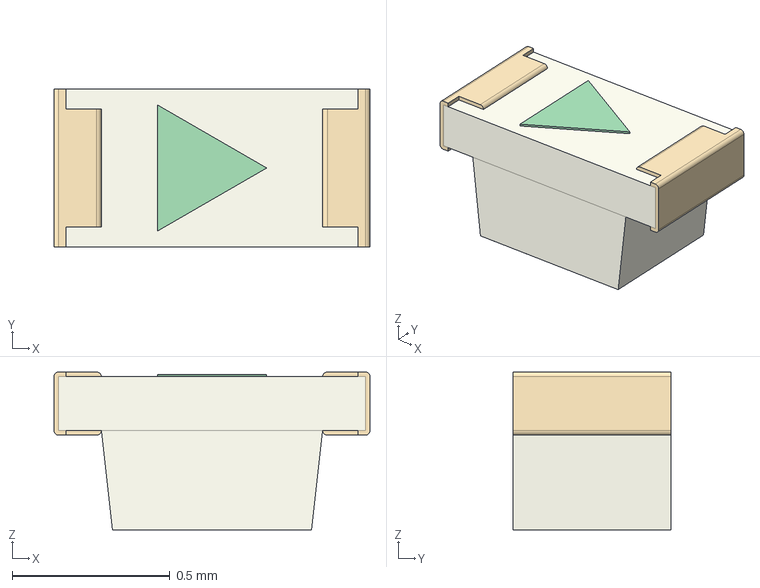
[picture p153: CAD file, 2026-09-30]
hardware/docs/reports/task-095-20260928/D1.step
1.00 x 0.5 x 0.5 mm
