gokcesena53/usb-pd-power-supply/hardware/images/reports/output-update/tft-wiring.png

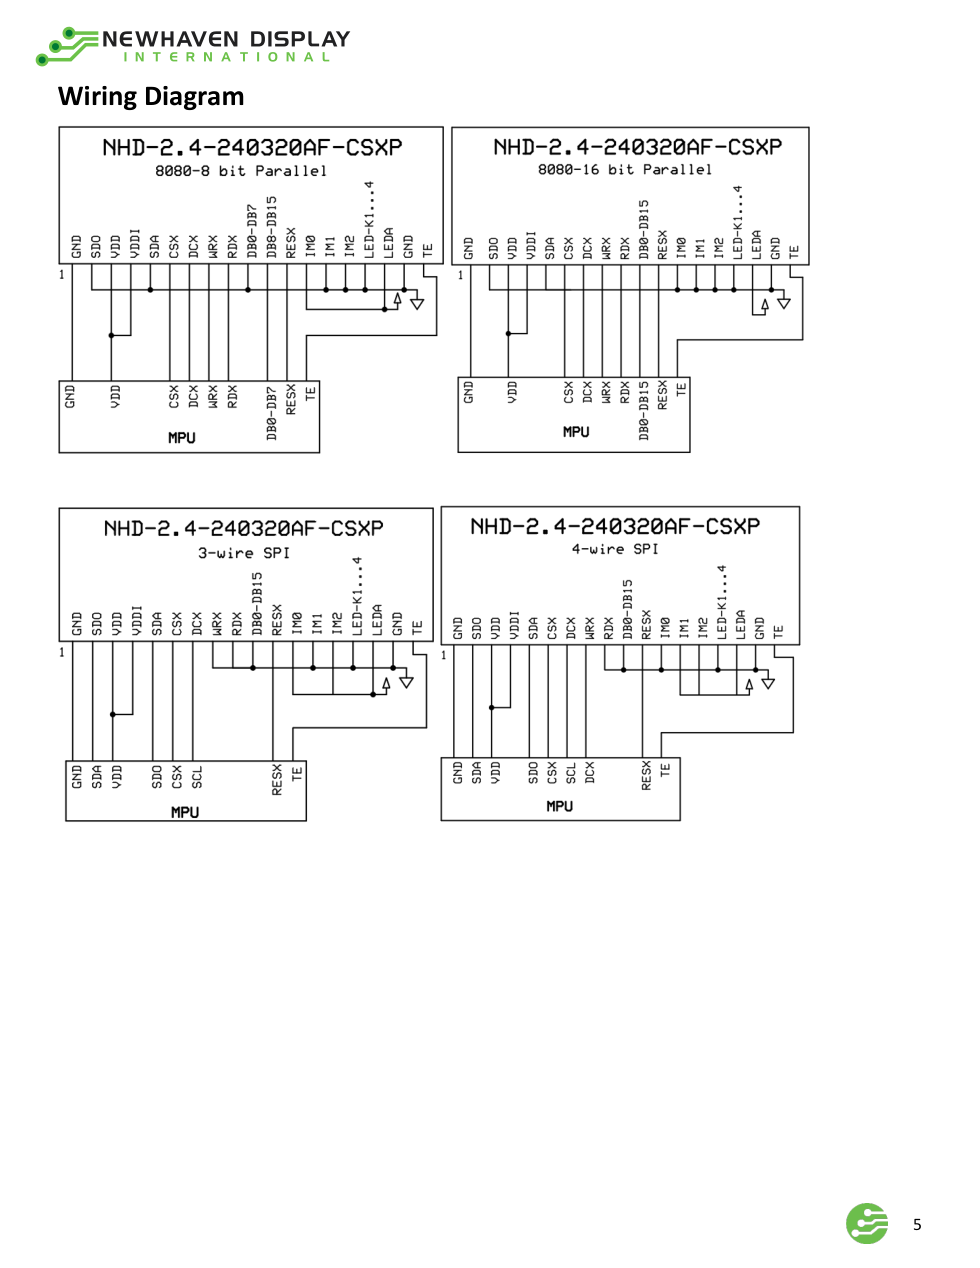
hardware/images/reports/output-update/tft-wiring.png
