gokcesena53/usb-pd-power-supply/hardware/docs/reports/port-stack-fix-20260925/final-bottom.png

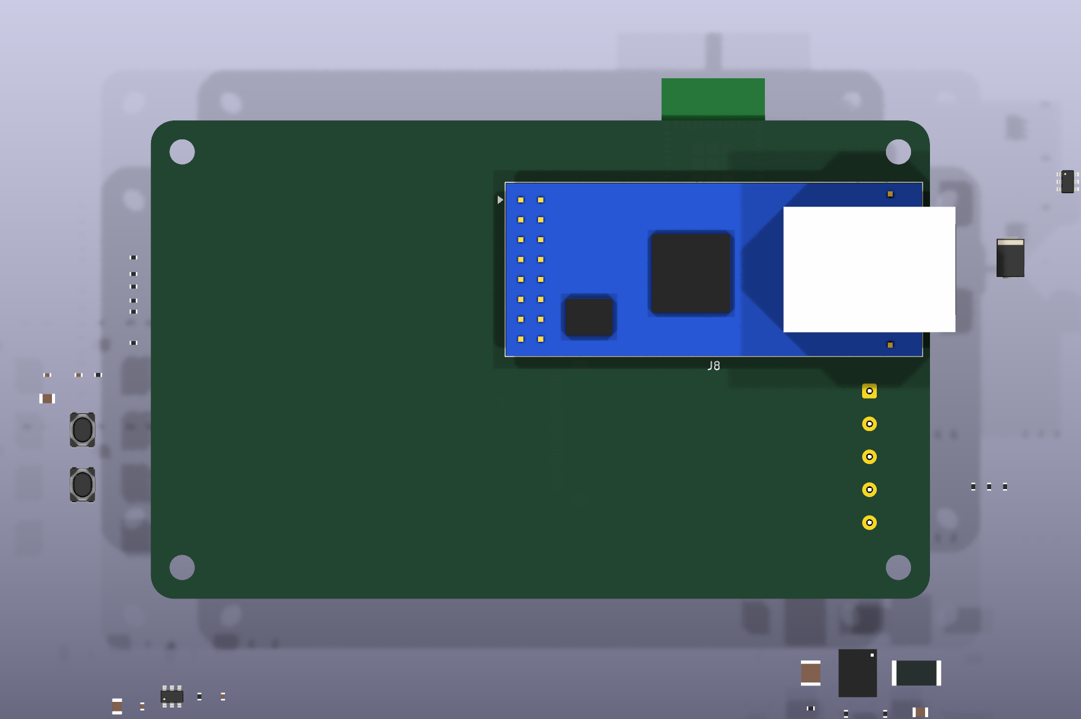
hardware/docs/reports/port-stack-fix-20260925/final-bottom.png
