gokcesena53/usb-pd-power-supply/hardware/images/reports/erc-fix-20260911/review-final.png

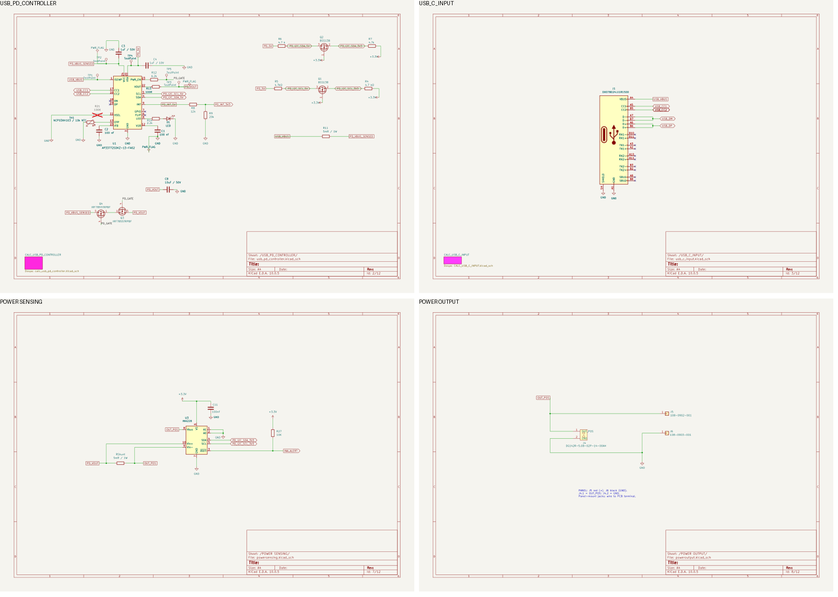
hardware/images/reports/erc-fix-20260911/review-final.png
