gokcesena53/usb-pd-power-supply/hardware/images/reports/erc-fix-20260911/svg/masaüstü güç kaynağı-POWER OUTPUT.png

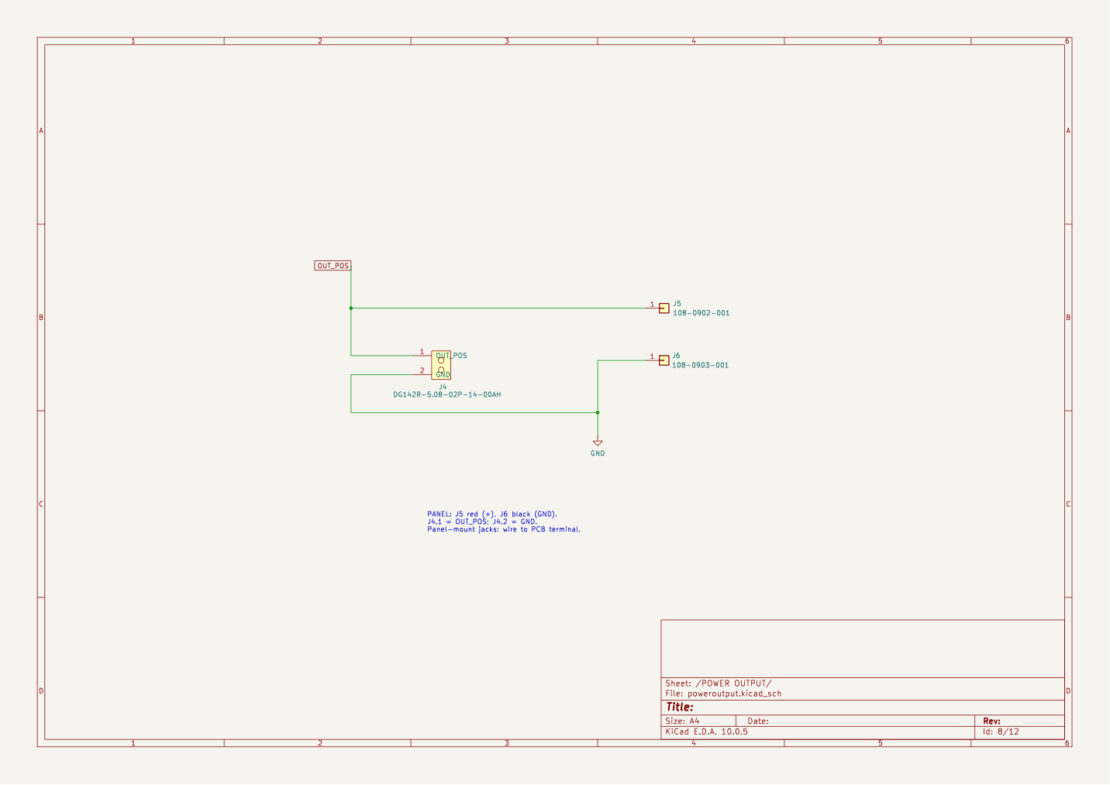
hardware/images/reports/erc-fix-20260911/svg/masaüstü güç kaynağı-POWER OUTPUT.png
