gokcesena53/usb-pd-power-supply/hardware/images/reports/fixes-20260909/svg-before/masaüstü güç kaynağı-USB_PD_CONTROLLER.png

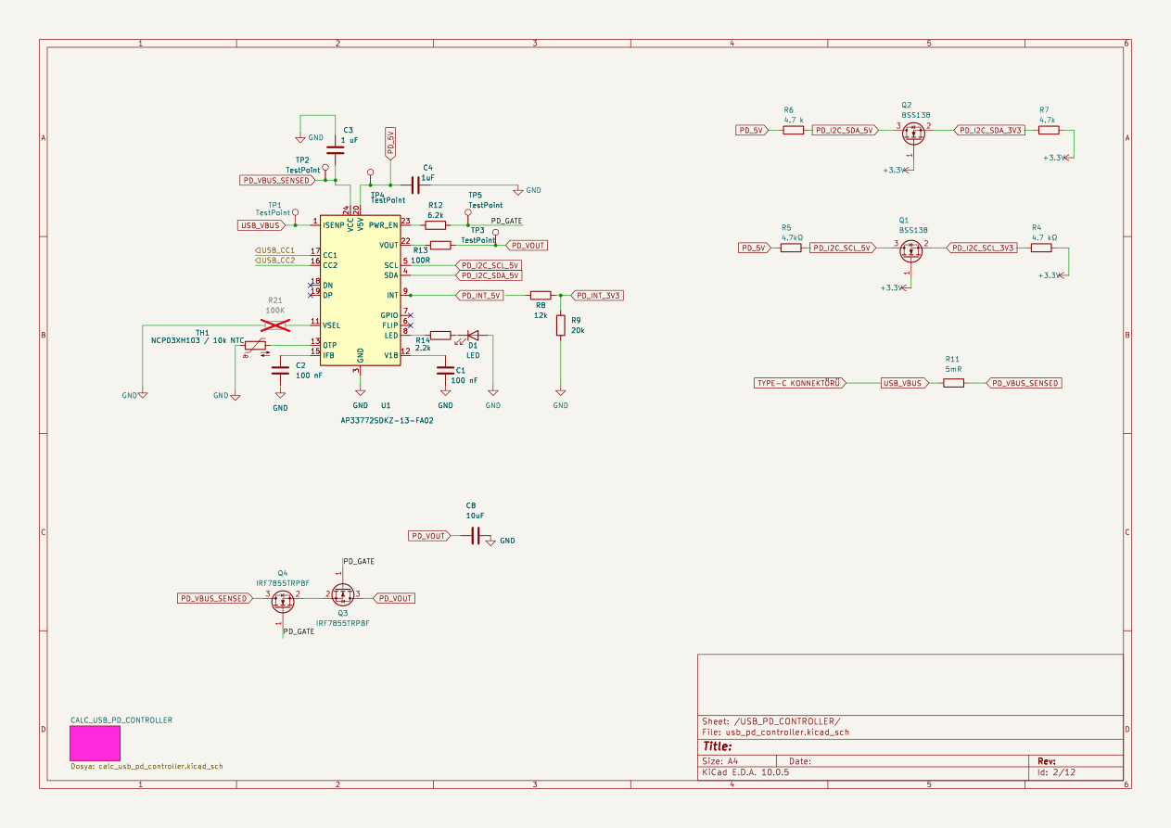
hardware/images/reports/fixes-20260909/svg-before/masaüstü güç kaynağı-USB_PD_CONTROLLER.png
