gokcesena53/usb-pd-power-supply/hardware/docs/reports/backlight-20260911/before/mcu.kicad_sch

## KiCad design hardware/docs/reports/backlight-20260911/before/mcu.kicad_sch (2026-09-11)

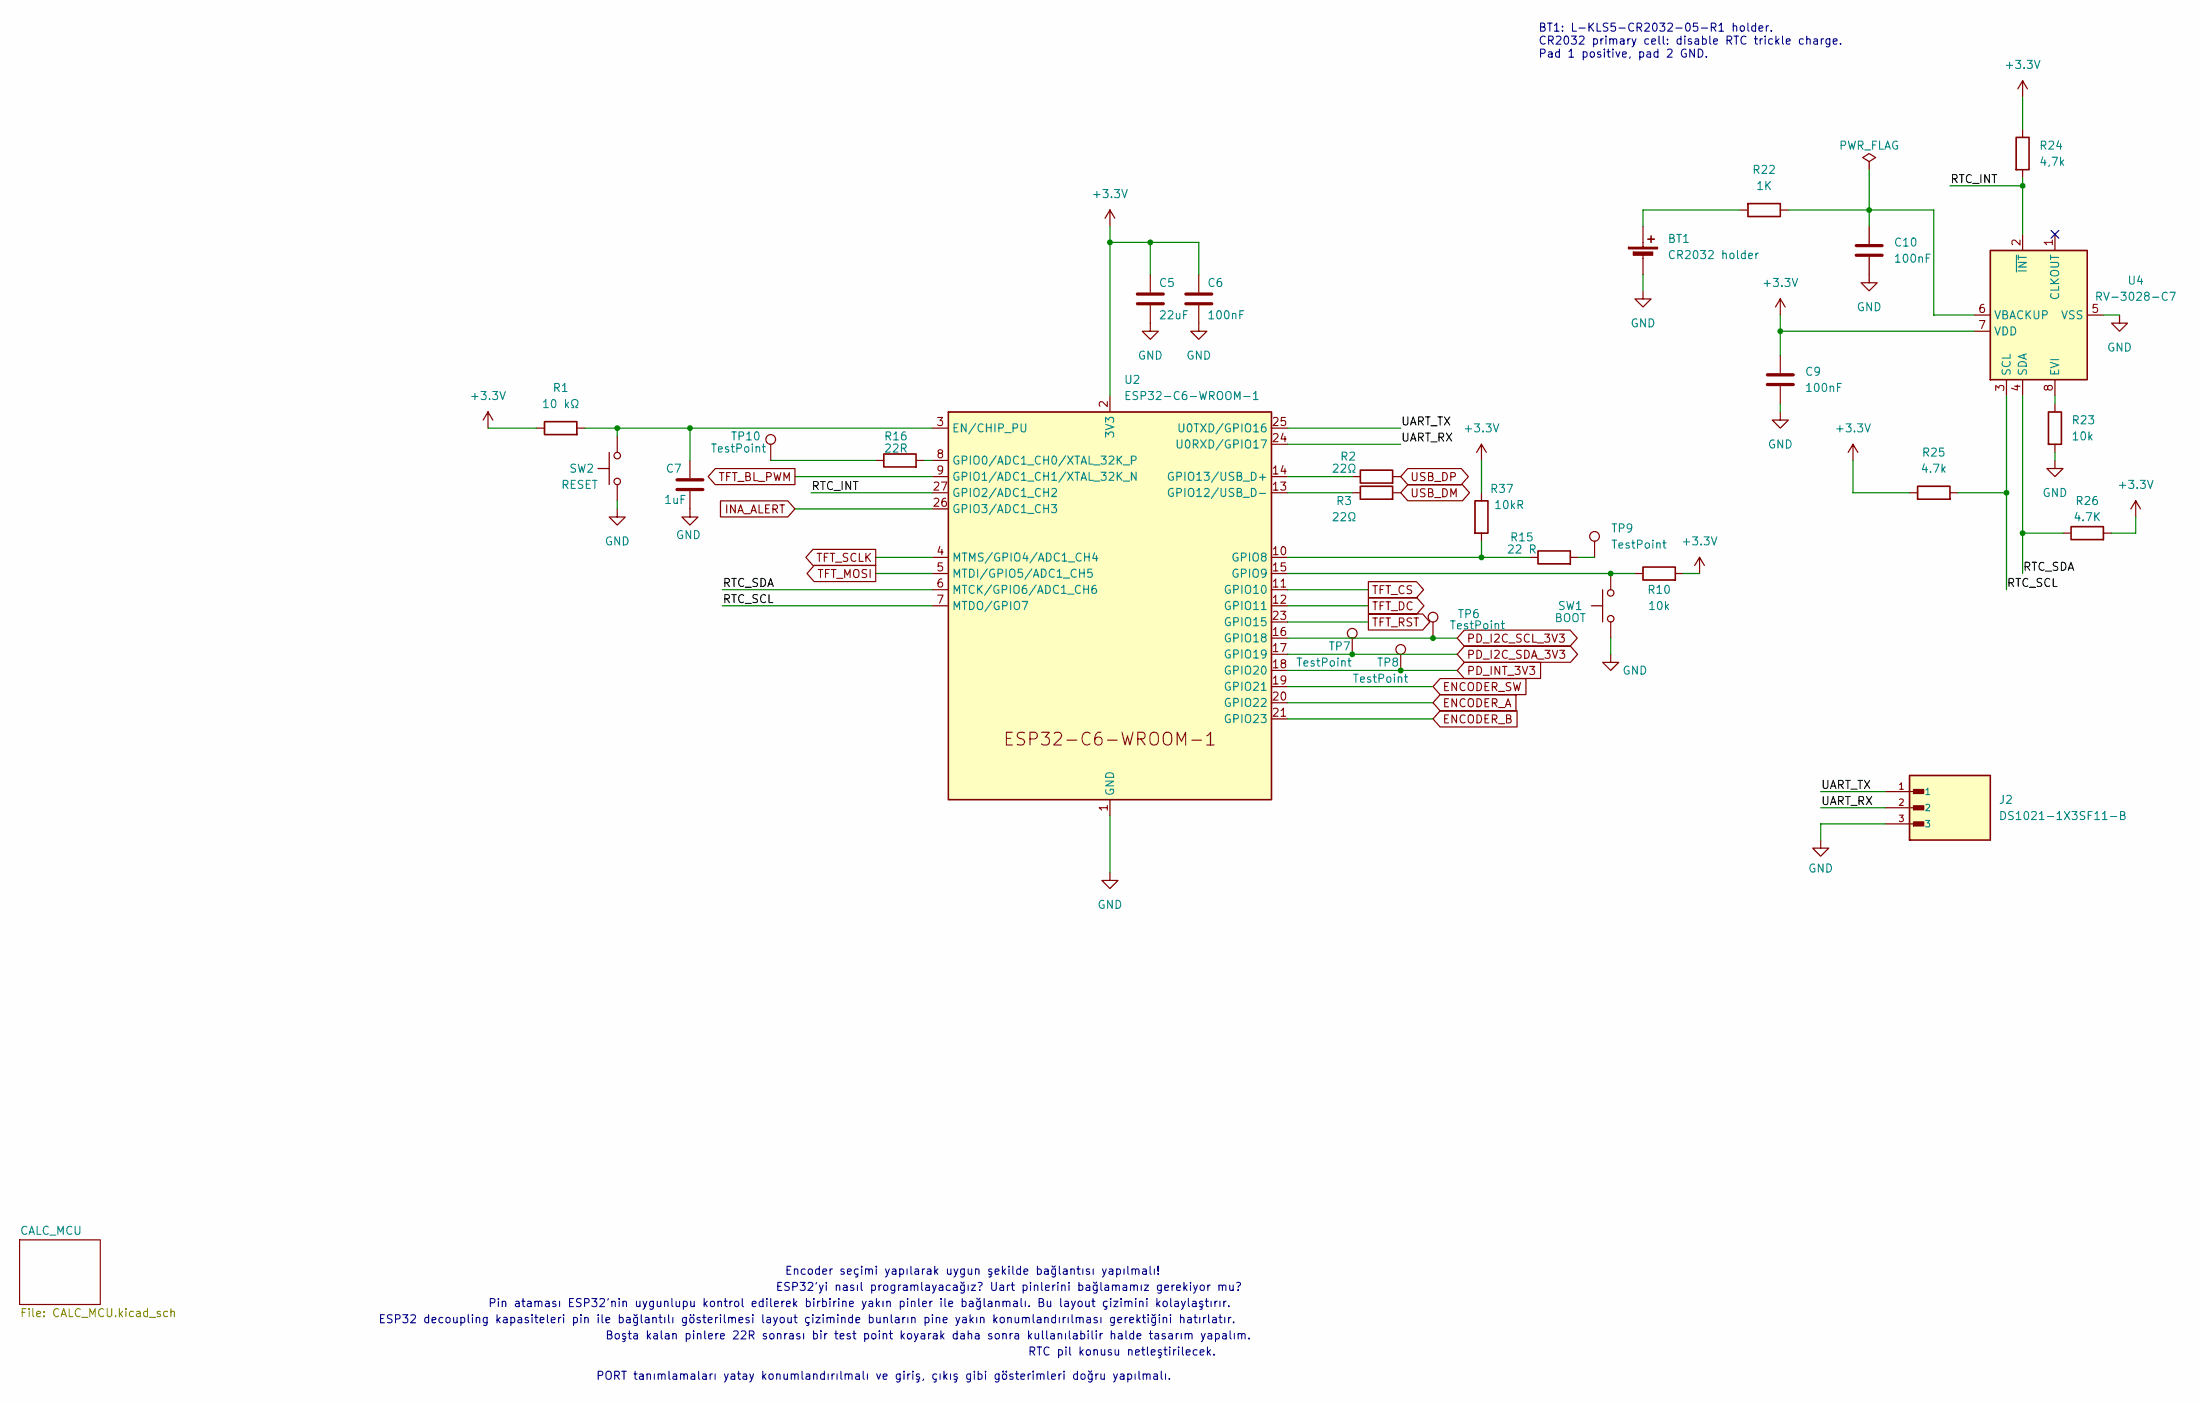
[picture p166: schematic mcu.kicad_sch]

Parts:
BT1: CR2032 holder; KLS_CR2032_05; MPN L-KLS5-CR2032-05-R1
C5: 22uF; C_0805_2012Metric
C6, C9, C10: 100nF; C_0402_1005Metric
C7: 1uF; C_0603_1608Metric
J2: DS1021-1X3SF11-B; CONNFLY_DS1021-1X3SF11-B
R1: 10 kΩ; R_0402_1005Metric
R2, R3: 22Ω; R_0402_1005Metric
R10, R23: 10k; R_0402_1005Metric
R15: 22 R; R_0402_1005Metric
R16: 22R; R_0402_1005Metric
R22: 1K; R_0402_1005Metric
R24: 4,7k; R_0402_1005Metric
R25: 4.7k; R_0402_1005Metric
R26: 4.7K; R_0402_1005Metric
R37: 10kR; R_0402_1005Metric
SW1: BOOT
SW2: RESET
TP6, TP7, TP8, TP9, TP10: TestPoint
U2: ESP32-C6-WROOM-1
U4: RV-3028-C7; MicroCrystal_C7_SON-8_1.5x3.2mm_P0.9mm

Connections:
+3.3V: C5.1, C6.1, C9.1, R1.1, R10.2, R24.1, R25.1, R26.2, R37.1, U2.2 (3V3), U4.7 (VDD)
ENCODER_A: U2.20 (GPIO22)
ENCODER_B: U2.21 (GPIO23)
ENCODER_SW: U2.19 (GPIO21)
GND: BT1.2 (-), C5.2, C6.2, C7.1, C9.2, C10.2, J2.3, R23.2, SW1.1, SW2.1, U2.1 (GND), U2.28 (GND), U2.29 (GND), U4.5 (VSS)
INA_ALERT: U2.26 (GPIO3/ADC1_CH3)
unnamed: BT1.1 (+), R22.2
unnamed: C7.2, R1.2, SW2.2, U2.3 (EN/CHIP_PU)
unnamed: C10.1, R22.1, U4.6 (VBACKUP)
unnamed: R2.1, U2.14 (GPIO13/USB_D+)
unnamed: R3.1, U2.13 (GPIO12/USB_D-)
unnamed: R10.1, SW1.2, U2.15 (GPIO9)
unnamed: R15.1, R37.2, U2.10 (GPIO8)
unnamed: R15.2, TP9.1
unnamed: R16.1, TP10.1
unnamed: R16.2, U2.8 (GPIO0/ADC1_CH0/XTAL_32K_P)
unnamed: R23.1, U4.8 (EVI)
PD_I2C_SCL_3V3: TP6.1, U2.16 (GPIO18)
PD_I2C_SDA_3V3: TP7.1, U2.17 (GPIO19)
PD_INT_3V3: TP8.1, U2.18 (GPIO20)
RTC_INT: R24.2, U2.27 (GPIO2/ADC1_CH2), U4.2 (~INT)
RTC_SCL: R25.2, U2.7 (MTDO/GPIO7), U4.3 (SCL)
RTC_SDA: R26.1, U2.6 (MTCK/GPIO6/ADC1_CH6), U4.4 (SDA)
TFT_BL_PWM: U2.9 (GPIO1/ADC1_CH1/XTAL_32K_N)
TFT_CS: U2.11 (GPIO10)
TFT_DC: U2.12 (GPIO11)
TFT_MOSI: U2.5 (MTDI/GPIO5/ADC1_CH5)
TFT_RST: U2.23 (GPIO15)
TFT_SCLK: U2.4 (MTMS/GPIO4/ADC1_CH4)
UART_RX: J2.2, U2.24 (U0RXD/GPIO17)
UART_TX: J2.1, U2.25 (U0TXD/GPIO16)
USB_DM: R3.2
USB_DP: R2.2

Notes on the sheet:
PORT tanımlamaları yatay konumlandırılmalı ve giriş, çıkış gibi gösterimleri doğru yapılmalı.
Pin ataması ESP32'nin uygunlupu kontrol edilerek birbirine yakın pinler ile bağlanmalı. Bu layout çizimini kolaylaştırır.
Boşta kalan pinlere 22R sonrası bir test point koyarak daha sonra kullanılabilir halde tasarım yapalım.
RTC pil konusu netleştirilecek.
ESP32 decoupling kapasiteleri pin ile bağlantılı gösterilmesi layout çiziminde bunların pine yakın konumlandırılması gerektiğini hatırlatır.
BT1: L-KLS5-CR2032-05-R1 holder. CR2032 primary cell: disable RTC trickle charge. Pad 1 positive, pad 2 GND.
ESP32'yi nasıl programlayacağız? Uart pinlerini bağlamamız gerekiyor mu?
Encoder seçimi yapılarak uygun şekilde bağlantısı yapılmalı!
