gokcesena53/usb-pd-power-supply/hardware/docs/reports/backlight-20260911/before/powergeneration.kicad_sch

## KiCad design hardware/docs/reports/backlight-20260911/before/powergeneration.kicad_sch (2026-09-11)

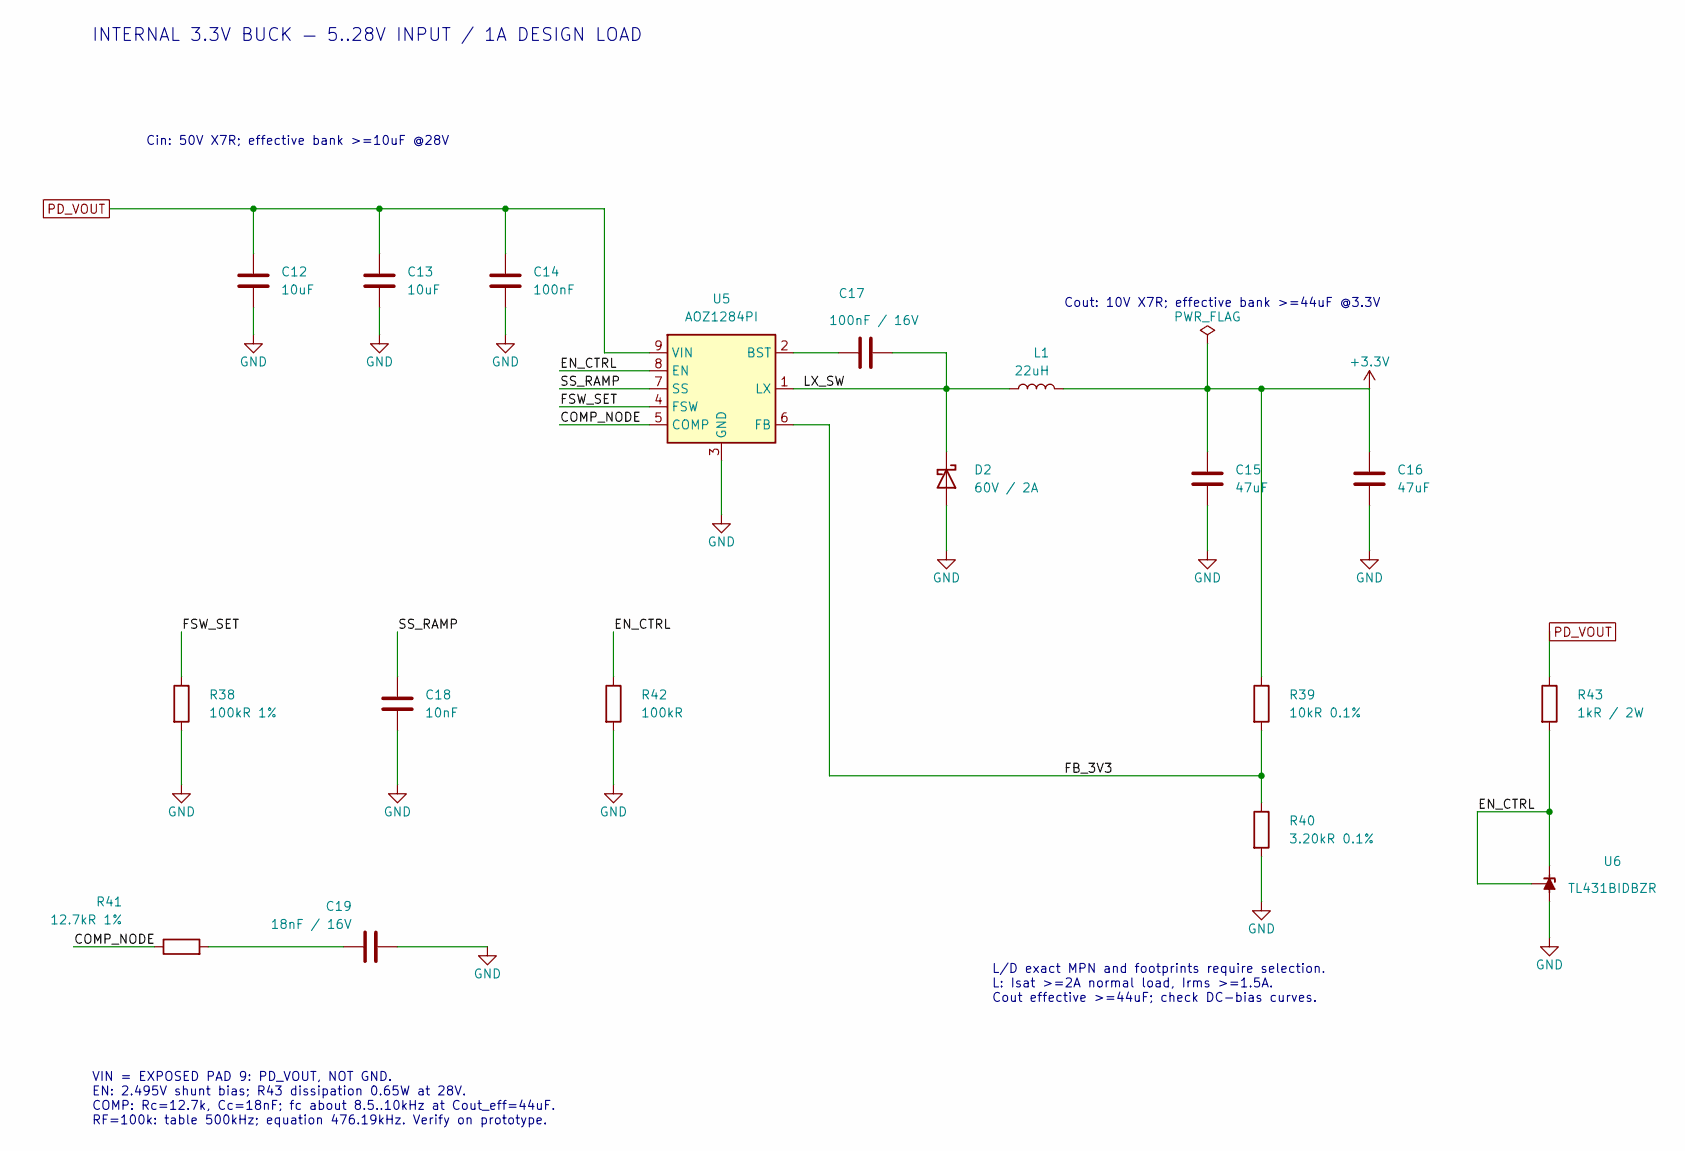
[picture p167: schematic powergeneration.kicad_sch]

Parts:
C12, C13: 10uF; C_1210_3225Metric; Voltage 50V
C14: 100nF; C_0402_1005Metric; Voltage 50V
C15, C16: 47uF; C_1210_3225Metric; Voltage 10V
C17: 100nF / 16V; C_0402_1005Metric; Voltage 16V
C18: 10nF; C_0402_1005Metric; Voltage 10V
C19: 18nF / 16V; C_0402_1005Metric
D2: 60V / 2A
L1: 22uH
R38: 100kR 1%; R_0402_1005Metric
R39: 10kR 0.1%; R_0402_1005Metric
R40: 3.20kR 0.1%; R_0402_1005Metric
R41: 12.7kR 1%; R_0402_1005Metric
R42: 100kR; R_0402_1005Metric
R43: 1kR / 2W; R_2512_6332Metric
U5: AOZ1284PI; SOIC-8-1EP_3.9x4.9mm_P1.27mm_EP2.71x3.7mm
U6: TL431BIDBZR; SOT-23

Connections:
+3.3V: C15.1, C16.1, L1.2, R39.1
COMP_NODE: R41.1, U5.5 (COMP)
EN_CTRL: R42.1, R43.2, U5.8 (EN), U6.1 (K), U6.2 (REF)
FB_3V3: R39.2, R40.1, U5.6 (FB)
FSW_SET: R38.1, U5.4 (FSW)
GND: C12.2, C13.2, C14.2, C15.2, C16.2, C18.2, C19.2, D2.2 (A), R38.2, R40.2, R42.2, U5.3 (GND), U6.3 (A)
LX_SW: C17.2, D2.1 (K), L1.1, U5.1 (LX)
unnamed: C17.1, U5.2 (BST)
unnamed: C19.1, R41.2
PD_VOUT: C12.1, C13.1, C14.1, R43.1, U5.9 (VIN)
SS_RAMP: C18.1, U5.7 (SS)

Notes on the sheet:
VIN = EXPOSED PAD 9: PD_VOUT, NOT GND. EN: 2.495V shunt bias; R43 dissipation 0.65W at 28V. COMP: Rc=12.7k, Cc=18nF; fc about 8.5..10kHz at Cout_eff=44uF. RF=100k: table 500kHz; equation 476.19kHz. Verify on prototype.
Cin: 50V X7R; effective bank >=10uF @28V
L/D exact MPN and footprints require selection. L: Isat >=2A normal load, Irms >=1.5A. Cout effective >=44uF; check DC-bias curves.
INTERNAL 3.3V BUCK — 5..28V INPUT / 1A DESIGN LOAD
Cout: 10V X7R; effective bank >=44uF @3.3V
