gokcesena53/usb-pd-power-supply/hardware/docs/reports/backlight-20260911/before/poweroutput.kicad_sch

## KiCad design hardware/docs/reports/backlight-20260911/before/poweroutput.kicad_sch (2026-09-11)

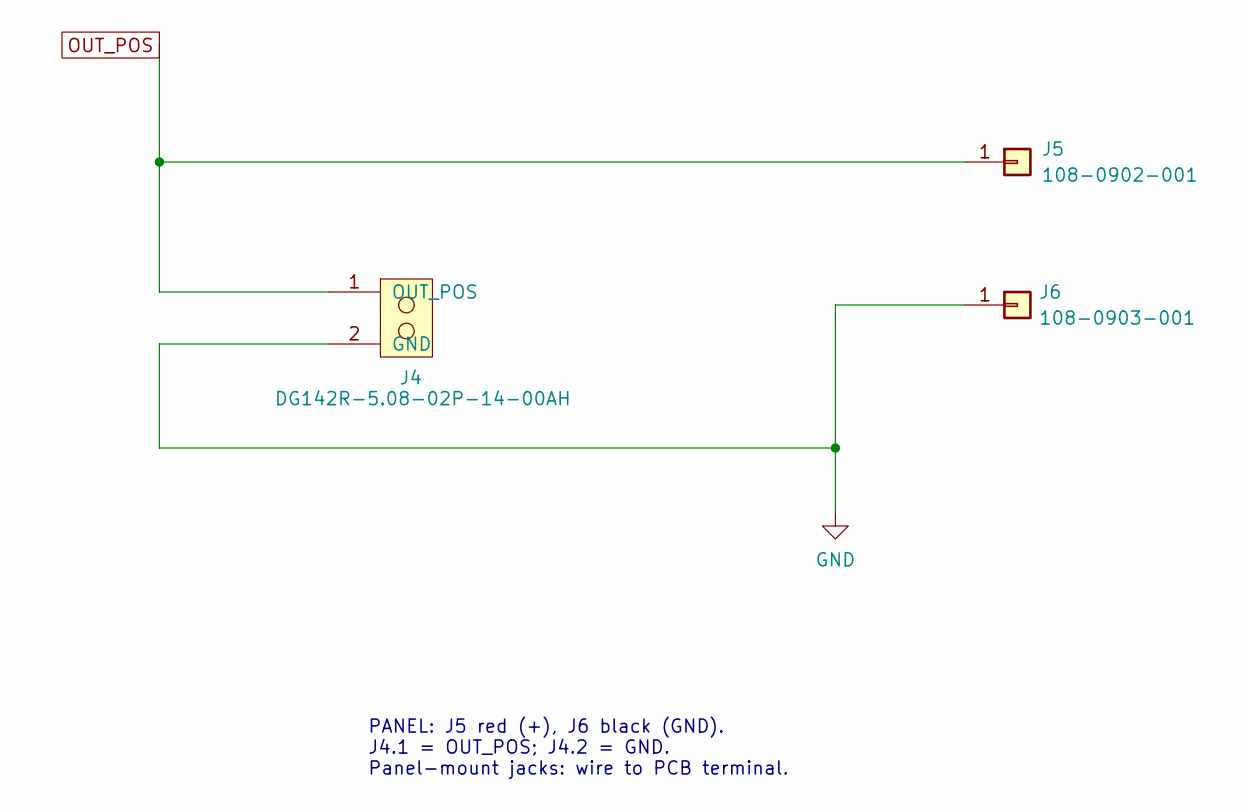
[picture p168: schematic poweroutput.kicad_sch]

Parts:
J4: DG142R-5.08-02P-14-00AH
J5: 108-0902-001; Cinch_108-0902-001_Panel; MPN 108-0902-001
J6: 108-0903-001; Cinch_108-0903-001_Panel; MPN 108-0903-001

Connections:
GND: J4.2 (GND), J6.1
OUT_POS: J4.1 (OUT_POS), J5.1

Notes on the sheet:
PANEL: J5 red (+), J6 black (GND). J4.1 = OUT_POS; J4.2 = GND. Panel-mount jacks: wire to PCB terminal.
