gokcesena53/usb-pd-power-supply/hardware/docs/reports/backlight-20260911/before/usb_pd_controller.kicad_sch

## KiCad design hardware/docs/reports/backlight-20260911/before/usb_pd_controller.kicad_sch (2026-09-11)

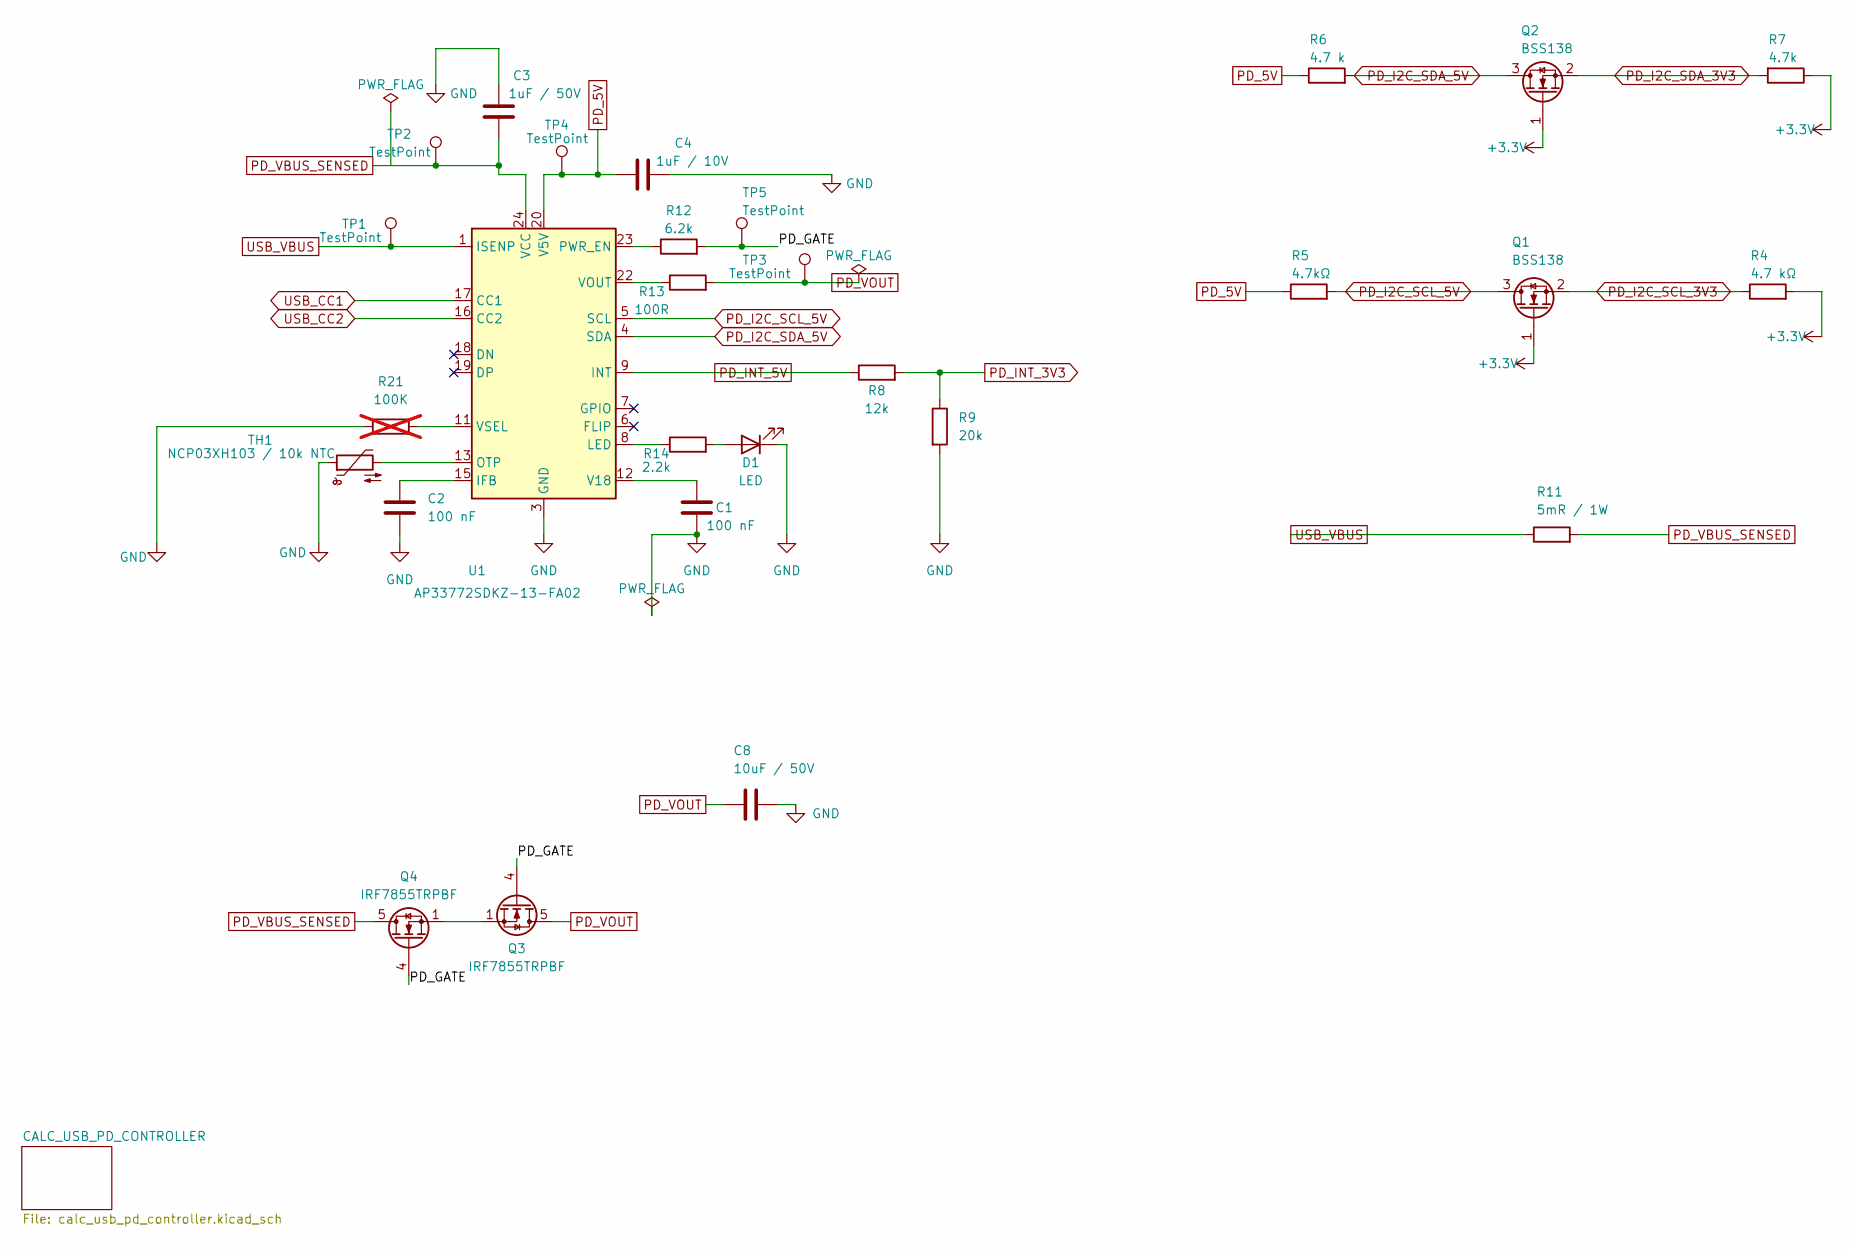
[picture p170: schematic usb_pd_controller.kicad_sch]

Parts:
C1, C2: 100 nF; C_0402_1005Metric
C3: 1uF / 50V; C_0805_2012Metric
C4: 1uF / 10V; C_0603_1608Metric
C8: 10uF / 50V; C_1210_3225Metric
D1: LED
Q1, Q2: BSS138; SOT-23
Q3, Q4: IRF7855TRPBF; SOIC-8_3.9x4.9mm_P1.27mm
R4: 4.7 kΩ; R_0402_1005Metric
R5: 4.7kΩ; R_0402_1005Metric
R6: 4.7 k; R_0402_1005Metric
R7: 4.7k; R_0402_1005Metric
R8: 12k; R_0402_1005Metric
R9: 20k; R_0402_1005Metric
R11: 5mR / 1W; R_2512_6332Metric
R12: 6.2k; R_0603_1608Metric
R13: 100R; R_0402_1005Metric
R14: 2.2k; R_0402_1005Metric
R21: 100K; R_0402_1005Metric; not fitted
TH1: NCP03XH103 / 10k NTC
TP1, TP2, TP3, TP4, TP5: TestPoint
U1: AP33772SDKZ-13-FA02; Texas_RTW_WQFN-24-1EP_4x4mm_P0.5mm_EP2.7x2.7mm

Connections:
+3.3V: Q1.1 (G), Q2.1 (G), R4.2, R7.1
GND: C1.2, C2.2, C3.2, C4.2, C8.2, D1.1 (K), R9.2, R21.1, TH1.1, U1.3 (GND), U1.25 (GND)
unnamed: C1.1, U1.12 (V18)
unnamed: C2.1, U1.15 (IFB)
unnamed: D1.2 (A), R14.2
unnamed: Q3.1 (S), Q3.2 (S), Q3.3 (S), Q4.1 (S), Q4.2 (S), Q4.3 (S)
unnamed: R12.1, U1.23 (PWR_EN)
unnamed: R13.1, U1.22 (VOUT)
unnamed: R14.1, U1.8 (LED)
unnamed: R21.2, U1.11 (VSEL)
unnamed: TH1.2, U1.13 (OTP)
PD_5V: C4.1, R5.1, R6.1, TP4.1, U1.20 (V5V)
PD_GATE: Q3.4 (G), Q4.4 (G), R12.2, TP5.1
PD_I2C_SCL_3V3: Q1.2 (S), R4.1
PD_I2C_SCL_5V: Q1.3 (D), R5.2, U1.5 (SCL)
PD_I2C_SDA_3V3: Q2.2 (S), R7.2
PD_I2C_SDA_5V: Q2.3 (D), R6.2, U1.4 (SDA)
PD_INT_3V3: R8.2, R9.1
PD_INT_5V: R8.1, U1.9 (INT)
PD_VBUS_SENSED: C3.1, Q4.5 (D), Q4.6 (D), Q4.7 (D), Q4.8 (D), R11.2, TP2.1, U1.24 (VCC)
PD_VOUT: C8.1, Q3.5 (D), Q3.6 (D), Q3.7 (D), Q3.8 (D), R13.2, TP3.1
USB_CC1: U1.17 (CC1)
USB_CC2: U1.16 (CC2)
USB_VBUS: R11.1, TP1.1, U1.1 (ISENP)
