gokcesena53/usb-pd-power-supply/hardware/docs/reports/backlight-20260911/before/userinterface.kicad_sch

## KiCad design hardware/docs/reports/backlight-20260911/before/userinterface.kicad_sch (2026-09-11)

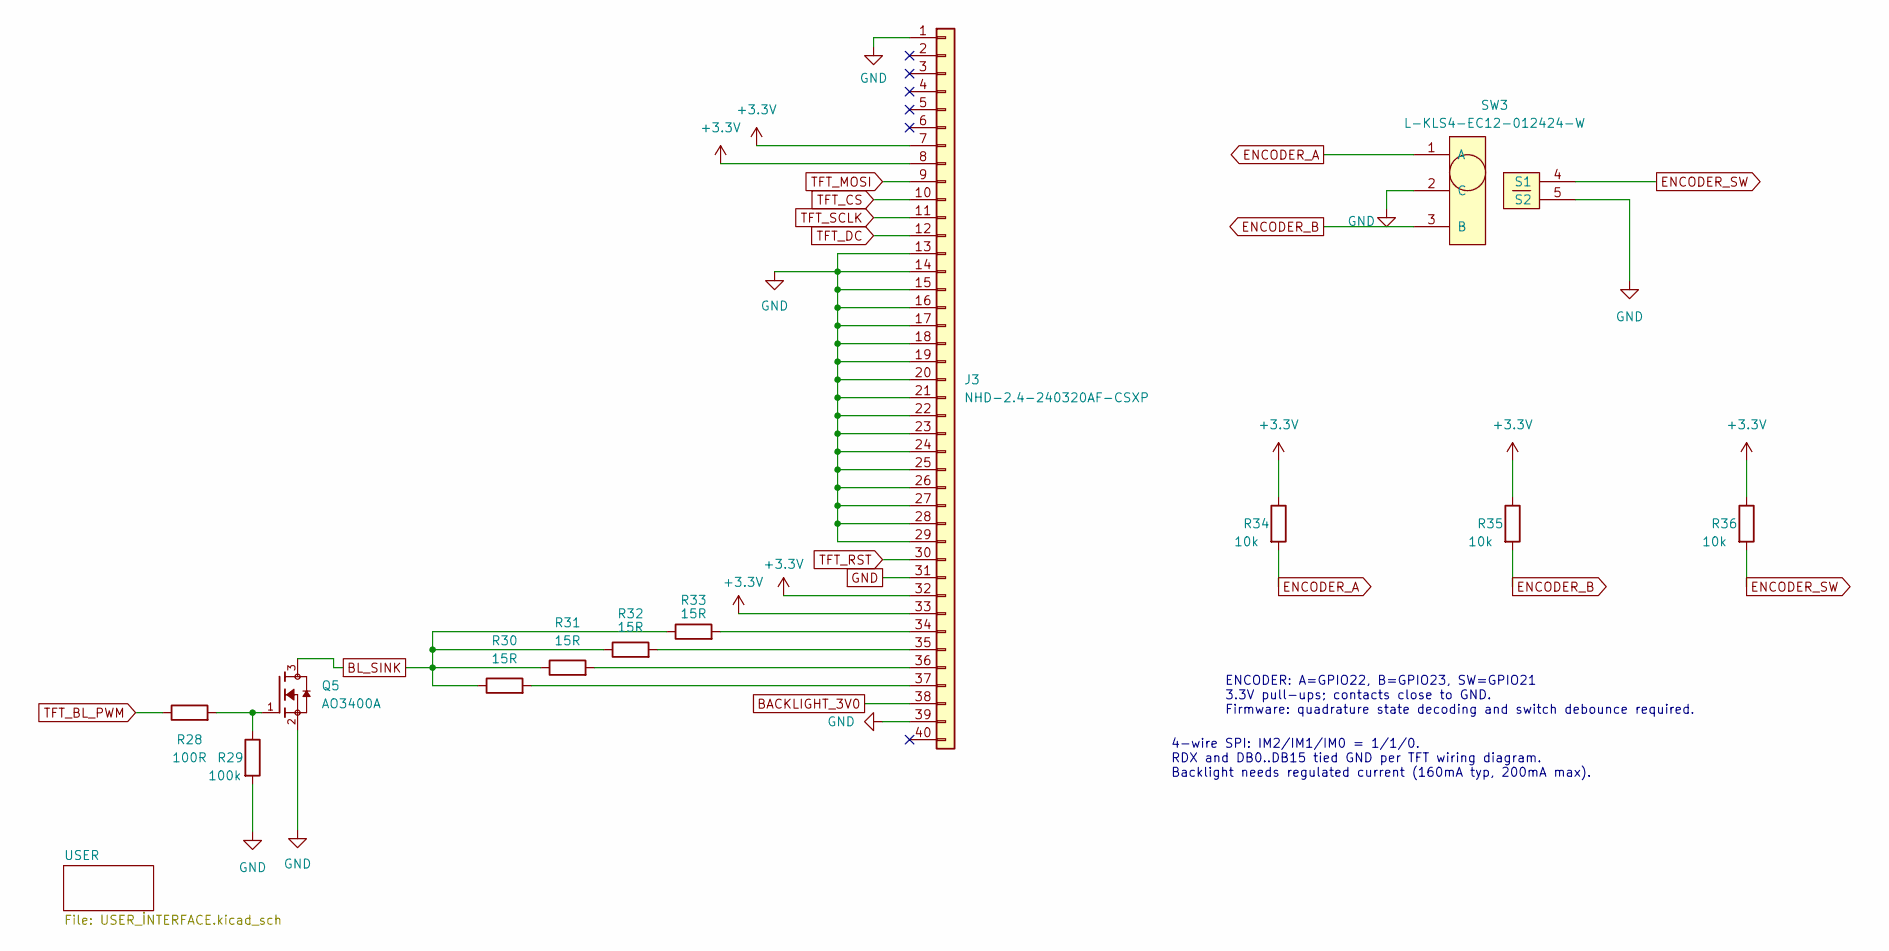
[picture p171: schematic userinterface.kicad_sch]

Parts:
J3: NHD-2.4-240320AF-CSXP; CON_541324062_MOL; MPN 54132-4062
Q5: AO3400A; SOT-23
R28: 100R; R_0402_1005Metric
R29: 100k; R_0402_1005Metric
R30, R31, R32, R33: 15R; R_0402_1005Metric
R34, R35, R36: 10k; R_0402_1005Metric
SW3: L-KLS4-EC12-012424-W

Connections:
+3.3V: J3.7, J3.8, J3.32, J3.33, R34.1, R35.1, R36.1
BACKLIGHT_3V0: J3.38
BL_SINK: R30.1, R31.1, R32.1, R33.1
ENCODER_A: R34.2, SW3.1 (A)
ENCODER_B: R35.2, SW3.3 (B)
ENCODER_SW: R36.2, SW3.4 (S1)
GND: J3.1, J3.13, J3.14, J3.15, J3.16, J3.17, J3.18, J3.19, J3.20, J3.21, J3.22, J3.23, J3.24, J3.25, J3.26, J3.27, J3.28, J3.29, J3.31, J3.39, Q5.2, R29.2, SW3.2 (C), SW3.5 (S2)
unnamed: J3.34, R33.2
unnamed: J3.35, R32.2
unnamed: J3.36, R31.2
unnamed: J3.37, R30.2
unnamed: Q5.1, R28.2, R29.1
TFT_BL_PWM: R28.1
TFT_CS: J3.10
TFT_DC: J3.12
TFT_MOSI: J3.9
TFT_RST: J3.30
TFT_SCLK: J3.11

Notes on the sheet:
ENCODER: A=GPIO22, B=GPIO23, SW=GPIO21 3.3V pull-ups; contacts close to GND. Firmware: quadrature state decoding and switch debounce required.
4-wire SPI: IM2/IM1/IM0 = 1/1/0. RDX and DB0..DB15 tied GND per TFT wiring diagram. Backlight needs regulated current (160mA typ, 200mA max).
