gokcesena53/usb-pd-power-supply/hardware/docs/reports/fixes-20260909/before/powersensing.kicad_sch

## KiCad design hardware/docs/reports/fixes-20260909/before/powersensing.kicad_sch (2026-09-10)

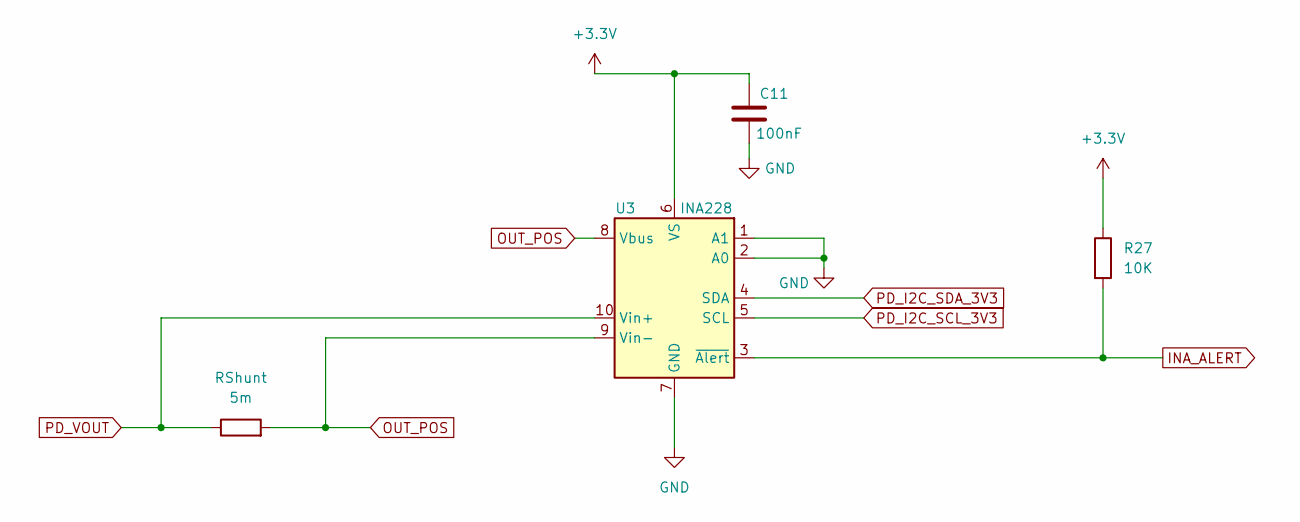
[picture p172: schematic powersensing.kicad_sch]

Parts:
C11: 100nF; C_01005_0402Metric
R27: 10K; R_01005_0402Metric
RShunt: 5m; R_01005_0402Metric
U3: INA228; TSSOP-10_3x3mm_P0.5mm

Connections:
+3.3V: C11.1, R27.1, U3.6 (VS)
GND: C11.2, U3.1 (A1), U3.2 (A0), U3.7 (GND)
INA_ALERT: R27.2, U3.3 (~Alert)
OUT_POS: RShunt.2, U3.8 (Vbus), U3.9 (Vin-)
PD_I2C_SCL_3V3: U3.5 (SCL)
PD_I2C_SDA_3V3: U3.4 (SDA)
PD_VOUT: RShunt.1, U3.10 (Vin+)
