gokcesena53/usb-pd-power-supply/hardware/docs/reports/fixes-20260909/before/userinterface.kicad_sch

## KiCad design hardware/docs/reports/fixes-20260909/before/userinterface.kicad_sch (2026-09-10)

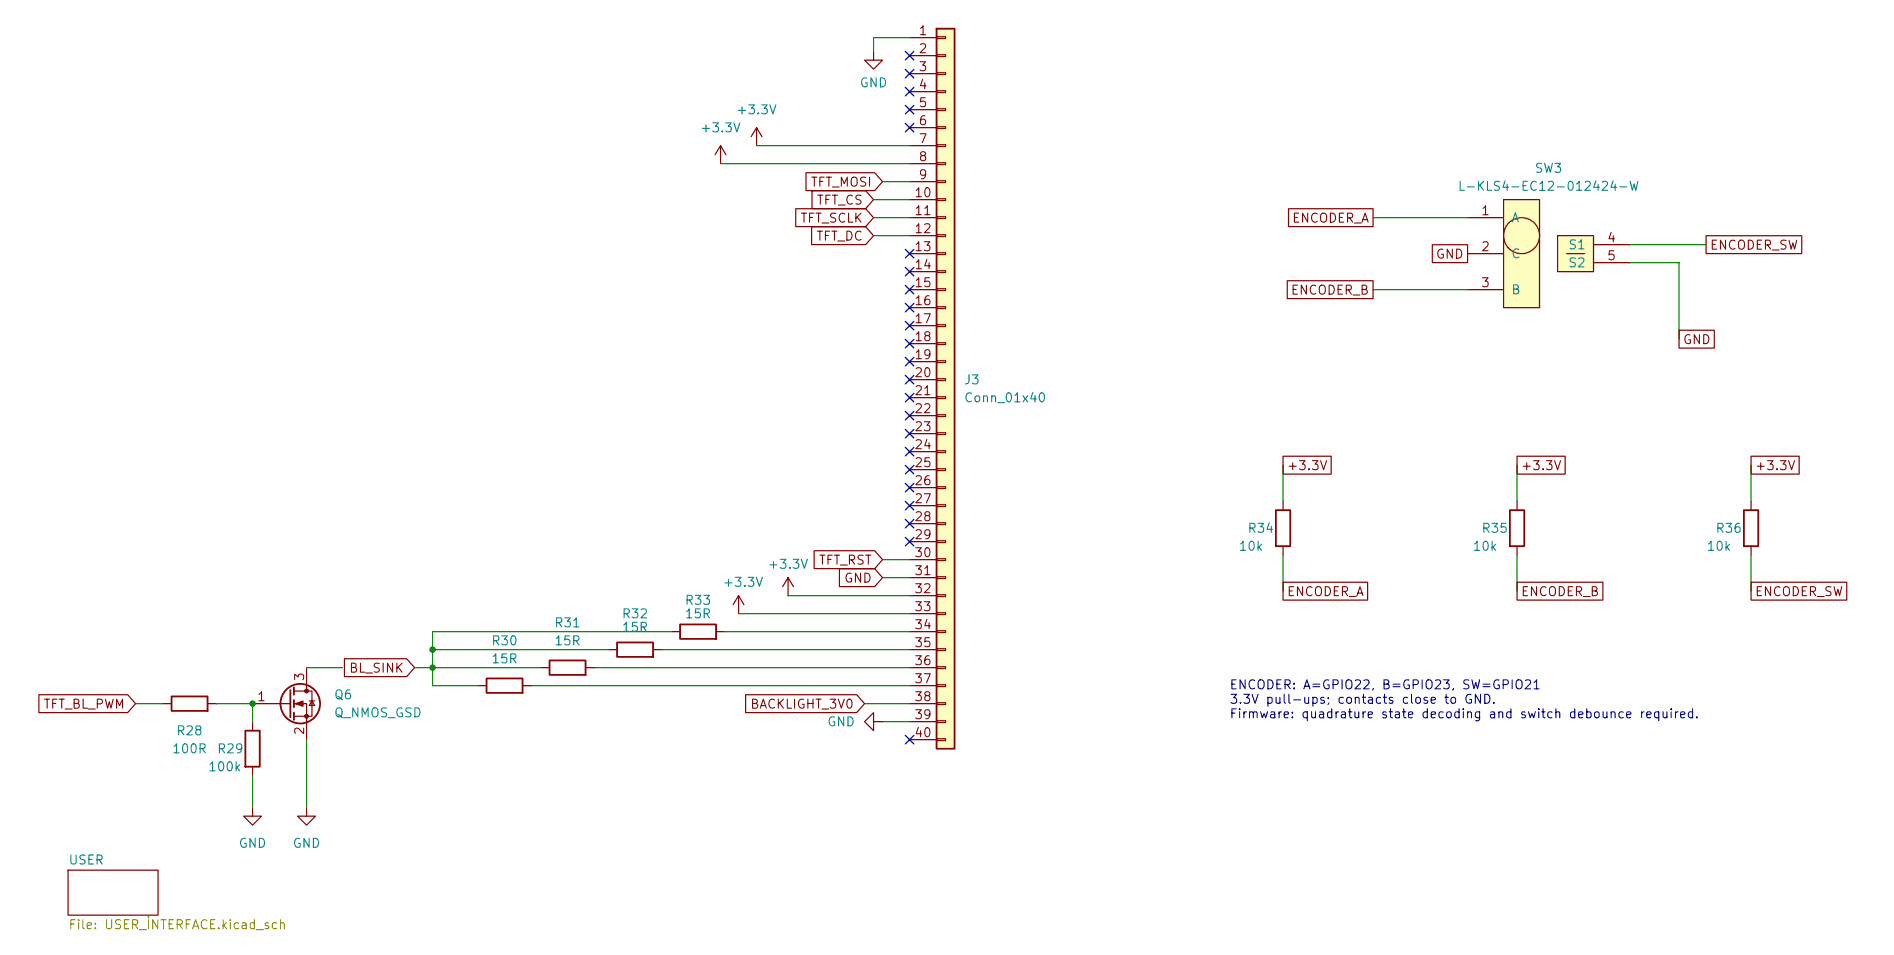
[picture p173: schematic userinterface.kicad_sch]

Parts:
J3: Conn_01x40; CON_541324062_MOL
Q6: Q_NMOS_GSD
R28: 100R; R_01005_0402Metric
R29: 100k; R_01005_0402Metric
R30, R31, R32, R33: 15R; R_01005_0402Metric
R34, R35, R36: 10k; R_0603_1608Metric
SW3: L-KLS4-EC12-012424-W

Connections:
+3.3V: J3.7, J3.8, J3.32, J3.33, R34.1, R35.1, R36.1
BACKLIGHT_3V0: J3.38
BL_SINK: R30.1, R31.1, R32.1, R33.1
ENCODER_A: R34.2, SW3.1 (A)
ENCODER_B: R35.2, SW3.3 (B)
ENCODER_SW: R36.2, SW3.4 (S1)
GND: J3.1, J3.31, J3.39, Q6.2 (S), R29.2, SW3.2 (C), SW3.5 (S2)
unnamed: J3.34, R33.2
unnamed: J3.35, R32.2
unnamed: J3.36, R31.2
unnamed: J3.37, R30.2
unnamed: Q6.1 (G), R28.2, R29.1
TFT_BL_PWM: R28.1
TFT_CS: J3.10
TFT_DC: J3.12
TFT_MOSI: J3.9
TFT_RST: J3.30
TFT_SCLK: J3.11

Notes on the sheet:
ENCODER: A=GPIO22, B=GPIO23, SW=GPIO21 3.3V pull-ups; contacts close to GND. Firmware: quadrature state decoding and switch debounce required.
