gokcesena53/usb-pd-power-supply/hardware/docs/reports/output-update/before/poweroutput.kicad_sch

## KiCad design hardware/docs/reports/output-update/before/poweroutput.kicad_sch (2026-09-10)

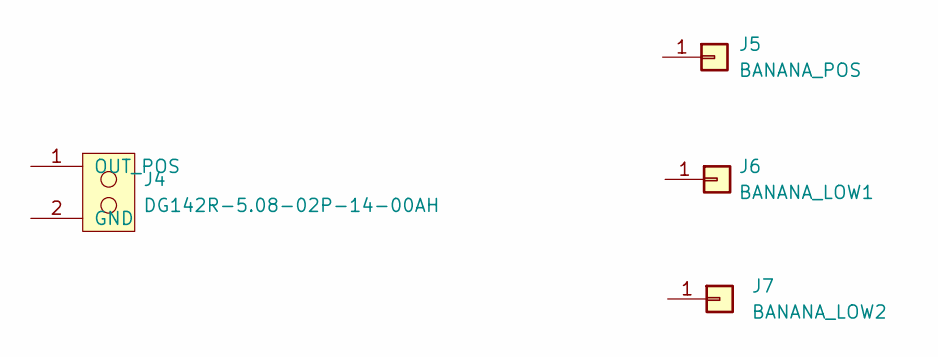
[picture p174: schematic poweroutput.kicad_sch]

Parts:
J4: DG142R-5.08-02P-14-00AH
J5: BANANA_POS
J6: BANANA_LOW1
J7: BANANA_LOW2
