gokcesena53/usb-pd-power-supply/hardware/docs/reports/recheck-20260911/before/poweroutput.kicad_sch

## KiCad design hardware/docs/reports/recheck-20260911/before/poweroutput.kicad_sch (2026-09-11)

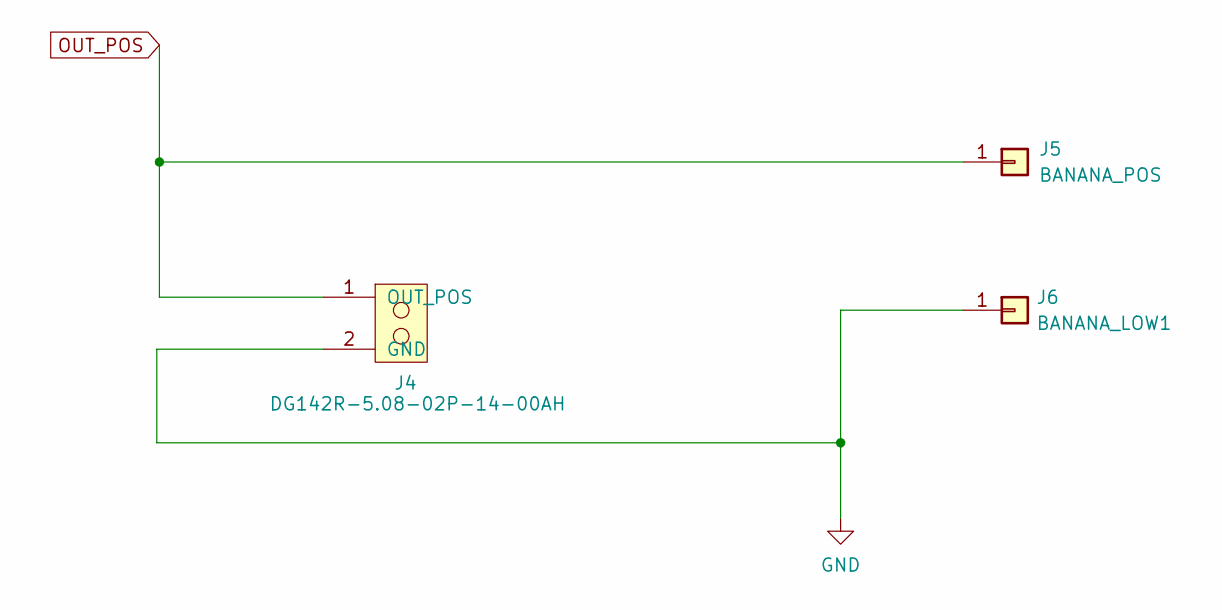
[picture p175: schematic poweroutput.kicad_sch]

Parts:
J4: DG142R-5.08-02P-14-00AH
J5: BANANA_POS
J6: BANANA_LOW1

Connections:
GND: J4.2 (GND), J6.1
OUT_POS: J4.1 (OUT_POS), J5.1
