gokcesena53/usb-pd-power-supply/hardware/docs/reports/review-20260910/before/powergeneration.kicad_sch

## KiCad design hardware/docs/reports/review-20260910/before/powergeneration.kicad_sch (2026-09-10)

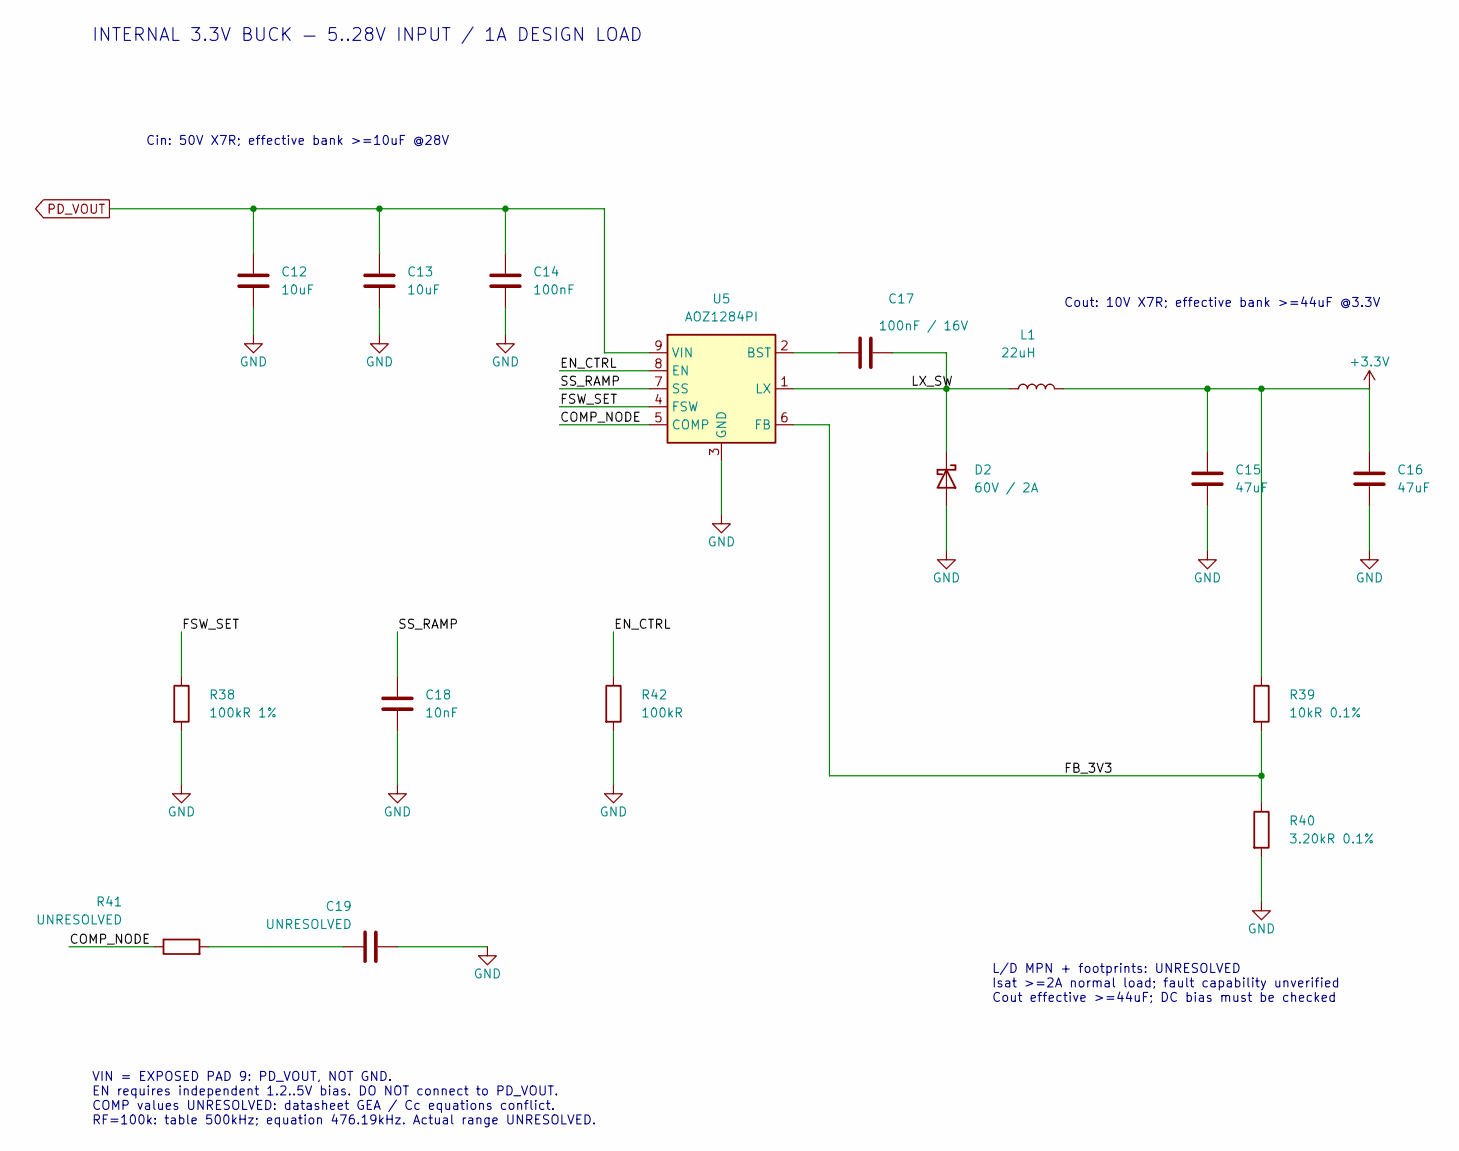
[picture p176: schematic powergeneration.kicad_sch]

Parts:
C12, C13: 10uF; C_1210_3225Metric; Voltage 50V
C14: 100nF; C_0603_1608Metric; Voltage 50V
C15, C16: 47uF; C_1210_3225Metric; Voltage 10V
C17: 100nF / 16V; C_0603_1608Metric; Voltage 16V
C18: 10nF; C_0603_1608Metric; Voltage 10V
C19: UNRESOLVED; C_0603_1608Metric
D2: 60V / 2A
L1: 22uH
R38: 100kR 1%; R_0603_1608Metric
R39: 10kR 0.1%; R_0603_1608Metric
R40: 3.20kR 0.1%; R_0603_1608Metric
R41: UNRESOLVED; R_0603_1608Metric
R42: 100kR; R_0603_1608Metric
U5: AOZ1284PI; SOIC-8-1EP_3.9x4.9mm_P1.27mm_EP2.71x3.7mm

Connections:
+3.3V: C15.1, C16.1, L1.2, R39.1
COMP_NODE: R41.1, U5.5 (COMP)
EN_CTRL: R42.1, U5.8 (EN)
FB_3V3: R39.2, R40.1, U5.6 (FB)
FSW_SET: R38.1, U5.4 (FSW)
GND: C12.2, C13.2, C14.2, C15.2, C16.2, C18.2, C19.2, D2.2 (A), R38.2, R40.2, R42.2, U5.3 (GND)
LX_SW: C17.2, D2.1 (K), L1.1, U5.1 (LX)
unnamed: C17.1, U5.2 (BST)
unnamed: C19.1, R41.2
PD_VOUT: C12.1, C13.1, C14.1, U5.9 (VIN)
SS_RAMP: C18.1, U5.7 (SS)

Notes on the sheet:
VIN = EXPOSED PAD 9: PD_VOUT, NOT GND. EN requires independent 1.2..5V bias. DO NOT connect to PD_VOUT. COMP values UNRESOLVED: datasheet GEA / Cc equations conflict. RF=100k: table 500kHz; equation 476.19kHz. Actual range UNRESOLVED.
Cin: 50V X7R; effective bank >=10uF @28V
L/D MPN + footprints: UNRESOLVED Isat >=2A normal load; fault capability unverified Cout effective >=44uF; DC bias must be checked
INTERNAL 3.3V BUCK — 5..28V INPUT / 1A DESIGN LOAD
Cout: 10V X7R; effective bank >=44uF @3.3V
