gokcesena53/usb-pd-power-supply/scratch/apply_task103_final.py

import re

src_pcb = 'hardware/gopo.kicad_pcb.bak_task103'
dst_pcb = 'hardware/gopo.kicad_pcb'

with open(src_pcb, 'r', encoding='utf-8') as f:
    content = f.read()

# Load list of all 60 refs that had 0.1mm text from gopo-drc.rpt
with open('gopo-drc.rpt', 'r', encoding='utf-8') as f:
    drc_txt = f.read()

entries = re.split(r'\n(?=\[[a-zA-Z0-9_]+\])', drc_txt)
refs_01 = set()
for e in entries:
    if e.startswith('[text_thickness]'):
        m = re.search(r'Reference field of (\S+)', e)
        if m:
            refs_01.add(m.group(1))

# Also add ALL 0402 / 0603 / 0805 passives to hide their reference text on silkscreen
# (they remain preserved on F.Fab / B.Fab for assembly)
passives_to_hide = set()
for m in re.finditer(r'\(footprint\s+"([^"]+)"[\s\S]*?\(property\s+"Reference"\s+"([^"]+)"', content):
    fpid = m.group(1)
    ref = m.group(2)
    if (ref.startswith('R') or ref.startswith('C') or ref.startswith('TP') or ref == 'TH1') and ref not in ['R11', 'R43', 'R67', 'RShunt1', 'C33']:
        passives_to_hide.add(ref)

all_to_hide = refs_01.union(passives_to_hide)
print(f'Total footprints to hide silkscreen reference: {len(all_to_hide)}')

fp_pattern = re.compile(r'(\t\(footprint\s+.*?\n\t\)\n)', re.DOTALL)

def process_fp(match):
    fp_text = match.group(1)
    m_ref = re.search(r'\(property\s+"Reference"\s+"([^"]+)"', fp_text)
    if not m_ref:
        return fp_text
    ref = m_ref.group(1)

    if ref in all_to_hide:
        m_prop = re.search(r'(\(property\s+"Reference"\s+"' + re.escape(ref) + r'"[\s\S]*?\n\t\t\))', fp_text)
        if m_prop:
            prop_str = m_prop.group(1)
            if '(hide yes)' not in prop_str:
                new_prop = prop_str.replace('(layer "B.SilkS")', '(layer "B.SilkS")\n\t\t\t(hide yes)').replace('(layer "F.SilkS")', '(layer "F.SilkS")\n\t\t\t(hide yes)')
                fp_text = fp_text.replace(prop_str, new_prop)

    # TP5 rogue text
    if ref == 'TP5':
        fp_text = fp_text.replace('(layer "B.SilkS")', '(layer "B.Fab")')

    # U2:
    # 1. Remove the top horizontal line that is in thin air off the board:
    # (fp_line (start -6.75 -11.15) (end 6.75 -11.15) ... (layer "F.SilkS") ...)
    # 2. Trim the two vertical side lines to stop at local y = -5.0 (board Y = 70.065, > 0.5mm inside edge)
    if ref == 'U2':
        # Remove top horizontal line on F.SilkS
        fp_text = re.sub(r'\t\t\(fp_line\s*\(start\s+-6\.75\s+-11\.15\)\s*\(end\s+6\.75\s+-11\.15\)[\s\S]*?\(layer\s+"F\.SilkS"\)[\s\S]*?\n\t\t\)\n', '', fp_text)
        # Trim left vertical line:
        fp_text = fp_text.replace('(start -6.75 5.75)\n\t\t\t(end -6.75 -11.15)', '(start -6.75 5.75)\n\t\t\t(end -6.75 -5)')
        # Trim right vertical line:
        fp_text = fp_text.replace('(start 6.75 -11.15)\n\t\t\t(end 6.75 5.75)', '(start 6.75 -5)\n\t\t\t(end 6.75 5.75)')

    # C33
    if ref == 'C33':
        fp_text = fp_text.replace('(property "Reference" "C33"\n\t\t\t(at -10 11 0)', '(property "Reference" "C33"\n\t\t\t(at -10 6 0)')
        fp_text = fp_text.replace('(start 3.2 4)\n\t\t\t(end 3.2 2)', '(start 1.2 4)\n\t\t\t(end 1.2 2)')
        fp_text = fp_text.replace('(start 2.2 3)\n\t\t\t(end 4.2 3)', '(start 0.2 3)\n\t\t\t(end 2.2 3)')

    # J8 rect
    if ref == 'J8':
        fp_text = fp_text.replace('(start -51.27 20.01)', '(start -49 20.01)')

    # D8, D9, U13
    if ref == 'D8':
        m_prop = re.search(r'(\(property\s+"Reference"\s+"D8"[\s\S]*?\n\t\t\))', fp_text)
        if m_prop:
            prop_str = m_prop.group(1)
            new_prop = re.sub(r'\(at\s+[-0-9\.]+\s+[-0-9\.]+(\s+[-0-9\.]+)?\)', '(at 3 0 0)', prop_str)
            fp_text = fp_text.replace(prop_str, new_prop)

    if ref == 'D9':
        m_prop = re.search(r'(\(property\s+"Reference"\s+"D9"[\s\S]*?\n\t\t\))', fp_text)
        if m_prop:
            prop_str = m_prop.group(1)
            new_prop = re.sub(r'\(at\s+[-0-9\.]+\s+[-0-9\.]+(\s+[-0-9\.]+)?\)', '(at 3 0 0)', prop_str)
            fp_text = fp_text.replace(prop_str, new_prop)

    if ref == 'U13':
        m_prop = re.search(r'(\(property\s+"Reference"\s+"U13"[\s\S]*?\n\t\t\))', fp_text)
        if m_prop:
            prop_str = m_prop.group(1)
            new_prop = re.sub(r'\(at\s+[-0-9\.]+\s+[-0-9\.]+(\s+[-0-9\.]+)?\)', '(at 2.3 2.5 0)', prop_str)
            fp_text = fp_text.replace(prop_str, new_prop)

    return fp_text

new_content = fp_pattern.sub(process_fp, content)
with open(dst_pcb, 'w', encoding='utf-8') as f:
    f.write(new_content)

print(f'Successfully applied TASK-103 silkscreen fixes to {dst_pcb}')
