gokcesena53/usb-pd-power-supply/scratch/check_j8_crtyd.py

import re
import sys

sys.stdout.reconfigure(encoding='utf-8')

with open('hardware/gopo.kicad_pcb', 'r', encoding='utf-8') as f:
    pcb = f.read()

parts = re.split(r'\n\s*\(footprint\s+', pcb)
for p in parts[1:]:
    if re.search(r'\(property\s+"Reference"\s+"J8"', p):
        lines = p.splitlines()
        for i, l in enumerate(lines):
            if 'B.CrtYd' in l:
                for j in range(max(0, i-10), min(len(lines), i+2)):
                    print(lines[j])
